Dr-Crow/esphome-ge-laundry-uart/case/rev3c/analytical/README.md

# Parametric Rev3C enclosure review

This is an editable analytical derivative of the [recovered prototype](../prototype/). It keeps a common base, module-specific C3/C6 lids and three light guides. The selected carrier outline and both appliance power inputs are preserved. The four lids support internal/external antenna concepts; exact cable, switch and printed-assembly qualification remains open.

**Use review exports for dimensional review and coupons. They are not approved production files.** Fixed original button reaches fail nominal actuation at an installed stack of 11.0 mm. The common closure permits a wrong lid: a C3 BOOT foot can contact C6 U.FL. Check the module label before assembly; labels do not mechanically prevent this mistake.

The [source-bound report](review/CASE-ANALYSIS.md) records valid solids, installed-stack samples, component envelopes, actual guide routes, plug gauges and antenna provisions. Analytical geometry was generated with build123d 0.10.0 / cadquery-ocp 7.8.1.1.post1. The original analysis used a different toolchain from the recovered historical requirements; the subsequent pinned reproduction is recorded below. These versioned checks are not physical fit, material or RF tests.

The [subsequent pinned reproduction](review/pinned-reproduction/GE-Pinned-CAD-Reproduction-2026-10-05.md) closes that setup/reproduction limitation for the frozen 77f4c88 source. build123d 0.11.1/trimesh 5.1.0 produces 51 independently checked STEP/STL pairs, and the 20 nominal shape comparisons and 12 stack samples agree with the prior engine. The original two top-level requirements do not establish the old transitive dependency closure; all 47 packages used in the new run are recorded. Future parameter/source changes require their own checks. Printed fit and physical qualification remain open.

## Reviewable corrections

- `configure()` sets the declared generic installed stack from 10.35 to 11.65 mm, independent BOOT/RESET heights, gaps and stops, plus optional stack-adjusted USB height. It does not establish a safe switch overtravel limit.
- A separate C3 leaf-root offset of 17.3 mm, instead of 16.6 mm, lowers the nominal fixed-guided strain screen to 0.427–0.495%. This meets the stated example screen, with material/fatigue and tolerance margin still unproved.
- `pipe_with_cap_relief()` removes only local lower crescents near manufacturer maximum capacitor bodies. The chosen 0.15 mm solder-lift allowance and 0.25 mm clearance are design requirements. The nominal LED inlet projection, upper path and roof retention stay unchanged; reduced inlet area needs optical/print testing.

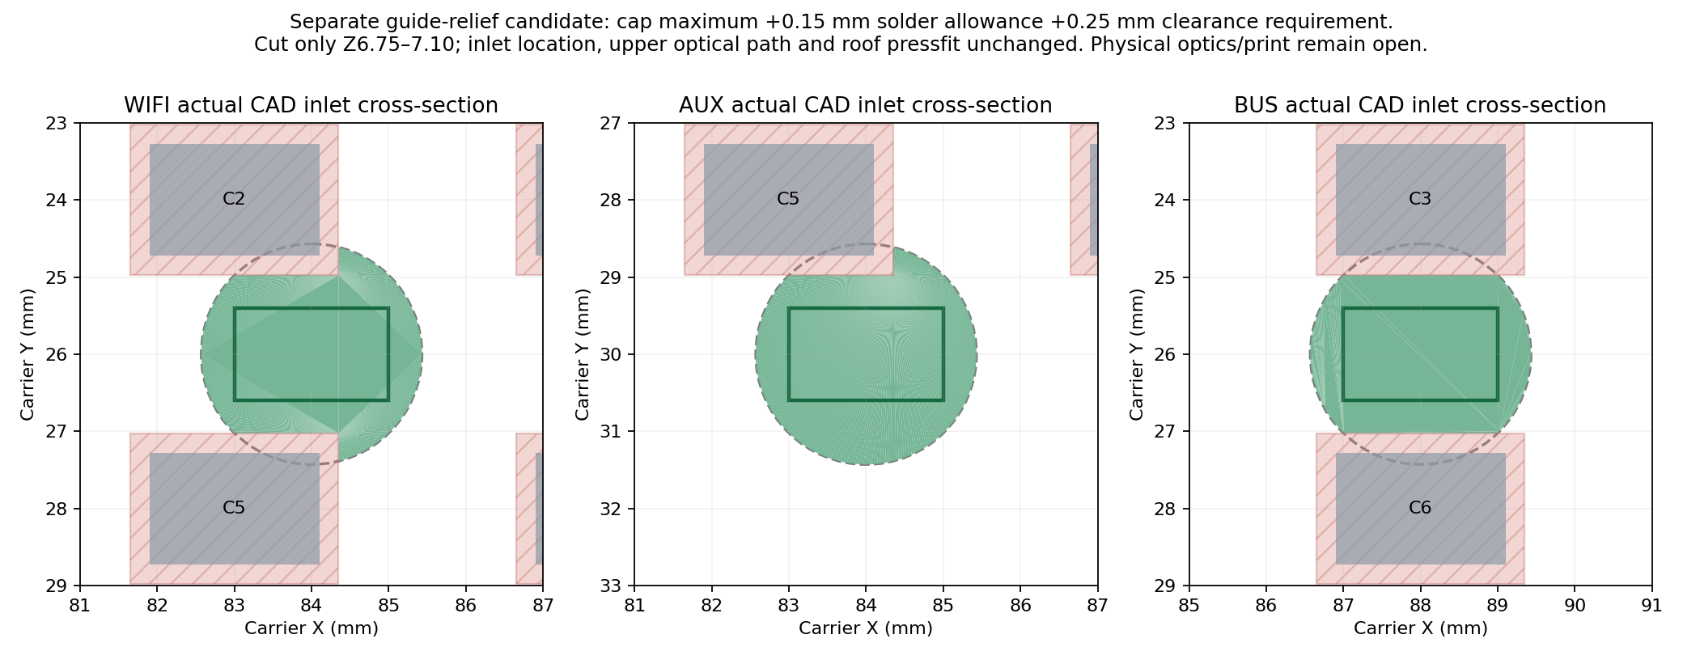
[picture p13: case/rev3c/analytical/review/guide-relief-candidate.png]
Guide relief and preserved LED inlet


## Explicit review export

Use an existing authorized installation of the recorded analysis tools. `export_review.py` requires an explicit module, stack and switch/stop dimensions so a known-bad default is not silently presented as a print-ready assembly. An illustrative C3 command is:

```sh
python export_review.py --module c3 --stack 11.325 \
  --boot-height 1.5 --reset-height 1.5 --boot-stop 0.4 --reset-stop 0.4 \
  --leaf-offset 17.3 --relieved-guides --output exports-review-c3
```

Those are conditional analytical parameters, not measured switch limits or a recommended production calibration. For C6, use its separately verified switch identity and dimensions. The report's 0.53 ±0.10 mm C6 height remains conditional; the nominal 0.36 mm stop is not a manufacturer overtravel allowance. The export includes the explicit parameter/source receipt and five review pieces. Extra coupons or proxy electronics are excluded from that five-piece set.

## Current dimension review

The [October 5 dimensions review](MECHANICAL-DIMENSIONS.md) binds socket maximum dimensions, the full declared 10.35–11.65 mm assumed-stack range, conditional switch identities and the named StarTech USB2CC2M cable. Its 12.2 × 6.5 mm maximum overmold exceeds the old synthetic gauge. The actual fitted header, C6 switch identity and native USB mating coordinates remain unresolved.

The [named cable tool and sensitivity receipts](review/cable-corridor/README.md) require explicit shoulder/axis coordinates and retain the source uncertainty. Named switch-height references are also available without changing the fitted default.

## Open assembly checks

The historical maximum-body and base/lid screens cleared at three sampled stacks within 11.0–11.65 mm. The [subsequent source-bound endpoint check](review/socket-stack-endpoints.json) passes eight C3/C6 × internal/external × lower/upper cases with maximum socket bodies and conditional switch-height extremes. All have zero nominal component/base-lid intersections and 0.25 mm released button gaps. Four lower-end lids also pass STEP single-solid and untouched watertight STL readback. These are explicit review parameters, not factory seating or safe-actuation proof. A 12 ×6 mm synthetic USB plug gauge clears; a 14 ×8 mm gauge fails the rounded aperture. Choose a real plug and verify shank depth, strain relief, insertion and finger/latch access. Antenna maximum slabs and nominal bulkhead hardware clear their stated screens, while cable terminations, bend/slack, panel tolerance and RF remain open.

Before fitting a board, verify the actual male/female header seating and retention, both switch make/overtravel/force specifications, wrong-lid prevention, slicer/coupon clearances, light transmission and actual antenna/plug envelopes. Leave UART VCC disconnected. Disconnect the appliance cable before powered USB. The 40 V switch selection is not a 40 V rating for the complete carrier.
