Dr-Crow/esphome-ge-laundry-uart/pcb/rev3/production/README.md

# Rev3A quote package

This directory is a quote and prototype artifact, not production authorization.
Upload the matching Gerber ZIP, BOM, and CPL as one revisioned set.

- `GERBER-GEA-Adapter-Rev3A.zip`
- `BOM-GEA-Adapter-Rev3A.csv`
- `CPL-GEA-Adapter-Rev3A.csv`

- The Gerber ZIP defines copper, solder mask, silkscreen, board outline, and
  plated/non-plated drills.
- The BOM maps fitted references to exact parts and quantities.
- The CPL supplies fitted-part coordinates, side, and rotation using JLCPCB's
  documented `Designator`, `Mid X`, `Mid Y`, `Rotation`, and `Layer` headers.

A valid turnkey upload must show all 43 BOM groups and all 91 placements selected
for assembly. Stop if the vendor marks any fitted row "do not place" or reports an
unselected part. The pre-J2 2026-09-15 match used stocked Yageo `C106243` and
`C91185` capacitors in place of unavailable `C28233` and `C28323`, while retaining
the available original `C17414` resistors and `C151607` buffers. Five boards quoted
at $141.24 before shipping and tax ($28.25 each). That price covered 42 groups / 90
placements. Based on J2's 2026-09-15 $0.05 catalog price, one $3 Extended-component
fee, and 30 additional SMT joints, the updated package is estimated at $144.54 total
($28.91 each) before shipping and tax. Refresh the upload to replace that arithmetic
estimate with a vendor quote. Review every replacement against
the original electrical ratings, package, pinout, temperature rating, and
manufacturer data; stock and pricing remain quote-time values.

J1 is the appliance-facing, through-hole EVERCOM `5301-8P8C` connector. A turnkey
quote must include it and show the correct orientation and through-hole assembly
method. DNP service/test items are intentionally excluded from BOM and CPL.

J2 is the populated top-side hanxia `HX PZ-2.54-02-03-S-PB3.2` (`C42391552`)
2-by-3 recovery header. The vendor preview must show it installed on the top side at
the lower-left recovery location. J3 remains a schematic-only DNP alternate and is
excluded from BOM and CPL.

J4 is the SHOU HAN `TYPE-C 16PIN 2MD(073)` (`C2765186`) USB-C receptacle. Its
official drawing was checked against the placed KiCad land pattern before the
live Economic Assembly quote. The vendor preview must still confirm its position
and orientation.

The PCB is 88.7 mm by 40.0 mm with four copper layers. The Gerber set must contain
`F.Cu`, `In1.Cu`, `In2.Cu`, and `B.Cu`; both inner layers are solid GND planes.
The plated drill file has a 0.30 mm minimum: twelve 0.30 mm drills connect U2's
thermal-ground pad, while routed vias use 0.40 mm drills. Quote this as standard
FR4 TG135 with the 0.30 mm minimum-hole option and ordinary electrical testing.
Stop if the upload requests a small-hole, high-Tg, filled-via, or four-wire Kelvin
process; those options are not required by this design and indicate a file or quote
configuration mismatch.

Do not order or connect a board to an appliance until the owner reviews the vendor
board, drill, parts, and placement previews. After fabrication, the current-limited
checks in [BRINGUP.md](../BRINGUP.md) must prove USB operation, all eight power-source
states, reverse-current isolation, regulator headroom, rail stability, temperature,
transient behavior, enclosure fit, and installed Wi-Fi performance.
