Dr-Crow/esphome-ge-laundry-uart/docs/revision-comparison/FINISH-PLAN.md

# Finish plan and outstanding work

Latest October 5 pre-order analysis and committed fixes: [all-revision review](preorder-2026-10-05/README.md). Earlier checkpoint/quote/source boundaries below remain explicit.

[Comparison](README.md) · [Current validation](VALIDATION.md) · [Exact checkpoints](HANDOFF.md) · [Quote comparison](PRICING.md)

Updated October 5, 2026 after shared-enclosure source recovery. Selected Rev3C retains the rated electrical design, corrected J1 CPL and stencil cleanup from `b87d3e8`; its fresh exact-part quote is $134.64/5 and $168.92/10. Published integration checkpoint `11826a7` passes hosted native/intended-rule checks for all seven revisions, 28 tests and eight actual firmware builds. Rev3B protection is reviewed at `ce2979b`; Rev3A rated protection and exact connector lands remain independently reviewed. Older revisions retain their separate architectures. The [Rev3C prototype qualification plan](../../pcb/rev3c/PROTOTYPE-QUALIFICATION.md) gives the next bounded sequence; orders, physical testing, PRs and upstream publication remain separate decisions.

## Current Rev3 milestone and remaining work

The [current refinement](preorder-2026-10-05/README.md#current-rev3-refinement-checkpoint) applies STPS140Z D14/D15 to all A/B/C and maximum-body socket/case corrections to C. Exact bf5c231 passes native KiCad 9.0.9, intended rules, 38 tests and eight firmware builds. Current-ST C quotes are $135.81/five and $171.20/ten; older A/B/C quote records below retain their original sources. A refresh is complete at $180.08/five or $230.15/ten, including its WROOM; B remains blocked only by exact-module stock, without a full assembled total. Future engineering is Rev3-only; prior Rev1/Rev2.x history and unresolved findings remain preserved, and upstream Rev2.2 receives no new redesign.

Feasible analytical work now completed includes source/purchasing corrections, current numbered signal nets, named switch-height references, full assumed stack endpoints, maximum socket courtyards, explicit-coordinate USB cable screening and a preserved separate plastic pair-key option. Remaining vendor inputs are actual factory header/module/switch revision, engagement/retention/make/overtravel limits, native USB mating coordinates and the buffer's output-range clarification. Common versus keyed base/lid pairs is a user choice; the latter requires changing both base and lid when switching module family.

OEM source/current/fault and loaded-voltage/thermal/RF/print/optical/assembly qualification remain distinct physical gates. Larger fuses, current-limit changes, fault-aware priority, regulators or added USB hardware are not silently adopted. Both appliance inputs and existing automatic priority stay required. Current supplier pose, solder/paste and process approval remains open.

## Historical checkpoint registry

| Work | Current checkpoint | Closeout evidence | State |
| --- | --- | --- | --- |
| Selected Rev3C final source package | 83-reference source; native/intended-rule/CAM/BOM/CPL checks pass; corrected-stencil exact-part quote refreshed October 5; partial C3/C6 models preserved | Final source/export hashes, intended-netclass and antenna proofs, supplier placement/process review; qualify switch/fuse/TVS/gate/diode/buck/module chain | Digital package and quote available; electrical/physical release blocked |
| Common C3/C6 enclosure | [Editable all-printed source](../../case/rev3c/README.md) recovered; useful XY datums and intact exports, historical electronic proxies and conflicting provisional Z assumptions | Register selected component envelopes; calibrate actual socket/module/button heights, printing, retention, USB/RJ45, antenna/pigtail clearance and fit | Source recovered; current-board geometry, printing and physical qualification outstanding |
| Focused Rev3A protection backport | `615863d`:97 refs, all native findings 0, independently reviewed source/body-CPL/CAM and 14 pixel views; exact complete97-row quote $178.90/5, $227.86/10 | Actual source/load/retry/thermal/USB isolation; J4 solder delivery/inspection/retention, TP12/annulus/stencil/fill process; module/case/RF | Digital backport and quote complete; process/physical release blocked |
| Focused Rev3B protection backport | `ce2979b` has all-zero native counts,85 fitted references; independent review complete | Exact U2 module stock is unavailable in supplier 5/10 quotes; qualify typed J1/U2 body datum, soldered C3 sourcing/install, loaded power/thermal/USB behavior, local copper/ground-fill effects and actual case | Digital backport complete; supplier/physical release gates open |
| Rev1.0 distinct closeout | Current `53a4b3d`, native 0 findings,166 physical tuples unchanged; independent receipt/current CAM complete; two classic profiles built | Preserve original archives and reviewed current exports; resolve original BOM/CPL procurement absence; review original PIN1/external-buck path and actual 38-pin module | Digital closeout complete; procurement/power/module/physical gates open |
| Rev2.0 distinct closeout | Current `5c8afe4`, native 0 findings,186 physical tuples unchanged; independent receipt/current CAM complete | Preserve original archives and source-bound current CAM; qualify supplier rotations; review manual selector, linear regulators/protection, UART perspective and service power | Digital closeout complete; assembly/power/physical gates open |
| Rev2.1 / Rev2.2 distinct closeout | Restored final `3d985593` / `b00c96f`, fresh native/CAM/assembly/paste checks pass; 60 / 59 references | Keep manual selector/legacy architecture; supplier review of Rev2.1's three source-bound pad-center conventions; current-source protection/current/thermal and recovery checks | Digital cleanup available; placement/power/physical gates open |
| Focused candidate packaging | Per-revision hardware, shared/classic firmware, universal CI and canonical docs | Keep each review unit coherent, exact source/export hashes and warning limits included; verify integrated source without conflating historical galleries/quotes | Focused heads preserved; combined source published at `11826a7`; upstream submission remains pending |
| Universal CI and hosted checks | Restored standalone `0d3358a`; new integration has seven sources/eight profiles/380 dependencies and28 regression tests; historical `f85ba98` ancestry remains incomplete | Keep legacy BOM/CPL absence and all 21 physical/source/power gates explicit; run fresh pinned containers and exact hosted jobs after permitted fork publication | Fresh source/test/native/CAM/rules/schema checks complete; published `2d5a42c` hosted native/rules/tests and eight config/compile checks pass; supplier/readiness gates remain explicitly red |

A successful quote, native pass or compilation cannot close the electrical/physical rows. No older revision is an established safe fallback. Any backport changes the source checkpoint and requires regenerated source-bound evidence; do not reuse Rev3C's passes as Rev3A/B proof.

## Remaining dependency boundaries

- Local documentation, proposed PR descriptions, source-bound manifests and durable source/PDF preservation can be completed now. The source-matched drill-marker stencil defect has been corrected and regression-tested; additional physical/process checks remain.
- Shared all-printed editable CAD is recovered from the intact source archive and preserved under `case/rev3c/prototype`. Its original proxies omit the selected protection-part envelopes, and its provisional Z stack differs from the current board preview. Actual module/button/header dimensions, source reconciliation and prints are required for physical qualification. Old C3-only geometry is not a shared default.
- Target appliance model, source voltage/current/transient envelope and a reviewed bench procedure are required for startup/load/retry/thermal/RF/appliance tests. No physical test has occurred.
- Supplier part stock, footprint-zero/pin1 and assembly process remain gates. Rev3A's quote is complete but J4 solder/retention is unapproved; Rev3B's exact module is unavailable. Rev1's recovered prose purchasing table does not provide a qualified current supplier pair; Rev2's 60 archived component codes need explicit value/identity/rotation review before a current supplier package can be declared.
- Normal fork backup publication is complete on `integration/ge-restored-final-2026-10-04`. Hosted native/rules/tests and eight real firmware builds pass at exact `11826a7`; the committed detailed firmware artifact receipt remains explicitly bound to earlier `2d5a42c`. Legacy supplier inventory/manufacturing gaps and all 21 release gates remain red. Local firmware installation remains unavailable. PR creation/upstream submission, merge and orders are separate future actions; no physical qualification is inferred.

## Legacy sourcing decision

Before any Rev2.0/2.1 order, resolve the [confirmed resistor-code conflicts](LEGACY-SOURCING.md): declared 220k/4.7k versus historically coded 200k/47k. The later matching codes are documented as evidence, not selected replacements. Review historical diode pin labels and regulator aliases using physical numbered pins. Rev1's prose purchasing history can aid completion, but its unresolved values, packages, module identities and population choices still prevent a qualified supplier package. No gate or rule is waived.

## Physical qualification checklist

1. Identify the actual appliance model and purchased module/buck revisions. Measure loaded source voltage/current allowance and relevant transient/pulse energy across the intended operating envelope.
2. Check each input separately and both together: reverse polarity, PIN1 presence priority, startup/dropout, switch current limit/retry, brownout and recovery. Verify differential/gate and protection/fuse coordination under reviewed fault conditions.
3. Measure the complete supply path at cold/hot startup, inrush and Wi-Fi peaks: fuse/PMOS/switch/OR/buck/output diode/module rails, load margin and temperatures. Define acceptance limits from the exact parts and actual source.
4. Review supplier rotations, pin 1, diode/zener polarity, exposed-pad/stencil and through-hole/socket process. Resolve Rev3A's clearance/finished-annulus margins and Rev2.1 placement conventions before assembly approval.
5. Verify one-source USB/UART behavior, with UART VCC disconnected. Check Rev3A's distinct USB-isolation paths separately; do not assume them on XIAO carriers. Confirm reset/BOOT/recovery and ROM UART effects on the appliance interface.
6. Match the correct classic/C3/C6 GEA2/GEA3 profile to the actual board. Check actual appliance entities, bus reliability, startup/reconnect and functional behavior; compilation alone is insufficient.
7. Reconcile and print the recovered enclosure using the selected board and actual module dimensions. Test orientation, all 14 socket contacts/retention, stack height, vibration, USB, BOOT/RESET actuator travel, antenna/pigtail clearance, RF and temperature with the actual module; C3/C6 require their own lids.
8. Record measured results, instruments, acceptance criteria, assembly/source revisions and evidence hashes. Only current-source qualified evidence can release the corresponding gate; later ordering requires final stock/placement review and user approval of the complete landed purchase.

The comparison galleries and old charts remain historical. A later PDF should summarize these canonical Markdown files and their current source identities, rather than become a separate status authority.
