Dr-Crow/esphome-ge-laundry-uart/pcb/rev3a/RATED-PROTECTION.md

# Rev3A rated-protection backport

This branch backports the selected Rev3C protection circuit (selected source `fafd3eab5a8a8465697e1557bb075d88f85be9d9`, electrical review `7bb455fbc85c748f3125ed091a54375de69fbbcc`) onto frozen Rev3A clearance source `d1769b25c206fe86f60e37c415d4a60da7bb8334`. Rev3A retains its integrated AP2112K-3.3/ESP32-C3-WROOM-02 architecture and original USB circuitry. Both GE inputs and original automatic PIN1-presence priority remain. This is a prototype protection backport, not a 40 V carrier rating or proof of an OEM failure.

**Digital source status:** genuine KiCad 9.0.9 reports zero ERC errors/warnings and zero DRC errors/warnings/unconnected/parity, including all severities and expanded track checking. Native source, BOM, explicitly reviewed body-datum CPL, copper/drill archive, schematic and board review assets are paired in [the current manifest](validation/rated-protection-manifest.json). Independent review and exact supplier/process acceptance remain separate gates.

## Reviewed protection circuit

- Q3/Q4 retain CJ3407, with source pin 2 at the protected node and drain pin 3 at the fused input. R31/R32 remain 5.1 kΩ, now pulling the gate-bias node to GND; C18/C19 remain 100 pF referenced to the protected source. R33/R34 remain 51 Ω between bias and gate.
- Frozen Rev3A fitted D16/D17 as MBR0540-TP/C78744 Schottky diodes. They now become exact MCC BZT52C12-TP/C668891 zeners, cathode pin 1 at their respective protected source and anode pin 2 at gate-bias. This is the reviewed nominal 12 V source-referenced gate clamp, including the MCC low-current/temperature/dynamic qualification limitations below.
- F1/F2 become exact Littelfuse 1812L075/33DR/C151170. Manufacturer page 6 specifies 1.78 mm pad length ×3.15 mm width and 3.45 mm inner gap; pad centres are±2.615 mm, overall span7.01 mm. The exact wider lands, placement and routing deltas are enumerated in the source-bound proof.
- U9/U10 become exact TPS1H200AQDGNRQ1/C2653785. VS8 is protected input, OUT7 is switched output; DELAY5 is modeled as bidirectional I/O as TI page 3 specifies; U9 IN1 follows its own VS, U10 IN1 retains the original R36/Q5 PIN1-presence priority network. DIAG_EN2/GND6/EP9 are GND; FAULT3 is NC.
- Removed C22/C23 CT capacitors become R39/R40, exact 3.3 kΩ ±1% 0603WAF3301T5E/C22978 CL-to-GND resistors. R41/R42 are exact 100 kΩ ±1% 0805W8F1003T5E/C149504, own-VS-to-DELAY resistors using TI's standalone retry connection. Existing R38 remains the USB 220 kΩ discharge resistor.
- D19 adds SUNMATE SMF16A/C399290 on PIN3_PROTECTED, matching D18's protected-node TVS function/polarity. Both remain upstream of switch current limiting. Supplier package is SOD-123FL; the retained native land is D_SOD-123F. The [actual drawing/land review](validation/sunmate-land-review/SUNMATE-LAND-REVIEW.md) preserves the printed terminal E-min 0.097 mm ambiguity. A centred maximum terminal envelope gives 99.8716% overlap on the rounded pads, with 0.000700974 mm² corner loss; full containment or equal package names is not claimed. Placement, rotation, paste, fabrication and thermal acceptance remain gates.

PIN1-presence priority is retained, including inhibition of PIN3 by a weak or faulting PIN1. No fault-aware fallback, manual input selector, new regulator or USB path is introduced. Existing connector/module/LED/JP1/mount/case interfaces and firmware remain fixed; internal DNP power-test pads may move under the explicitly authorized fit work and must be identified in the current diagrams.

## Manufacturer lands and rule scope

TI Rev E May 2026 DGN0008K-C01 page 28 specifies1.4×0.45 mm lead pads on0.65 mm pitch, giving0.20 mm intrinsic adjacent pad gaps, with 4.4 mm row spacing. Two rules apply0.20 mm only to two pads belonging to the same U9 or the same U10 footprint. Original global, Power 0.25 mm, Switching 0.30 mm, track/via and USB rules remain. No routing or via waiver is implied.

EP copper is 2×3 mm with 1.57×1.89 mm mask-defined opening/paste aperture. The 85% coverage criterion applies to the exposed mating/process area rather than the mask-covered copper extension. The full aperture follows TI's0.125 mm stencil example; optional under-paste vias are omitted. External ground vias must remain outside paste. Vendor lands establish intended package geometry, not universal insulation/environmental or assembly approval. Stencil, solder coverage, contamination, process and actual thermal performance remain gates. Added package STEP envelopes are approximate maximum-size models, not authenticated supplier CAD.

## Current limit, retry and supply margin

Nominal CL is 2000/3300=0.606 A. TI's conditional ±15% combined with ±1% resistor gives about 0.510–0.704 A, requiring VS−OUT≥2.5 V and the stated setting/test conditions. This is a provisional engineering budget, not an OEM allowance or unconditional normal draw ceiling. At 85 °C the resistor's±100 ppm/K reference broadens the partial estimate to about 0.507–0.708 A; source allowance, copper, diode, fuse and module limits remain separate.

Continued limit produces35–45 ms ON/0.8–1.2 s OFF, 40 ms/1 s typical, specified by design with thermal interaction. The old CT ramp is not an equivalent function. Unloaded0.510 A×35 ms≈17.9 mC arithmetic and AP63205's typical 4 ms soft start do not prove loaded startup. Local VS must remain above the maximum 4 V restart threshold. Startup, foldback, delayed EN, RF peaks, both handoffs and all eight GE/USB states require measurement.

The selected-part mixed-condition illustration adds about 86 mV path loss at 364 mA versus the former fuse/FET/switch choice. This reduces headroom when the buck is in dropout; it does not automatically reduce a regulated3.3 V rail by 86 mV. The conditional 5 mA switch-bias reference versus 85 µA adds 4.915 mA upstream of VS; using pre-VS fuse+PMOS0.487 Ω gives 2.394 mV additional loss, not switch-channel resistance or a direct subtraction from OUT CL. These references are not matched guaranteed corners.

Rev3A's AP63205→D11→AP2112K path is evaluated separately in [POWER-QUALIFICATION.md](POWER-QUALIFICATION.md). Nominal 5 V loaded operation remains an intended qualification case; no lower input is excluded to force a pass. The integrated LDO, its thermal behavior and original reset architecture are retained, with the bounded EN capacitor correction below.

## Source-referenced gate and whole-chain bounds

The MCC primary Rev3-4-12012020 sheet gives 11.4–12.7 V at 5 mA/25°C, Zzt25 Ω@5 mA and Zzk150 Ω@1 mA. Its6–10 mV/K coefficient is typical at unspecified IZTC; comparable capacitance/surge guarantees are absent. At illustrative 26 V/12 V/5.1 kΩ, bias is 2.745 mA and dissipation32.9 mW, below 5 mA characterization. The specified 5 mA voltage bound must not be inherited at actual bias. Steady V²/(4R) gives 33.14 mW nominal/33.47 mW at −1%R; this does not bound fast/hot VGS.500 mW at 25 °C derates to 100 mW at 125 °C under stated conditions;250 °C/W is a reference, not a board thermal prediction.

SMF16A's26 V clamp belongs to 7.7 A,10/1000 µs,25 °C. Actual waveform/source impedance/energy/overshoot/repetition remain unknown. TPS1H200A's 40 V addresses the former20 V switch versus that bounded positive-pulse comparison; retained PMOS30 V VDS/±20 V VGS, AP63205≤32 V operating,33 V PPTC differential voltage and capacitors remain independent limits. Charged26 V protected source followed by −13.6 V at the PMOS drain gives 39.6 V differential, beyond the PMOS; reverse-step qualification remains open. Switch CL does not limit upstream TVS current, and 0.20 s PPTC trip at 8 A does not prove sustained-overvoltage TVS survival.

## EN RC and recoverable-warning cleanup

C26 is exact Yageo CC0805KKX7R9BB105/C91185,1 µF ±10%, 50 V X7R 0805, EN→GND with original 10 kΩ R3 unchanged. It implements Espressif's C3 external RC recommendation. Ideal stable, uncharged3.3 V step timing is 2.877 ms to 0.25 VDD/13.863 ms to 0.75 VDD; initial R ±1%/C ±10% variation gives 8.91–11.11 ms time constants. Bias, aging, temperature/loading and residual-charge effects remain unmeasured.

The capacitor stores3.3 µC/5.445 µJ at 3.3 V; steady reset current is 0.330 mA, but instantaneous discharge current goes directly through the switch/programmer and is not limited by R3. An illustrative 100 Ω sink needs about 140 µs to reach low plus≥50 µs low hold, so a50 µs command is not automatically a valid reset. Hold BOOT through delayed EN rise and the 3 ms strap-hold requirement, preferably until the downloader starts. EN can stay charged during a rail dip; this RC is not a brownout supervisor. Actual switch/programmer capability, EN/VDD relationship, manual recovery and native USB behavior remain measurement gates.

Thirty-five historical symbol definitions are recovered exactly into a local library, removing44 library-mismatch warnings without changing pins, names/types, geometry, wires or net groups. Eight original USB metric-anchor grid warnings remain explicit at J4/U7/R26/R27/F3/R28/R29/D10; choosing a tiny0.005 mm global grid merely to erase them is unjustified. Existing25 mil metadata stays. Original hidden VCC/+5 V alias remains visible. The five original footprint mismatches at D2, C5, SW2, TP13 and U2 are cleared by recovering their exact frozen embedded definitions in LegacyBoard and pairing their full footprint IDs in schematic/PCB. Independent recovery proof preserves every pad, graphic, model, placement and attribute. No unrelated stock geometry, severity or exclusion changes are used.

## Retry contact and reference-plane review

R42 retains its exact 100 kΩ part and own-VS supply. Its accepted DELAY contact
uses one 0.7/0.3 mm through-via with 0.20 mm annulus at (58.75,33.2), one front
stub and a 12 mm link on In1. Nominal drill-to-paste gap is 0.175 mm; native gaps
are 0.277683 mm to V_INPUT (Power 0.25) and 0.350000 mm to the gate route
(Default 0.20). The finite D6 segment is 0.411864 mm away. Finished drilling,
mask/placement/stencil alignment, tenting and reflow remain process gates.

This creates a real 9.959915 mm² In1 ground slot. The filled plane remains one
connected component, but its reference geometry changes. No original USBData
or Switching route, or RF rule area, projects across the cut. Eleven original
other power/low-speed items do; their return paths and actual RF/USB/transient/
thermal behavior require qualification. The new via removes 2.017663 mm² from
In2 locally. The identical proposed link on B or In2 has three native errors,
so those exact alternatives were rejected. No source rule or retained signal
route was changed to accept this retry contact. The original continuous-reference
claim must not be inherited from a DRC result.

## Final layout, process and placement review

Ten original component poses change in the authorized local protection region; all fixed connector/module/LED/JP1/mount/case poses and firmware remain. Original USB differential data copper is unchanged; the separately authorized same-part J4 shell-land repair and short CC1 rejoin are enumerated below. The [complete pad/net/copper delta](validation/rated-protection-proof.json) distinguishes unchanged physical copper from UUID restoration. Local intermediate GE receive/FullTx copper rejoins and plane refills are enumerated; direct connector/module net membership alone does not prove every intermediate signal or reference route stayed unchanged.

The original DNP test points retain their standard footprint, net, exclusion and probing function. TP8 stays(49,11); TP9 moves(49,27)→(44.5,30.7), and TP11 moves(55.5,27)→(45.7,33.2). TP9 retains its1mm copper/2mm courtyard/no-paste probe land. No fixture/published-coordinate dependency was found in the repository search; current source-bound diagrams show the changed access positions. Probe/fixture/enclosure accessibility remains a physical gate.

New routed vias retain0.20 mm radial rings with either0.8/0.4 or0.7/0.3 mm diameter/drill. The existing ten clearance-repair via rings remain0.14/0.16 mm under unchanged native rules. U10's existing external ground via was moved0.15 mm to(57.5,28.65), improving nominal hole-to-R40 paste from0.025735 to0.175544 mm; its EP-paste hole gap is0.705001 mm. The fused .7/.3 mm via at(51.5,27) has0.300001 mm foreign copper and0.500001 mm hole-to-paste spacing, but sits under retained Q4 plastic with no guaranteed positive standoff. CAD tenting does not guarantee finish, mask registration, solder intrusion, body seating or coplanarity. R42's0.175 mm hole-to-paste clearance and original TP12's0.2502 mm Power gap are tolerance/process gates, not manufacturing margins proved by DRC.

Every fitted placement anchor is screened for asymmetric copper/Fab bounds. J1, J4 and U2 receive explicit primary body/pin1 review in [typed datum evidence](validation/placement-origin-review.json). J1 nominal body centre is CPL(8.645,−17.000) at unchanged−90°; the retained older approximate J1 envelope is not the exact body datum. U2's full18×20mm module body centre is CPL(84.7,−17),3.1mm from native anchor(81.6,−17), at unchanged−90°. J4's exact SHOU HAN8.94×7.35mm body is centred at native CPL(72,−36.325),0°. The other94 anchors retain centred copper/Fab screening; this does not authenticate every supplier pick/reel origin. CPL geometric-centroid transforms are explicit and must be checked against actual supplier library zero, pin1, orientation and process before assembly acceptance.

The exact SHOU HAN RevA drawing recommends0.80 mm PCB versus the retained1.60 mm board; its top-mount body seats without a demonstrated collision. The authorized same-part repair enlarges only the two forward shell slots0.60×1.20→0.60×1.40 mm and copper1.00×1.60→1.00×1.80 mm at fixed local centres±4.320,+1.075, matching the manufacturer drawing. Rear shell/locator/signal-pad geometry and every pin net remain. Signal lands retain1.30 mm height because the primary1.17 mm callout conflicts adjacent1.15 mm dimensions; stencil acceptance remains open. Shell pads retain all-copper/all-mask with no invented paste. Exact local OnionStraws metadata replaces the misleading HCTL5A description with selected SHOU HAN3A/5V, and rebinds only the unchanged0.18 mm locating-hole rule to the new same-J4 ID. Two internal CC1B bend anchors move0.2412 mm downward across three retained0.2 mm segments to meet unchanged clearance; boundary endpoints, vias and differential USB data copper stay. Forward tab0.8±0.15 mm fits the corrected nominal1.40 mm slot, but~1.00 mm legs end inside the1.6 mm PTH under the seating interpretation. Actual pin-in-paste or other assembler-approved solder delivery, joint inspection, retention/finish/process acceptance remain concrete gates. The retained locally named6-pin STEP is approximate and is not exact16-contact supplier evidence. No exact USB connector assembly qualification is claimed.

U9 VS-to-C20's inherited routed connection after placement was40.87631 mm. A native-proved4.981967mm0.5 mm In2 tie now joins their existing vias directly. Only six previously-added R13 detour pieces are rejoined at unchanged boundary anchors(60.15,7.35)→(63.45,10), using its existing layer-transition vias; no additional vias/part moves or original copper removals are introduced by this correction. C20 GND retains a1.47749 mm front contact to the existing0.8/0.4 mm GND via. The new R13 rejoin is33.575725 mm on B/In2; this preserves In1 from an extra bypass slot. It establishes a local supply contact, not parasitic/thermal/transient qualification.

Full native fill comparison against the frozen clearance base records actual nonlocal propagation: GND copper removed/added is F85.7755/60.3857mm², B44.0690/155.6025mm², In158.1651/15.3470mm², In2346.6127/11.8740mm². F removed-region bounds reachx85.6372mm and In2 added reachx85.4298mm. These include all repair/via/refill changes; the R42 slot's incremental9.959915mm² is a separate contact-stage measurement. No whole-plane/reference-preservation or strictly local physical-change claim follows from native zero-errors. Final RF/USB/return/thermal/crosstalk/transient qualification remains open. Full polygons are in [the fill delta](validation/rated-protection-fill-delta.json).

## Procurement and release state

The protection backport adds three fitted parts net; C26 adds one more, 93→97. Native BOM has 49 exact-value/full-footprint groups and 42 purchasing tuples, paired to exactly 97 top-side CPL references. Five historical per-reference footprint IDs split three exact-value groups without changing quantities or purchasing identities. Existing C91185 is reused rather than adding a unique capacitor selection. The [dated exact-part review](validation/rated-protection-sourcing/review.md) observes all eight reviewed codes stocked on October 4 at 01:43–01:49 UTC. Twelve new/changed placements total $2.1646 per board at displayed JLC 1+ part prices, before the other 85 placements and assembly/process fees. This is an absolute selected-parts subtotal, not an incremental or complete A quote. Dated selected-C public part/assembly prices are comparison inputs: assembly groups, integrated module/LDO, remaining stock, fees, stencil/process, shipping and tax require a source-bound A quote. No supplier substitution, publication, order or physical test is performed here.

Primary sources: [TI Rev E](https://www.ti.com/lit/ds/symlink/tps1h200a-q1.pdf), [Littelfuse 1812L](https://www.littelfuse.com/assetdocs/resettable-ptcs-1812l-datasheet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), [MCC BZT52](https://www.mouser.com/datasheet/2/258/BZT52C2V4_7eBZT52C75_500mW__SOD_123_-2904721.pdf), [AP2112](https://www.diodes.com/datasheet/download/AP2112.pdf), [Espressif C3 design guideline](https://docs.espressif.com/projects/esp-hardware-design-guidelines/en/latest/esp32c3/schematic-checklist.html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), [exact Yageo capacitor](https://yageogroup.com/download/specsheet/CC0805KKX7R9BB105). The native CAD/plots, source-bound delta and actual physical tests address separate gates.
