Dr-Crow/esphome-ge-laundry-uart/pcb/rev3c/POWER-QUALIFICATION.md

# Selected Rev3C power qualification gates

This selected prototype adds the [rated-switch protection delta](RATED-SWITCH-OPTION.md) to frozen gate-corrected source 8f95555. It preserves both original input branches, automatic PIN1-presence priority, common AP63205 buck and C3/C6 interfaces. The40 V switch is a component choice for a bounded protection review; no observed OEM failure,40 V carrier rating, mandatory upgrade or manufacturing approval is established.

PIN1 remains J1.1→F2→Q3→U9→D14→V_INPUT. PIN3 remains J1.3→F1→Q4→U10→D15→V_INPUT. PIN1_PROTECTED still drives Q5 through R35/R37; Q5 pulls PIN3_EN low. With PIN1 absent, R36 pulls U10 IN high from its own protected source. Q5 senses presence rather than useful output, so weak/faulting PIN1 can inhibit healthy PIN3. This preserved behavior is not a new fault-aware fallback.

U9/U10 now use TPS1H200AQDGNRQ1, external3.3 kΩ CL resistors and100 kΩ own-VS DELAY pull-ups. F1/F2 use33 V1812L075/33DR; D20 adds the exact PIN3 SMF16A. Current limit is provisional0.606 A nominal, approximately0.510–0.704 A under the specified accuracy/resistor-tolerance assumptions; temperature drift and TI's VS−OUT≥2.5 V accuracy condition remain material. Continued limiting produces35–45 ms on /0.8–1.2 s off. It can cause repeated startup resets. Neither that setting nor a fuse/diode/buck rating establishes OEM source allowance. Full calculations, package-rule scope, startup/loss effects and whole-chain transient bounds are in the option report.

Close these gates before appliance connection or compatibility/manufacturing claims:

1. Establish the exact appliance model, pin map, nominal and loaded supply tolerance, current/peak allowance, source impedance, and positive/negative waveforms. Nominal5/7.5/9/13.6 V examples are not a universal source specification.
2. Bound all Q3/Q4 drain/source/gate differentials, switch/control pins, PPTC differential voltage, AP63205 input, clamp pulse energy/repetition and sustained-overvoltage behavior. SMF16A's26 V table clamp at7.7 A/10/1000 µs/25°C is not an all-condition guarantee. The retained30 V PMOS can exceed its differential rating during a charged-node reverse step.
3. On an isolated bench with reviewed source limits, measure PIN1-only, PIN3-only and both-input operation, original priority, weak PIN1, removal/recovery, startup/inrush and brownout. Verify both actual C3/C6 modules' VBUS/3V3 and bus logic throughout cold/hot starts and RF demand. Local switch VS must stay above its4 V maximum restart threshold. Do not reduce the intended input specification to force a pass.
4. Reconcile measured draw with OEM allowance, D14/D15 duty/thermal limits and enclosed hot PPTC hold. Measure effective capacitors, converter behavior and temperatures. The new path adds an illustrative86 mV at364 mA versus the former fuse/FET/switch selection, plus conditional milliamps of switch supply current. AP63205 remains a buck and cannot create missing low-input headroom or source power.
5. Approve TI's intrinsic0.20 mm pad-gap engineering rule for the actual environment, manufacturer PPTC lands, stencil, ≥85% final EP solder coverage and thermal process. Global/routing clearances remain unchanged. CAD clearance passes do not establish insulation, environmental or physical qualification.
6. Recheck exact MCC BZT52C12-TP/C668891 and UNI-ROYAL0805W8F1003T5E/C149504 availability and assembly/process fees before an approved order. The complete selected83-part quotes are recorded in [ORDERING.md](ORDERING.md); all references matched at five and ten carriers. The reviewed MCC alternative permits softer impedance and provides only a typical temperature coefficient; actual low-current/hot clamp, fast VGS and thermal behavior must be verified. Frozen80-part8f95555 and83-part46173b6 quote snapshots are unchanged. Verify physical mating height, retention, case/button/USB access and RF using actual modules and enclosure.

Both reviewed modules tie side-header VBUS to USB receptacle VBUS. Physically disconnect the appliance cable before powered USB, and remove USB before appliance use. Do not drive module3V3 or underside/battery pads; no battery load is included. Recovery uses module BOOT/RESET and native USB; J2/D19 remain absent.

Native CAD/source/manufacturing checks pass for review. Electrical, thermal, mechanical, RF, source and assembly qualification remain open. No appliance test or order has been performed.
