Dr-Crow/esphome-ge-laundry-uart/pcb/rev3c/RATED-SWITCH-OPTION.md

# Selected Rev3C rated-input prototype review

The project selected this TPS1H200A/33 V fuse design on October 3, 2026 after complete exact-part quote comparison. The electrical source reviewed and quoted is `7bb455fbc85c748f3125ed091a54375de69fbbcc`; its unchanged hardware remains a prototype with open source, startup, thermal, assembly and physical gates. It is not a 40 V appliance-port rating or an observed GE field-failure correction.

The design starts from frozen gate-corrected source `8f95555022eec353f8c9e3b9c54b612ee2541eaa`, preserving both original inputs, automatic PIN1 priority, buck, module interfaces and firmware. The source-corrected 80-part historical comparison is `ca1fdb1261af8b32a1bf353d37f40439ead5c3b0`. Current guide and complete prices: [ORDERING.md](ORDERING.md).

## Reviewable electrical change

- U9/U10 become exact **TI TPS1H200AQDGNRQ1 / C2653785**, rated 4–40 V at VS under the stated conditions. VS8 and OUT7 preserve the original protected input and switched output. U9 IN1 follows its own VS; U10 IN1 retains R36/Q5 automatic PIN1-presence priority. DIAG_EN2, GND6 and exposed pad9 connect to GND; FAULT3 is unconnected.
- C22/C23 timing capacitors are removed. R38/R39 are exact **UNI-ROYAL 0603WAF3301T5E / C22978**, 3.3 kΩ ±1% CL-to-GND resistors. R40/R41 are exact **0805W8F1003T5E / C149504**, 100 kΩ ±1% own-VS-to-DELAY resistors, following TI's standalone auto-retry connection. C149504 corrects the catalog identity previously recorded as C17407; manufacturer, MPN, value, rating, footprint and circuit are unchanged. The old CT ramp is not represented as an equivalent function.
- F1/F2 become exact **Littelfuse 1812L075/33DR / C151170**, on its manufacturer's suggested 1.78 × 3.15 mm pads with 3.45 mm inner gap. Both move 1.5 mm right to clear the wider pads. Local neighboring traces are rerouted without changing their pin nets.
- D20 adds exact **SUNMATE SMF16A / C399290** at PIN3_PROTECTED, matching D18. It remains upstream of the switch current limiter.
- D16/D17 use reviewed **MCC BZT52C12-TP / C668891**, a nominal 12 V SOD-123 gate zener. The former exact Nexperia C550251 selection remains in frozen8f95555; the current80-ref historical cost comparison ca1fdb1 also uses MCC. This sourcing correction changes four component metadata records only; all pin nets, copper, footprints, placements, rules and firmware are unchanged from optional candidate `46173b61546d1e51993c1376399b2614f3577df3`.

Both original PIN1 and PIN3 paths, their diode OR, the AP63205 buck, original Q5 priority network and corrected PMOS/source-referenced gate clamps remain. Q5 senses PIN1 presence, not useful output power. A weak or faulting PIN1 still can inhibit PIN3; no new automatic normal fallback is introduced. All 14 socket functions, 99 × 40 mm outline, mounting datums, module/USB/case interfaces and firmware sources remain.

## Reviewed gate-clamp sourcing correction

The [MCC-authored BZT52 sheet, Rev.3-4-12012020](https://www.mouser.com/datasheet/2/258/BZT52C2V4_7eBZT52C75_500mW__SOD_123_-2904721.pdf), pp1–3, supports the nominal voltage and package/polarity choice. Pin1 remains cathode at the respective protected PMOS source; pin2 remains anode at its gate-bias node. MCC's suggested pads are 0.91 ×1.22 mm with 2.36 mm inner gap and 4.18 mm overall span. Existing pads are 0.90 ×1.20 mm at ±1.65 mm, giving 2.40 mm gap and 4.20 mm overall span. Its 3.55–3.85 mm total length, 2.55–2.85 mm body length, 1.40–1.70 mm width and ≤1.35 mm height fit the existing SOD-123 envelope. No footprint edit is made; assembler polarity, placement tolerances and solder acceptance still require review. MCC marking is **WH**, with the cathode band facing pad1.

Both MCC and the [former Nexperia sheet](https://assets.nexperia.com/documents/data-sheet/BZT52_SER.pdf) specify 11.4–12.7 V at 5 mA/25°C and ≤0.1 µA leakage at 8 V. MCC permits **25 Ω at 5 mA /150 Ω at 1 mA**, versus Nexperia's 10 Ω /90 Ω. That permits a softer clamp. MCC's +6…+10 mV/K is explicitly **typical**, at an unspecified IZTC, and its sheet gives no comparable capacitance or surge rating. Nexperia's ≤85 pF and bounded temperature-coefficient wording cannot be inherited. This is a reviewed sourcing alternative, not a claim of identical dynamic behavior at every corner.

At an illustrative 26 V source and 12 V clamp, the retained 5.1 kΩ bias carries about2.745 mA and the zener dissipates about32.9 mW. That current is below the 5 mA voltage characterization: **11.4–12.7 V is not a guaranteed clamp range at actual bias**. Neglecting gate DC current, steady dissipation at 26 V is bounded by V²/(4R), about33.14 mW nominal or33.47 mW at −1% resistor tolerance; this does not bound VGS or transient energy. MCC's 500 mW at25°C derates linearly to zero at150°C, giving100 mW at125°C under the sheet's conditions. Its250°C/W implies an indicative8.3°C rise at33 mW, with mounting conditions unspecified. No board thermal upgrade is established. Low-current/hot clamp, actual gate-source fast peaks, Miller coupling, reverse steps and both branches' thermal behavior remain qualification gates. Neither the 26 V illustration nor a nominal12 V label expands the allowed source envelope.

The [corrected C149504 supplier identity](https://jlcpcb.com/partdetail/C149504) retains 100 kΩ ±1%,125 mW,150 V,±100 ppm/K and −55…155°C in0805. The supplier's October3,2026 live sourcing check reported Basic/Economic+Standard,4,204,330 direct stock and USD0.0059 at1. Its [C668891 check](https://jlcpcb.com/partdetail/C668891) reported MCC BZT52C12-TP, Extended/MSL1/Economic+Standard,48,100 stock/47,040 available and USD0.0277 at1. These are snapshots, not reservations or complete assembly costs; no automatic alternate is accepted.

## Current, startup and loss costs

The resistor sets nominal ICL = 2000/3300 = **0.606 A**. Combining TI's conditional ±15% with resistor ±1% gives approximately **0.510–0.704 A**. Accuracy requires VS−OUT ≥2.5 V and the stated setting range. Including ±100 ppm/K resistor drift from 25°C widens that estimate to about 0.507–0.708 A at 85°C or 0.504–0.713 A at 150°C. This is a provisional engineering current budget, not an OEM current allowance or unconditional draw ceiling. CL dissipation at its nominal 0.8 V is about 0.194 mW; the resistor is 100 mW through 70°C, derating to zero at 155°C.

TPS1H200 replaces the old CT-controlled startup with its internal slew and current limiting. Continued current limit yields **35–45 ms on / 0.8–1.2 s off** (40 ms/1 s typical). Those timing values are specified by design, not production tested; thermal interruption can affect the observed attempt. A load that cannot finish startup in an attempt can repeatedly reset. The unloaded illustrative minimum charge budget, 0.510 A ×35 ms≈17.9 mC, does not include buck or module demand. The retained switch-output plus buck-input nominal capacitance is about10.2 µF, but converter startup, its44 µF output, carrier rail/module capacitors, DC bias, RF load and source impedance must be included in the measured startup. AP63205's nominal4 ms soft start does not by itself close this gate. Local VS must remain above the switch's maximum4 V restart threshold during cold start.

At364 mA, a deliberately mixed-condition comparison using PPTC room-temperature R1max, CJ3407's25°C0.087 Ω and switch hot limits changes fuse+FET+switch drop from about237 mV to323 mV: **about86 mV additional path loss**. It is not a guaranteed hot budget. TPS1H200's400 mΩ maximum is stated at150°C; its5 mA active-supply maximum uses VS13.5 V, IN5 V and0.5 A load. Original TPS22810's cited85 µA belongs to its specified low-voltage conditions. Added consumption and D14/D15, buck/dropout/inductor, D11 and the actual C3/C6 module path must be measured. Both modules' loaded nominal5 V cold start/RF/brownout behavior remains open. No reduced input specification is used to force a pass.

## Whole-chain protection bounds

The nominal5/7.5/9/13.6 V examples are retained as intended cases; OEM tolerances, currents and transients are unknown. SMF16A's26 V maximum clamp is specified at7.7 A,10/1000 µs and25°C. Actual temperature, pulse shape, wiring overshoot, energy and repetition remain unqualified. TPS1H200's40 V rating addresses the former switch-rating mismatch in that bounded positive-pulse comparison; it does not confer40 V on the carrier.

Retained CJ3407 requires |VDS|<30 V and |VGS|<20 V with margin; AP63205 must stay within its32 V operating maximum, not target its35 V absolute rating. Both33 V PPTCs need their own differential-voltage bound; the downstream clamp does not bound raw connector voltage or voltage across a tripped fuse. High-node50 V capacitors do not resolve those weaker parts. A charged26 V protected node followed by−13.6 V at the PMOS drain creates39.6 V differential, beyond the retained PMOS. Reverse-step behavior therefore remains a qualification gate, not a claimed OEM event.

Switch CL does not limit upstream TVS current. PPTC maximum0.20 s trip at8 A does not establish that a200 W10/1000 µs SMF survives sustained overvoltage until trip. Bound source impedance/current, fault duration/energy and recovery. Littelfuse0.75 A hold/1.5 A trip are at20°C; reference hold values0.47 A at70°C and0.36 A at85°C are not an enclosed-board source allowance. D14/D15's current/thermal limits remain independent;0.606 A CL is not a new continuous diode/system rating.

## TI package rule and assembly gates

The custom U9/U10 footprint follows current **TI Rev E May2026, DGN0008K-C01 pp28–29**: lead pads1.4 ×0.45 mm, row spacing4.4 mm and pitch0.65 mm. Thus adjacent copper-pad gap is0.20 mm. Two explicit rules apply that minimum only to pairs of pads within the same named U9 or U10 footprint. Global0.20 mm and Power0.25 mm clearance, routes, vias and other footprints retain their original rules. Short0.20 mm track necks escape the fine-pitch pads under those unchanged routing rules.

This is the manufacturer's intended intrinsic package geometry and an engineering exception to the Power pad rule. JLC publishes a0.15 mm minimum different-net SMD pad gap at1 oz, so the0.20 mm geometry is fabricable. **No universal insulation/IPC/environmental compliance is claimed.** Contamination, coating, operating environment and assembler acceptance remain open.

EP copper is2 ×3 mm, mask-defined exposed area1.57 ×1.89 mm, and one matching full paste aperture follows TI's0.125 mm stencil example. Optional under-paste vias are omitted; external0.8/0.4 mm GND vias outside the exposed/paste pad connect to the ground plane. TI p28 explicitly makes vias optional. Final ≥85% solder coverage, stencil/process approval and actual thermal performance still require qualification. The JEDEC47.4°C/W is not a prediction for this layout. New STEP files are explicitly approximate maximum package envelopes derived from TI/Littelfuse drawings, not authenticated vendor CAD.

## Verification, cost and release state

Native KiCad9.0.9 all-severity ERC and all-track/parity DRC report0 violations,0 unconnected items and0 parity differences. The current [source proof](validation/rated-switch-proof.json) verifies100 schematic/PCB items,233 pin nets,205 unchanged nonreplacement pin nets,83 matching fitted BOM/CPL references, original core functions/geometry/firmware and0.0 mm² filled antenna overlap on all four layers. The sourcing correction refreshes the native BOM, netlist and schematic PDF. New native CPL conversion is byte-identical to the retained CPL; every Gerber/drill/job export changes only generation dates/checksums, so the existing factory ZIP is retained byte-for-byte. Unchanged copper/render/drill-map images preserve their reviewed geometry; actual updated schematic pixels are inspected.

Public selected-part estimates for two switches, two fuses and two TVSs are approximately **+$0.91 per board at the compared small tiers /+$0.69 at the compared100-piece tiers** versus the former exact selection. That estimate excludes added CL/retry passives, gate-zener sourcing changes, removed capacitor credits, assembly/Extended fees, shipping/tax and procurement charges. It is not a finished assembled-board quote. This design adds 3 fitted parts net (80→83); switches, fuses and MCC gate zeners are Extended catalog parts, while C22978 and corrected C149504 are Basic. Complete exact-part quotes are $134.64 for five carriers and $168.91 for ten, versus $130.39/$160.37 for the stock-corrected 80-ref baseline, before shipping, tax and XIAO modules. That is about $0.85 per carrier including assembly. Recheck stock and all process fees before any approved order. Frozen8f95555 and46173b6 quote inputs remain unchanged. No order, publication or physical test is performed in this candidate.

Primary references: [TI TPS1H200 Rev E](https://www.ti.com/lit/ds/symlink/tps1h200a-q1.pdf), [Littelfuse1812L](https://www.littelfuse.com/assetdocs/resettable-ptcs-1812l-datasheet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), [exact SUNMATE sheet](https://jlcpcb.com/api/file/downloadByFileSystemAccessId/8757789523080564736), [Royal Ohm resistor sheet](https://www.royalohm.com/assets/pdf/products/smd/1.pdf), [JLC C22978](https://jlcpcb.com/partdetail/23705-0603WAF3301T5E/C22978), [JLC fabrication limits](https://jlcpcb.com/capabilities/pcb-capabilities), [AP63205](https://www.diodes.com/datasheet/download/AP63200-AP63201-AP63203-AP63205.pdf), [KiCad9 custom rules](https://docs.kicad.org/9.0/en/pcbnew/pcbnew.html#custom_design_rules).
