Dr-Crow/esphome-ge-laundry-uart/case/rev3c/review/recovered-enclosure-review.md

# Recovered GE enclosure review and bounded prototype plan

Reviewed 5 October 2026 against public Rev3C baseline commit `11826a7f6ba1ed19131ddba46e4d62b06196a8c6`. This is a source/export review; enclosure generation, slicing and physical tests were not performed. Recovered sources and exports remain unchanged.

**Recommendation:** use `GE-printed-case/enclosure.py` as the editable starting point for the existing tapered, common-base prototype, with a C3-specific lid first and retained C6-specific alternatives. Keep the older cassette package as historical styling/mechanism reference. Neither package is a qualified enclosure for the selected dual-input Rev3C carrier. Both are **build123d Python**, rather than CadQuery. The shared board datum aligns; the installed-height/contact calibration is the principal mechanical blocker.

## Source identity and usability

Paths below identify the named recovered archives and files within them. Complete per-file hashes, export measurements and manifest-input findings are in `inspection-receipt.json`.

| Actual file | SHA-256 | Status |
|---|---|---|
| `GE-printed-case/enclosure.py` | `a016dbfcab8d10214f3d6880a9fdc76e442041a8baee49cf65e8edc957415607` | Later editable all-printed prototype: common base, four module/antenna lid variants, three lightpipes, cropped button/snap coupons. Selected starting point. |
| `GE-tapered-enclosure-review/enclosure.py` | `89452f9390ed309497f51db7d4091a4d4d46f0cc1bc54093d59232a8ac869aa2` | Earlier editable screw/spring/cassette prototype. Superseded by the printed package's README; 23 enclosure/mechanism pieces before optional RF/magnets/electronics. |
| Both `interface_baseline.py` copies | `c5ca15aec72c429d78d5d4894f15078fb322e3282d7e5468ff64fbd1ca431ceb` | Identical attributed C3-specific interface reference. Active constants/helpers are reused by new enclosure sources; baseline standalone case functions are historical. |
| Both `component_envelopes.py` copies | `146a54c71920b71695831971c02fd93bb14e48ca4e6f9e1468e78b22f915c7ab` | Identical simplified electronics proxies. Not printable parts or full selected-carrier/component geometry. |
| `GE-printed-case/README.md` | `e45284c23263ba64723b776846c9e1d3f213160b9183f2d8f5f6fee15ceaaae7` | Defines five printed pieces in a chosen assembly and explicitly keeps fit/force/optical/RF gates open. |
| `GE-printed-case/PRINT-TEST-GUIDE.md` | `aa4446060f60f9b8ad4076ae255919c6d167e8e031e17cf55080a362e5982053` | Useful coupon/strain/tolerance planning. Numerical examples are screening calculations, not material/process/life approval. |
| `GE-printed-case/VALIDATION.md` | `622359b8c7c28bcd20ba6bda8da64d3cadfad02f2a0f9ede4b1c13fcb13a4c8c` | Historical nominal counts for its frozen source; independent full collision/elasticity proof scripts are absent from this package. |
| `GE-printed-case/SOURCING.md` | `638eac5ba92dd7763c3bae3d22009300b07fa595fe711daa49c67fac0237568e` | Documented module translations, conditional switch data and bulkhead dimensions. Actual module revision/part identities remain gates. |
| Both `requirements.txt` copies | `0cc484bca9656a92d55d8bad637a832364d58419b67be3250143e70952102075` | Pins build123d 0.11.1/trimesh 5.1.0. Fresh export checks used build123d 0.10.0; trimesh was unavailable. Pinned source regeneration remains a reproducibility gate. |

All recovered Python files passed syntax parsing. Generation was not executed. The delivered STEP files are editable exchange solids; STL files are print meshes. Neither retains the Python parameter/history structure. Independently imported **15 printed-package and 18 older-package STEP/STL pairs** all have valid STEP geometry, positive mesh volumes and exactly two incident triangles per mesh edge. Maximum STEP/STL volume difference is **0.094%**. The two optional printed inlays are multiple glyph solids by design. These checks establish export integrity, without verifying moving mechanisms or physical fit.

Fresh check method: STEP import/validity/solid count/volume/bounds used installed **build123d 0.10.0 with cadquery-ocp 7.8.1.1.post1**. A separate standard-library binary STL parser checked exact `84 + 50 × facet_count` file size, calculated signed volume from triangle tetrahedra and counted undirected edges using exact float vertex tuples. Closed-edge incidence is not a general self-intersection/normal-consistency proof. `provenance-counts.json` contains the compact method/version/count receipt; `inspection-receipt.json` retains each export's results and all file hashes.

The printed archive has no `exports/summary.json`, although `validate_exports.py` requires it, and contains no render PNGs. Its five manifests reference 10–28 absent inputs each, including electronics/cutaway meshes and external supplier references; regeneration/preparation is needed before those render recipes are usable. The older archive includes ten actual renders and 18 delivered export pairs, while its historical validation record describes 51 generated pairs. The old exterior/C6 mechanism/indicator-guide PNGs were inspected as pixels: they show the earlier fixed exterior button locations, transfer paddles, return springs and lower lightpipe cradles, which do not represent the later integral-button lid. Do not use those images to approve the current printed mechanisms. Supplier assets should retain their recorded licensing/redistribution constraints.

## Finding matrix

| Feature | Source/current comparison | Prototype gate |
|---|---|---|
| Shared carrier and both inputs | Current PCB independently confirms 99 × 40 mm outline, H1 `(4.5,33)`, H2 `(94,35)`, J5 `(95.51,5.2975)` and J6 `(80.27,20.5375)` with opposite row orientation. These match the case baseline. PIN1/VDC and PIN3/ALT_PWR arrive through the **same J1 8P8C**, with automatic priority inside the unchanged carrier. | Preserve both branches and priority; no second power opening or circuit change is needed. Treat 8P8C as appliance bus, not Ethernet. |
| Selected rated-switch components | Current U9/U10 are at `(65,8)`/`(65,22.5)` with 1.1 mm maximum package-envelope height; F1/F2 at `(45.5,21.5)`/`(45.5,7)` use 1.55 mm maximum envelopes; D20 is `(47,15)`. The old case proxies omit these and most carrier components. | Update/check full current component envelopes before any whole-case collision pass. Historical proxy counts cannot qualify current 40 V-switch geometry or thermal behavior. No obvious outer-outline change is required. |
| Module/socket Z | Case carrier top is Z5.25. It derives module bottom maximum Z16.90 from **8.65 socket + 3.0 spacer**, while current visual model uses **8.5 + 2.5 = 11.0 above carrier top**, i.e. Z16.25 in the case datum. Both are assumptions. Male pins/spacers/mating depth are not measured. | Measure actual seated carrier/socket/module assembly; account for carrier support, seating depth, spacer, PCB/solder/warp, switch height, lid closure, print shrink and reach/stop errors. |
| C3/C6 BOOT and RESET | Printed source uses C3 `(79,8.4725)`/`(79,17.3625)` and C6 `(97.3483,19.4927)`/`(97.3483,6.3355)`, consistent with current module-datum review. Lids are module-specific. A C3 contact is ~0.19 mm from C6 U.FL; the C3 RESET contact falls within C6 ceramic body projection. | Verify installed revision, actuator target and independent reach/stop for all four buttons. Never fit/press a C3 lid on C6. Externally marked variants do not provide a modeled mechanical interlock. |
| Button travel and force | Fixed switch tops Z20.00 C3/Z19.03 C6; released gap 0.25; stop motion 0.40/0.36. Under current 11.0 mm visual stack, either nominal released gap becomes **0.90 mm**, leaving 0.50/0.54 gap at stop. Conversely C6 conditional height tolerance alone gives 0.01–0.21 mm depression around 0.11 nominal travel. | Neither assumption proves actuation or safe overtravel. Verify fitted switch identity, electrical make, allowed force/overtravel and no released preload. Current case reaches require calibration before contact with modules. Stops cannot use nominal travel as an overtravel allowance. |
| LED labels and paths | WIFI: D4 green `(84,26)` to roof `(70,32)`; AUX: D5 red `(84,30)` to `(80.25,32)`; BUS: D6 yellow `(88,26)` to `(90.5,32)`. Matches current firmware: Wi-Fi connected; manually controlled red/off at boot; bus-connected, rather than per-packet blink. Guides begin Z6.75 and end Z30.48. Latest source uses short roof collars and a 0.12 mm diametral press-fit band. | Measure actual LED body/solder height and optical gap. Test lightpipe insertion/retention, brightness and crosstalk; old angled-cradle images are stale. AUX must not imply fault/power status. |
| USB and J1 openings | Latest USB cut is 14.8 × 9 rounded aperture at Y12.9175/Z20.7; it spans nominal Y5.5175–20.3175/Z16.2–25.2 before corner rounding. C3/C6 USB XY is similar, but module seating Z and plug bodies differ. J1 cut Y7.74–25.925/Z4.75–18.2 accommodates the documented updated body nominally. | Check both real USB shells and selected plugs/strain relief, full insertion, finger access and J1 latch/service access. Source uses old J1 envelope; current drawing model has dimensioned body but illustrative inner mating detail and unresolved post pitch. Appliance cable disconnected for powered USB recovery. |
| Antennas and remote bulkhead | C3 internal: nominal 40 × 20 FPC at X22–62/Y4–24 with conservative termination slab Z26.4–28.2, rails/catch/keepers. C6 internal omits FPC; its corrected U.FL/ceramic coordinates agree with current review, but source ceramic proxy is nominal rather than maximum. External lid has D-flat Ø6.5/6.0 datum, 1.5 mm land, nut recess and sleeve keeper at X56/Z15.5. | Actual FPC 40.3 × 20.2 tolerance, solder/feed point, route length, bends, keeper retention and lid-opening slack need checks. Entire 102±3 mm RG178 route is unqualified; use documented ≥1.83 collision diameter and ≥11 mm centerline bend screen. Test anti-rotation/panel crushing/whip leverage and independent cable restraint. Remote stand is a sourced RF option with schematic route, not a modeled qualified support. C6 GPIO3/GPIO14 selection must match fitted antenna. |
| Printed return leaves and snaps | Two 0.8 × 1.2 leaf primitives per button; effective span ~13.22–14.30, not full primitive length. Shaft/bore has 0.17 mm radial clearance. Both leaves originate on the same side. Two horizontal latch leaves have ramp, shoulder, seam-level release and inward stop; modeled deflection is a rigid diagnostic envelope, not elastic simulation. | Slice and print supplied coupons before electronics. Check bridges, guide alignment/debris, off-centre load, return, root cracking, permanent set, repeated release and retention. Guide's illustrative 0.30–0.40 per-side moving allowance exceeds actual nominal shaft clearance. `FLEX_L`/`STROKE` constants are unused; geometry and `TRAVEL` govern. |
| Supports, closure and magnets | Base supplies original mount posts, socket/J1 solder-tail relief and external closure datum lands. Latest snaps replace older screws/nuts. Magnet variant adds underside pockets at `(33,34)`/`(60,34)` with no capture/retention qualification. Baseline still describes J2 and fully assembled preheadered module delivery. | Check tail lengths/floor skins, H1/H2 seating and lid restraint, repeatable closed height, module/header retention under tug/vibration. Current J2/D19 are absent; module is supplied separately with 14 fitted pins required. Start without optional magnets, then test capture/painted-steel slip separately if needed. |

Current PCB SHA-256: `4fba3feea4161f7e6bdfbd7f20ac677a485948fac540d7bda1c246a451c4bab9`. Exact current document/source hashes and independent datum values are in `current-datum-comparison.json`. The frozen rated-switch proof's pre-model PCB hash differs from this current PCB; its electrical claims are not an enclosure fit proof.

## Bounded prototype sequence

1. **Freeze this candidate and measurement record.** Preserve the selected dual-input/automatic-priority carrier and four firmware profiles. Record actual C3 and C6 revision/SKU, header pins/spacer/mating depth, carrier top, both actuator tops, USB shell/plug and RF connector/cable envelopes. Retain separate C6 geometry even while C3 is first.
2. **Coupon gate without electronics.** Use delivered C3/C6 button coupons and snap pair in one defined unfilled PETG profile, plus a separate lightpipe/press-fit test. Inspect actual slice/orientation/bridges and measure clearance, return, permanent set, release and closure-height repeatability. The crop limits are not a full paired-button or full-case trial. Record the process and measured tolerances before changing only contact-reach/stop/fit parameters in a working copy.
3. **Calibrated C3 assembly gate.** With measured switch/stack bounds, establish released gap >0, worst-case electrical make before stop and stop within verified permitted travel/force. Fit actual fully seated assembly unpowered. Test each button and BOOT-held/RESET-pressed recovery, USB/J1 full access, optics, module restraint and lid-removal cable slack. No switch serves as a module retainer.
4. **Preserved C6 gate.** Repeat the same measurements/calibration on its own lid and actual conditional switch identity. Check U.FL/ceramic maximum envelope and final RF selection. C3 success is not evidence of C6 actuation or antenna clearance.
5. **Whole-case installation gate.** Independently check current component maximum envelopes, solder tails, cable/strain relief, repeated closure/actuation and loaded thermal behavior. Test optical/RF performance, vibration/tug and intended appliance-adjacent steel/orientation. Pick a service-cycle target before fatigue testing. Optional external bulkhead, remote lead and magnets each need their applicable retention/RF checks.

This closes source recovery and identifies a prototype path. It does not close printer fit, switch safety, lifetime, RF, thermal, ingress/flame or appliance qualification. No redesign, safety-circuit edit or manufacturing commitment is required to begin the measurement/coupon stage.
