Dr-Crow/esphome-ge-laundry-uart/docs/revision-comparison/preorder-2026-10-05/rev3-power-refinement/PMOS-Transient-Example-Correction.md

# PMOS transient example correction

The retained CJ3407 has a −30 V drain–source rating. In the exact selected Rev3A/B/C source, D18 cathode1 is at PIN1_PROTECTED/Q3.source2 and its anode2 is GND; the second SMF16A is A D19 or B/C D20, cathode1 at PIN3_PROTECTED/Q4.source2 and anode2 at GND. D13 is absent. Neither fused drain3 node has a directly connected TVS. An intact unidirectional TVS forward-conducts if its protected source node goes negative, but that connection does not impose a documented negative voltage bound on the fused drain. The exact SUNMATE C399290 sheet publishes no maximum forward voltage/current condition, so a numerical negative clamp cannot be borrowed from another maker. If a protected source were momentarily at +26 V while its fused drain actually reached −13.6 V, VDS would be −39.6 V; this is an unbounded-node, unmeasured transient counterexample, not a demonstrated normal-source condition or a proven failure. Even the +26 V reference belongs to the specified7.7 A,10/1000 µs,25°C positive-pulse test. Actual drain/source/gate waveforms, source impedance and clamp/current survival must establish the differential before selecting a higher-voltage PMOS.

Source: exact77f4c8893db6c018640e25c55a3af624a3eb06b3 numbered netlists, recorded in pmos-tvs-placement-correction.json; SUNMATE C399290 primary-authored PDF https://jlcpcb.com/api/file/downloadByFileSystemAccessId/8757789523080564736, SHA2567b825d053f2797dcfd6efd8a268f79365b147bc57f7dc42c6da31fedab743e2b, pp1–3; JSCJ CJ3407 Rev2.3 https://www.jscj-elec.com/pdf/f3fb09e55afae446e8a8f8a35ab44e62.pdf, pp1–2.
