Dr-Crow/esphome-ge-laundry-uart/docs/revision-comparison/preorder-2026-10-05/power/GE-All-Revision-Power-Margin-Review.md

# GE all-revision analytical power and USB review

5 October 2026 UTC. Read-only review of the integrating source captured at `ba4dc5a5779bb48e63756db0a8a1791df6bd427c`, with electrical baseline `11826a7f6ba1ed19131ddba46e4d62b06196a8c6`. The integrating checkout advanced from requested `bf581ac` during the review; the captured schematic, PCB and netlist hashes identify the actual inputs. No schematic, board, BOM, firmware, purchasing, publication or physical test was changed by this analysis.

**Result:** useful analytical bounds are now available for all seven revisions. They do not close an appliance-specific source or physical qualification. Rev3C's preserved C3/C6 choices each have a different low-input and thermal budget. Rev2.0/2.1/2.2 have a genuine **200 mA 3V3 regulator capability mismatch** against the WROOM module's ≥500 mA supply requirement; their old protection and thermal constraints also prevent calling them qualified fallback boards. No justified single component substitution closes every gate.

## Per-revision decision matrix

Published RF rows below are 3.3 V / 25 °C operating-point peak figures, **not guaranteed assembled-board maxima**. A 500 mA chip-load stress case is separately identified and is not claimed to be normal appliance demand. Current refers to the indicated rail; converter input and output currents must not be equated at different voltages.

| Revision | Actual main path / output supply | RF + carrier proxy | Analytical issue that can be acted on now | What remains unknown |
|---|---|---|---|---|
| **Rev3C, C3** | Both GE inputs → rated switch/OR → AP63205 → D11 → J6.7 VBUS → module fuse/MSK4005 → TLV75733; J6.5 returns 3V3 | Chip 335 mA + 20.626 mA on 3V3; about 356.66 mA carrier buck output including 5 V loads, before module auxiliary draw | Preserve both inputs/priority/buck/C3-C6; annotate exact module series limits and current-primary diode thermal ceiling. Nominal 5 V headroom is conditional; no guaranteed low-input pass or failure is established | Source tolerance/current/impedance, cold drops, C3 fuse identity/resistance/hold curve, RF/startup maximum, actual module temperature |
| **Rev3C, C6** | Same carrier → J6.7 VBUS → LMBR4010BST5G → SGM6029C buck/0.47 µH → J6.5 3V3 | Chip 354 mA + 20.626 mA on 3V3; VBUS current is lower when buck regulates | Use SGM6029C 1 A variant and diode limits; a buck model, not an RT9080 LDO model. Series diode thermal budget is material | Exact lot, module inductor DCR, diode hot/cold drop, efficiency/dynamics, RF-switch/charger overhead, actual thermal rise |
| **Rev3B** | Same two GE branches and AP63205/D11 → soldered XIAO C3 v1.3 | Same C3 proxy as above | Same C3 headroom/thermal limits; module USB is directly tied to carrier +5V; recovery J2/D19 adds another allowed source only when isolated | Same electrical gaps, plus exact assembled module and its internal fuse |
| **Rev3A** | Same two GE branches/AP63205/D11 → AP2112K-3.3 → WROOM-02-N4; independent USB/F3/D10 OR | WROOM 345 mA + 20.626 mA on 3V3; about 366.66 mA buck output | AP2112's 600 mA capability meets the bare current-capacity screen; its LDO thermal budget remains material. Keep EN RC/recovery and all original source functions | AP2112 dropout at actual load, enclosed effective thermal resistance, source/USB handoffs and EN timing |
| **Rev2.2** | Manual JP2 selects J1.1/F2 or J1.3/F1 → Q1/Q2 → L7805 → TECH PUBLIC TPAP2205-33Y → WROOM | WROOM 345 mA plus revision-specific carrier loads | 200 mA rated 3V3 capability cannot meet ≥500 mA module supply provision. Original ±20 V gates/25 V cap do not coordinate with 32.4 V TVS reference | Correct new regulator selection, rail and reset behavior, heat, input envelope; source shunt data conflicts remain |
| **Rev2.1** | Same selected linear architecture; actual C5205181 is Diodes AP2205-33Y-13 | Same WROOM row; not a 200 mA-certified load | Same current-capacity, gate/cap/thermal issues. Preserve fitted supervisor and genuine history; do not copy Rev2.2 omissions | Same, plus installed resistor values/history and load qualification after purchasing correction |
| **Rev2.0** | Same selected linear architecture and Diodes AP2205-33Y-13 | Same WROOM row | Same rated 200 mA mismatch; fitted supervisor and D8 identity ambiguity are independent gates | Same, plus exact D8 behavior/protection identity |
| **Rev1.0** | J2.1/F1 → Q1/Q2 → J1.3 → external buck → J1.1 +5V → unidentified classic ESP32 devboard U3.19; U3.1 exports 3V3 | Whole-module draw unbounded; no exact devboard/regulator identity established | Resolve 0.2/0.3 A fuse and 1210/1812 footprint conflict, external buck specification and actual 38-pin module. Preserve population alternatives | Exact physical module, external buck current/voltage/dropout/thermal limits, fuse temperature curve, USB isolation and appliance envelope |

Detailed module primary evidence is in [GE-XIAO-Module-Power-Evidence.md](module-power/GE-XIAO-Module-Power-Evidence.md). Detailed legacy evidence is in [GE-Legacy-Power-Limits-Review.md](legacy-power/GE-Legacy-Power-Limits-Review.md). The existing [module sourcing review](../module-sourcing/GE-Exact-Module-Sourcing-Review.md) and [legacy intent review](../legacy-intent/GE-Legacy-Resistor-Intent-Review.md) retain procurement and genuine-history context; their conclusions are not silently superseded.

## Numbered power and USB paths

The read-only [numbered-net audit](numbered-power-net-audit.json) independently compares native netlist pin groups to actual PCB pad groups in all seven revisions: **zero physical net-membership differences**. Four Rev3B NC names encode a slash differently (`/` versus `{slash}`); their single-pin membership is identical. This checks connectivity, not physical conductance, source capability or an energized board.

For current Rev3A/B/C:

- **PIN1:** J1.1 → F2.1/2 → Q3 drain3/source 2 → U9 VS8/OUT7 → D14 anode2/cathode1 → V_INPUT → U8 VIN3/EN2. **PIN3:** J1.3 → F1.1/2 → Q4 drain3/source 2 → U10 VS8/OUT7 → D15 anode2/cathode1 → same V_INPUT.
- U8 SW5 → L1.1/2 → BUCK_5V; U8 FB1 senses that output; BST6/C15 and GND4 retain their original functions. D11 anode2 at BUCK_5V and cathode1 at +5V isolates the buck output.
- Q3/Q4 gate1 follows its gate-bias node through 51 Ω. Zener D16/D17 cathode1 is at PMOS source 2; anode2 is at the 5.1 kΩ-to-GND bias node. U9 IN1 follows its own protected source. U10 IN1 is PIN3_EN, R36 pulls it from PIN3_PROTECTED and Q5 collector3 sinks it. Q5 base1 receives PIN1_PROTECTED through R35 with R37 to GND; emitter2 is GND.
- Rev3C J6.7=+5V/VBUS, J6.6=GND and J6.5=module 3V3 **output**. Rev3B U2.14=VBUS and U2.12=3V3. Do not externally drive the 3V3 output or battery pads.
- Rev3A USB J4 VBUS → F3 → D10 anode2/cathode1 → +5V → U6 VIN1/EN3 → U6 VOUT5 → WROOM U2.1. Its USB data/ESD paths do not imply power-source qualification. F3 is exact Littelfuse 1206L050YR: 6 V maximum differential, 0.5 A hold at 20 °C, R1max 0.7 Ω; reference hold is 0.31 A at 70 °C / 0.25 A at 85 °C. At the 366.66 mA proxy its room-R1max drop is 257 mV and dissipation94 mW, before D10. Hot USB continuous-current margin is open.

The preserved Q5 selector senses **PIN1 presence**, not useful power. If PIN1 is weak, faulting or starting in repeated switch retry, it can still inhibit healthy PIN3. That is retained behavior, not new automatic fault fallback.

| PIN1 / PIN3 / powered USB | Rev3C/Rev3B consequence |
|---|---|
| 0 / 0 / 0 | Unpowered except possible external bus/backfeed; that state needs qualification |
| 0 / 0 / 1 | Module USB powers VBUS/+5V and module 3V3; carrier D11 is reverse-biased toward buck |
| 0 / 1 / 0 | PIN3 branch enabled through R36 |
| 1 / 0 / 0 | PIN1 branch supplies common buck |
| 1 / 1 / 0 | PIN1 presence inhibits PIN3; weak PIN1 inhibition remains |
| 0 / 1 / 1; 1 / 0 / 1; 1 / 1 / 1 | Raw module USB VBUS is tied to carrier +5V, so simultaneous sources are outside the documented operating contract |

For Rev3C physically remove the appliance cable before powered USB and remove USB before appliance use. Rev3B also requires J2 recovery power to be the only connected supply. D11 and internal module diodes do not isolate a USB host from raw carrier VBUS. Rev3A has its original two-diode OR, so all eight source combinations remain test cases; a diode limits normal direction but leakage, powered-off data pins and abnormal faults still require measurement. Rev2 service J3.2 is directly 3V3; external injection can reverse-bias its LDO. Rev1 USB behavior depends on the unidentified devboard.

## Currents and nominal / cold / hot assumptions

For Rev3A/B/C a transparent **all-three-LEDs-on example** assumes LED forward drops1.8/2.0/2.0 V, nominal 3.3 V/5 V, six3V3 10 kΩ pull-ups fully sunk, both5V 10 kΩ pull-ups fully sunk and220 kΩ biased. It gives20.626 mA on 3V3 plus 1.033 mA on 5 V. This is a useful carrier addition, not measured average traffic. GPIO voltage drop, LED variation, module auxiliary draw, buffer dynamic/midrail current, bus-clamp current and startup remain extra terms. Valid-logic buffer ICC maximum is10 µA through 85 °C /40 µA through 125 °C; midrail inputs can add500 µA /5 mA per specified condition. Do not apply the valid-logic figure through a brownout.

At3.6 V/5.5 V and−1% resistors, setting LED VF=0 gives resistor-only ceilings51.81 mA on 3V3 and1.176 mA on 5 V. These deliberately loose ceilings bound those passive paths only; they do not certify LED/GPIO/fault operation. A 220 Ω resistor's maximum3.6 V dissipation is59.5 mW, below the part's103 mW reference derated power at 85 °C. Actual resistor temperatures and signal fault voltages remain separate.

| Current quantity | Nominal25 °C evidence | Cold / hot bound |
|---|---|---|
| C3 chip RF row / WROOM module RF row / C6 chip RF row | 335 /345 /354 mA operating-point peaks | No guaranteed all-process/temperature/startup maximum published in these rows |
| Rev3C-C3 / Rev3B carrier buck output proxy | 356.66 mA before module auxiliary current | Same fixed-load sensitivity only; not a cold/hot current bound |
| Rev3A carrier buck output proxy | 366.66 mA | Same qualification limit |
| 500 mA chip + carrier stress | 521.66 mA in a linear chain; C6 differs by conversion | Stress scenario only; exceeds C3 nominal 500 mA series-module rating before unknown auxiliaries |
| TPS CL with 3.3 kΩ | 606 mA nominal; conditional510–704 mA with±15% andR±1% | WithR±100 ppm/K:507–708 mA at 85 °C. Accuracy requires VS−OUT≥2.5 V; not an unconditional draw ceiling |
| 1812L075/33 reference hold | 0.75 A at 20 °C | 1.10 A at−40 °C;0.47 A at 70 °C;0.36 A at 85 °C, stated reference mounting/still-air behavior |

Both-input source bias is additional and not converter load: at 13.6 V, R35 draws about 1.29 mA at a0.7 V base; inhibited R36 draws about 1.35 mA at 0.1 V collector; switch supply can be5 mA under TI's13.5 V/0.5 A test; DELAY100 kΩ currents and gate bias also draw upstream. The input fuse/PMOS carries upstream bias; switch CL applies to OUT channel. Those test conditions are not guaranteed complete hot/cold board budgets.

## Low-input voltage and regulator heat

[conditional-input-sweep.csv](conditional-input-sweep.csv) is elementary arithmetic with **mixed datasheet conditions**: PPTC20 °C R1max0.4 Ω + CJ3407 25 °C RDSmax0.087 Ω + TPS hot RDSmax0.4 Ω, input diode0.55 V, output diode0.34 V, buck high-side0.125 Ω **typical** plus inductor20 °C DCRmax0.05016 Ω. The AP63205 has no published maximum low-dropout resistance covering this chain; diode maximum rows are25 °C, and the PPTC resistance is not a hot bound. Therefore the resulting rail is neither a guaranteed minimum nor a measured voltage.

| Illustrative raw 5 V case | Buck VIN / carrier+5V | Module/regulator interpretation |
|---|---|---|
| C3 chip+carrier356.66 mA | 4.134 /3.731 V, before upstream bias/copper | C3 moderate module sensitivity VF0.35 V/Rfuse0.20 Ω/Rdrop0.30 Ω gives about 3.203 V rail at 355.626 mA; above3.0 V minimum but below3.3 V target |
| WROOM+carrier366.66 mA | 4.125 /3.721 V | AP2112 has200 mV max at 300 mA and400 mV at 600 mA; no separately guaranteed366 mA interpolation. Its actual loaded rail must be established |
| 500 mA chip+carrier521.66 mA stress | 3.987 /3.556 V | C3 same sensitivity model gives about 2.946 V, identifying a stress-demand risk, not normal-load failure |

For C6, [conditional-c6-input-sweep.csv](conditional-c6-input-sweep.csv) uses the correct near100%-duty input≈output-current proxy, **not a regulated3.3 V power formula in dropout**. With374.626 mA total3V3, the same carrier path gives3.711 V VBUS at raw 5 V; module diode0.30/0.50 V and SGM0.31 Ω screen give about 3.295/3.095 V before module inductor/copper loss. Exact TDK TFM160808ALC-R47MTAA's20 °C DCR maximum62 mΩ adds23.2 mV, giving3.272/3.072 V before PCB/dynamics in this mixed-condition model. The3.3 V target and3.0 V minimum remain separate, and actual cold/hot dropout/RF dynamics are unqualified. Higher inputs use a separately labeled assumed80/90% module efficiency, not a guaranteed efficiency floor.

An **actual3.21 V before an LDO** cannot prove failure merely by being below3.3 V. It does show the regulator cannot maintain a regulated3.3 V target. Whether the downstream rail remains above3.0 V depends on the actual loaded dropout, other loss, ripple and transient response. Scaling TI's1 A maximum dropout to lower current is a sensitivity model, never an independent guaranteed corner.

At raw 7.5/9/13.6 V, assuming85% AP63205 efficiency and a regulated5 V output, C3 branch current is roughly314/255/163 mA and WROOM branch324/262/167 mA before bias. The extra switch resistance changes input loss/current, not automatically the regulated3V3 by the same voltage. At C3 proxy the buck power-loss sensitivity over 80–95% efficiency is0.446–0.094 W; multiplying by the89 °C/W reference gives40–8 °C rise if all loss were IC heat. That is not an actual board thermal bound. Inductor typical3.4 A temperature-rise /6.7 A saturation ratings are not board current allowances; DC copper loss at 356.66 mA and50.16 mΩ is6.38 mW.

For Rev3A, a4.7 V AP2112 input with 365.626 mA 3V3 load gives0.512 W including80 µA ground-current illustration, and94.3 °C rise using184 °C/W reference. At85 °C ambient that reference crosses150 °C; duty, copper and real thermal resistance determine the real outcome. For C3, the companion report shows TLV's231.1 °C/W JEDEC versus100.8 °C/W EVM references. Maximum diode/fuse drop reduces LDO heating while worsening voltage headroom; it cannot be used as the sole thermal worst case. C6 series-diode250 mW/minimum-pad limit and2.5 mW/°C derating matter independently of the buck's1 A rating.

U4 runs from carrier+5V. Its guaranteed threshold rows cover3.0–3.6 V and4.5–5.5 V, leaving no table row for the3.7 V rail in the example. Do not keep using nominal 5 V VIH=3.5 V/VIL=1.5 V through that sag, or interpolate undocumented thresholds. U5 uses module3V3; its2.0/0.8 V thresholds require that rail in3.0–3.6 V. Actual GE drivers/bias, edge rate and loaded high/low/noise margin are qualification inputs.

## Protection, derating and fault energy

40 V TPS switches do **not** rate the carrier40 V. The weakest condition can be PMOS differential, PPTC differential, buck operating voltage, diode heat, capacitor or resistor temperature, rather than a switch's own VS rating.

- **Gate network:** at 26 V source/nominal 12 V zener/−1%5.1 kΩ, resistor power38.82 mW, zener≈33.27 mW. The exactMCC voltage11.4–12.7 V is specified at 5 mA/25 °C; actual≈2.8 mA is below that test. Its typical temperature coefficient and impedance do not produce a guaranteed fast/hot VGS bound. Zener steady power is ≤Vsource²/(4Rmin)=33.47 mW for any split at 26 V, but this says nothing about transients. At40 V a nominal 12 V split gives155.3 mW in125 mW R31/R32: another reason40 V cannot be claimed. R35/R36 at 26 V dissipate64.7/67.8 mW with the stated base/collector assumptions; a125°C0805 derated reference is44.1 mW, while85 °C is102.9 mW. See [conditional-derating.csv](conditional-derating.csv);125 °C is a local-component fault/hot screen, not a supported whole-board ambient.
- **PMOS:** CJ3407 is−30 V VDS/±20 V VGS. Charged protected source 26 V followed by drain−13.6 V demands39.6 V differential, beyond rating. The current manufacturer's96.2 °C/W/1.3 W reference requires 1×1 inch FR4, high-coverage2 oz double-sided copper andt≤10 s. It cannot replace the actual board's steady thermal evidence. Neither a reverse-step occurrence nor surviving waveform has been observed here.
- **Diodes:** current manufacturer-authoredMCC MBR0540 sheet Rev3-4-12012020 specifies operatingTJ≤125 °C,0.5 A atTA50 °C and244 °C/W on its specified FR4 lands. At356.66 mA×0.55 V=196 mW, that reference rise47.9 °C reaches133 °C at 85 °C ambient. This is a mixed-condition upper-drop screen, not an observed fault or an all-temperature VF guarantee. At13.6 V the converted current proxy162.56 mA gives89.4 mW/21.8 °C rise. Current-primary rating and exact lot evidence must govern; older150 °C sheets cannot silently supersede it. PMEG2010ER's20 V reverse and0.34 V@1 A/25 °C limits remain independent; reverse leakage/thermal runaway need checking.
- **TVS and fuse:** SUNMATE SMF16A has16 V stand-off,17.8–19.7 V breakdown at 1 mA,26 V clamp at 7.7 A/10/1000 µs/25 °C,200 W for that pulse and385 mW DC under its stated mounting. Its printedDC derating4 mW/°C and325 °C/W reference must not be treated as a universal sustained shunt rating. The switch current limiter is **downstream** of the TVS. An illustrative8 A×26 V×0.20 s=41.6 J fault demand is not a permissibleTVS energy. The PPTC0.20 s trip reference at 8 A is not a survival coordination proof. Repetition, source impedance, current, overshoot and fault duration remain unknown.
- **Retry/hard short:** max partialCL704 mA×26 V×45 ms gives0.824 J electrical demand in one switch attempt, or0.431 J at 13.6 V. Thermal interruption can change it. The5.3% maximum partial retry duty is not a junction-temperature guarantee, and the40 mJ inductive turn-off energy rating is a different test. Unloaded510 mA×35 ms=17.85 mC charge budget excludes converter, RF and all startup loads.
- **Capacitors:** C9/C10 are50 V at V_INPUT, C20/C21 are50 V at protected nodes; at 26 V their nominal voltage utilization is52%. C18/C19 see gate-source differential, not raw source-to-GND voltage. C16/C17 and the low rails are25 V; they do not improve the upstream PMOS/buck limits. Nominal stored energy: C9 10 µF at 26 V=3.38 mJ; each1 µF protected-node cap=0.338 mJ;44 µF buck output at 5 V=0.550 mJ. These nominal energies exclude effective capacitance/DC bias, modules, cable inductance and source replenishment. Exact node/part register: [capacitor-node-register.csv](capacitor-node-register.csv).

## Bounded next actions

1. **Now, without changing hardware:** preserve architecture and history; update/retain exact current-primary ratings, the actual module conversion paths, declared rail domains and the200 mA legacy capability blocker. Correct a stale regulator alias only as a separately verified numbered-pin metadata correction. Keep current and voltage scenarios visibly conditional.
2. **Legacy rated-capability repair needs a decision:** a new Rev2 candidate requires a verified continuous3V3 supply that supports Espressif's≥500 mA module provision with a separately allocated carrier-current allowance, plus appropriate dropout, thermals, reverse bias and numerical-pin compatibility. A typical500 mA short-circuit limit is insufficient. No exact drop-in substitute is established by this review. Merely changing the BOM to a larger number, enlarging the fuse or suppressing brownout does not close the issue.
3. **Rev3 local component options remain conditional:** if the agreed OEM/temperature/load envelope requires more D14/D15 current or less drop than the exact part supplies, review a higher-thermal/lower-drop diode with the same two original OR functions and verified footprint/polarity. If sustained high-source or local temperature requires moreR31/R32/R35/R36 dissipation, review higher-power exact resistors with retained values/functions. These are bounded candidates for review; no costed exact substitute or mandatory repair follows from an unknown envelope.
4. **No source narrowing to force a pass:** retain intended nominal 5/7.5/9/13.6 V cases. Obtain OEM supply tolerance, allowance, impedance and measured positive/negative waveforms, then decide acceptance criteria and any necessary repair. Require controlled startup/RF/brownout/handoff/USB/backfeed/thermal and source-energy evidence on actual hardware before compatibility or manufacturing claims.

## Reproducibility and primary sources

`analyze_power.py` (original analytical helper; recorded data/formulas below) emits the source-hash manifest, all-seven numbered-net/PCB-pad audit, capacitor register, conditional input/C6/derating sweeps and [calculations.json](calculations.json). It uses algebra only. No unverifiable generic simulator, inferred OEM voltage/current envelope or physical measurement is represented as evidence.

Primary sources used for the common Rev3 chain: [TI TPS1H200A RevE/May2026](https://www.ti.com/lit/ds/symlink/tps1h200a-q1.pdf), [Diodes AP63205 DS41326 Rev3-2/November2024](https://www.diodes.com/assets/Datasheets/AP63200-AP63201-AP63203-AP63205.pdf), [Littelfuse1812L/June2024](https://www.littelfuse.com/assetdocs/resettable-ptcs-1812l-datasheet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), [Littelfuse1206L manufacturer sheet](https://www.mouser.com/datasheet/2/240/Littelfuse_PTC_1206L_Datasheet_pdf-2956361.pdf), [JSCJ CJ3407 Rev2.3](https://www.jscj-elec.com/pdf/f3fb09e55afae446e8a8f8a35ab44e62.pdf), [MCC MBR0540 primary-authored Rev3-4-12012020 mirror](https://www.megastar.com/content/pdfs/MBR0520-MBR0580%28SOD123%29.pdf), [MCC BZT52 primary-authored sheet](https://www.mouser.com/datasheet/2/258/BZT52C2V4_7eBZT52C75_500mW__SOD_123_-2904721.pdf), [exact SUNMATE SMF sheet](https://jlcpcb.com/api/file/downloadByFileSystemAccessId/8757789523080564736), [Nexperia PMEG2010ER/July2023](https://assets.nexperia.com/documents/data-sheet/PMEG2010ER.pdf), [Panasonic ETQP3M4R7KVP](https://industrial.panasonic.com/ww/products/pt/automotive-inductors/models/ETQP3M4R7KVP), [Diodes AP2112](https://www.diodes.com/datasheet/download/AP2112.pdf), [Diodes74LVC2G07](https://www.diodes.com/datasheet/download/74LVC2G07.pdf), and [UNI-ROYAL resistor family](https://www.royalohm.com/assets/pdf/products/smd/1.pdf).

Exact successfully downloadedPDF byte hashes/URLs/times and failed retrievals are recorded in [primary download manifest](primary-sources/download-manifest.json). Where direct bytes were blocked, verified web-primary content was used and no inventedPDF hash is assigned. The companion module/legacy manifests record their exact primary bytes, native vendor-source hashes and retrieval limits. Main schematic/PCB/netlist inputs are bound by [source-hashes.json](source-hashes.json). This review closes the feasible analytical evidence step, with the stated missing-envelope, missing-guaranteed-maximum and empirical gates explicitly open.
