Dr-Crow/esphome-ge-laundry-uart/pcb/rev2.0/native-review/current-cam/README.txt

CURRENT REV2.0 CAM REVIEW - NOT A MANUFACTURING RELEASE

Generated from the separately cleaned historical Rev2 native source with genuine
KiCad 9.0.9. The original PCBA-OnionStraws-rev2.0.zip remains unchanged and separate.
See ../REVIEW.md and ../reports/source-hashes.json for exact source pairing,
bounded thermal/silkscreen changes, all-severity native results, intentional ERC
alias warnings, native9 cached-fill regeneration differences and limitations.

No voltage/current or appliance qualification is established. Historical U1 boot
loop reports remain. UART RX/TX text uses appliance/attached-programmer direction;
verify the exact endpoint map in ../REVIEW.md before wiring. Supplier CPL rotation adjustments are
unproven. Native placement exports are separate and not supplier approved. Do not
combine current CAM and the original supplier CPL without an assembly review.
