Dr-Crow/esphome-ge-laundry-uart/pcb/rev2.0/native-review/drill-report.txt

Drill report for OnionStraws.kicad_pcb
Created on 2026-10-03T19:22:29-0400

Copper Layer Stackup:
    =============================================================
    L1 :  F.Cu                      front
    L2 :  B.Cu                      back

Drill file 'OnionStraws-PTH.drl' contains
    plated through holes:
    =============================================================
    T1  0.300mm  0.0118"  (12 holes)
    T2  0.400mm  0.0157"  (76 holes)
    T3  0.760mm  0.0299"  (8 holes)
    T4  1.000mm  0.0394"  (6 holes)

    Total plated holes count 102

Drill file 'OnionStraws-NPTH.drl' contains
    unplated through holes:
    =============================================================
    T1  0.991mm  0.0390"  (3 holes)
    T2  3.200mm  0.1260"  (4 holes)

    Total unplated holes count 7
