Dr-Crow/esphome-ge-laundry-uart/pcb/rev2.0/native-review/proof/README-NORMALIZATION.md

# Historical comparator boundary

The original verify_cleanup.py and input fingerprints remain frozen to the native
cleanup before schematic alias normalization. They reject later annotation
changes and are not presented as a pass on current source. Current presentation
changes are narrowly enumerated and independently verified in
../../validation/erc-normalization/DELTA-AND-INTEGRATION.md with native graph,
board metadata, detached-source controls and preservation receipts.
No historical baseline, original library definition or source blob is rewritten.
