Dr-Crow/esphome-ge-laundry-uart/case/rev3a/images/case-options.png

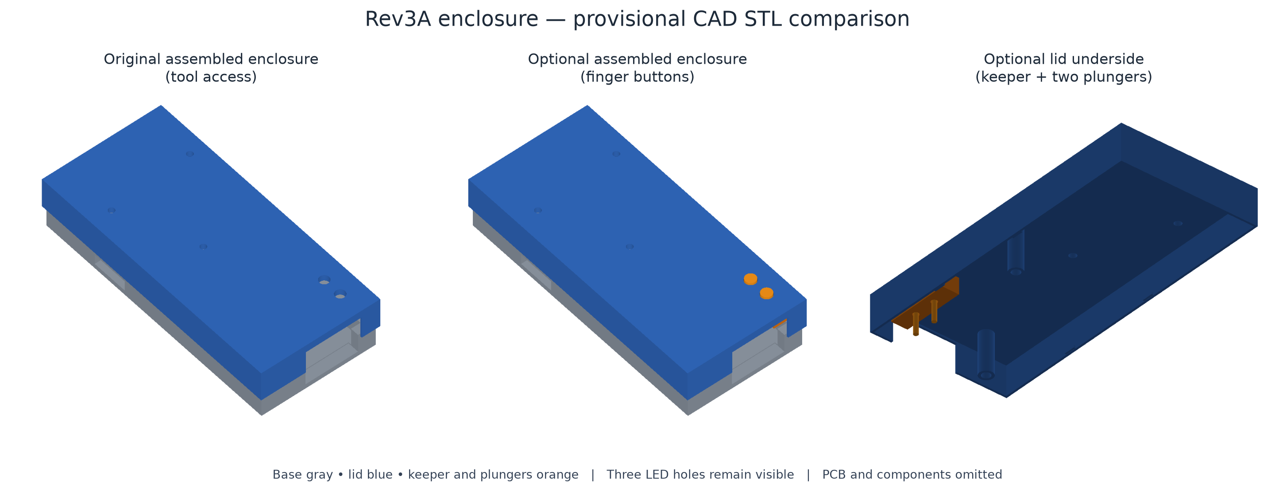
case/rev3a/images/case-options.png
