Dr-Crow/esphome-ge-laundry-uart/case/rev3b/images/rev3b-cad-preview.png

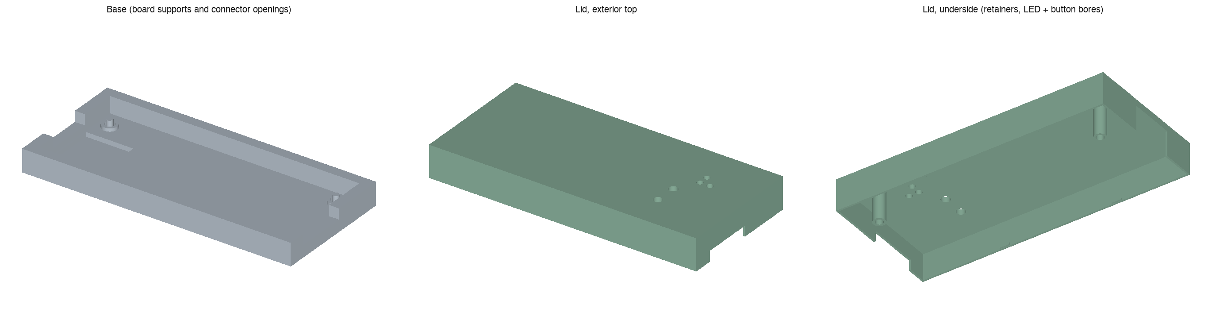
case/rev3b/images/rev3b-cad-preview.png
