Dr-Crow/esphome-ge-laundry-uart/case/rev3c/analytical/review/module-and-wrong-lid-datums.png

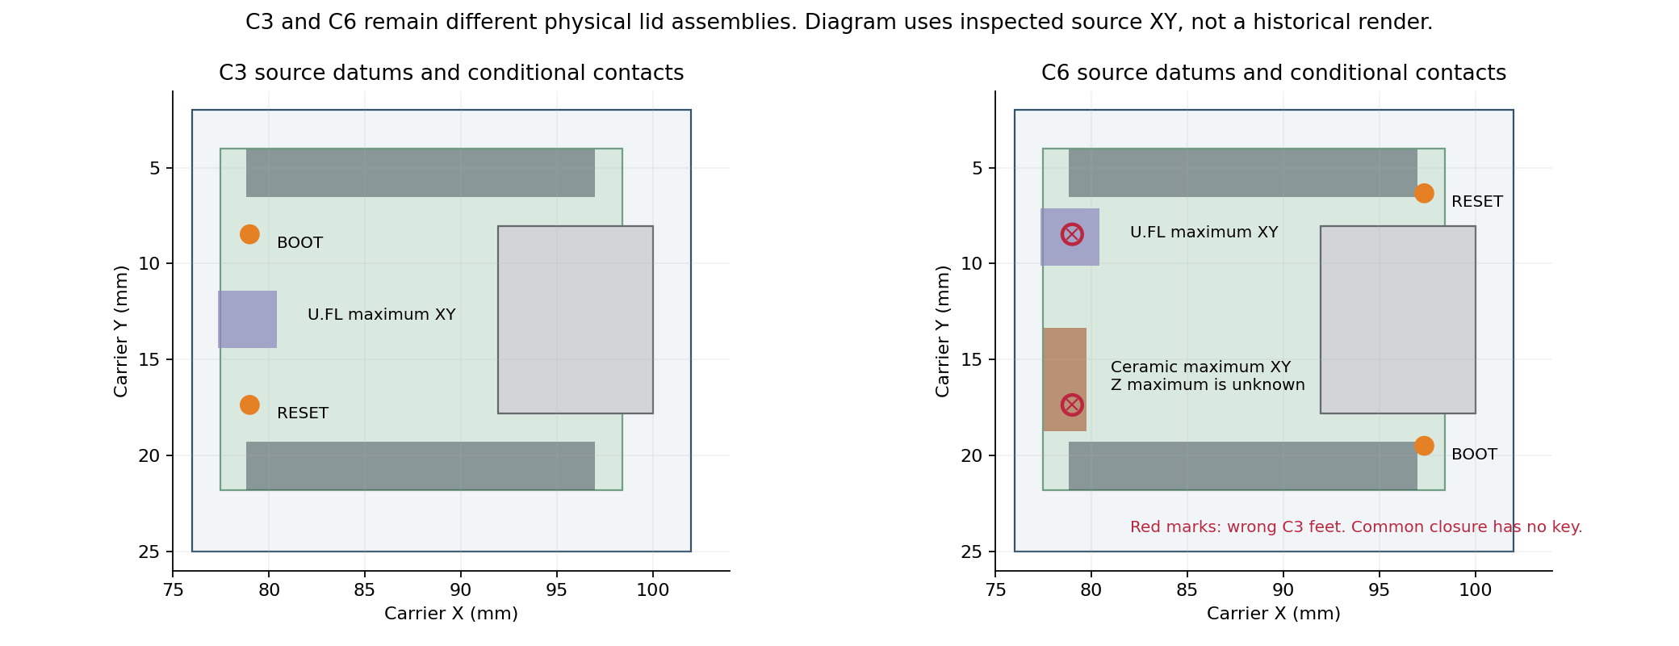
case/rev3c/analytical/review/module-and-wrong-lid-datums.png
