Dr-Crow/esphome-ge-laundry-uart/case/rev3c/analytical/review/presentation_roof_c3.png

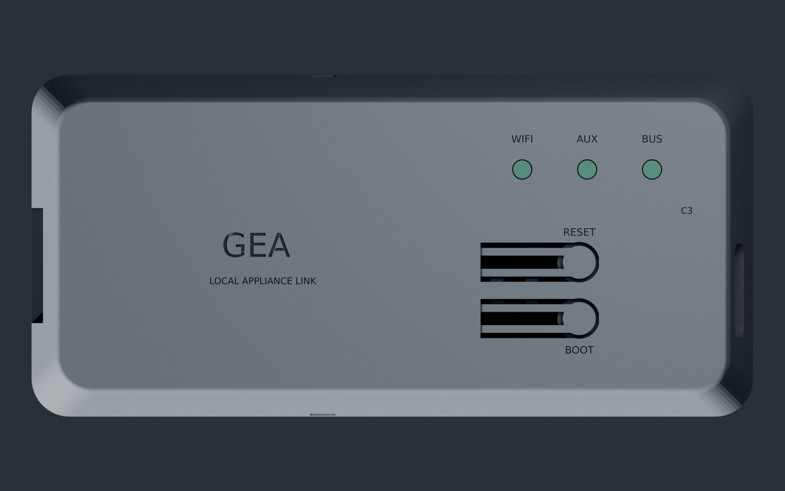
case/rev3c/analytical/review/presentation_roof_c3.png
