Dr-Crow/esphome-ge-laundry-uart/case/rev3c/analytical/review/stack-reach-sweep.png

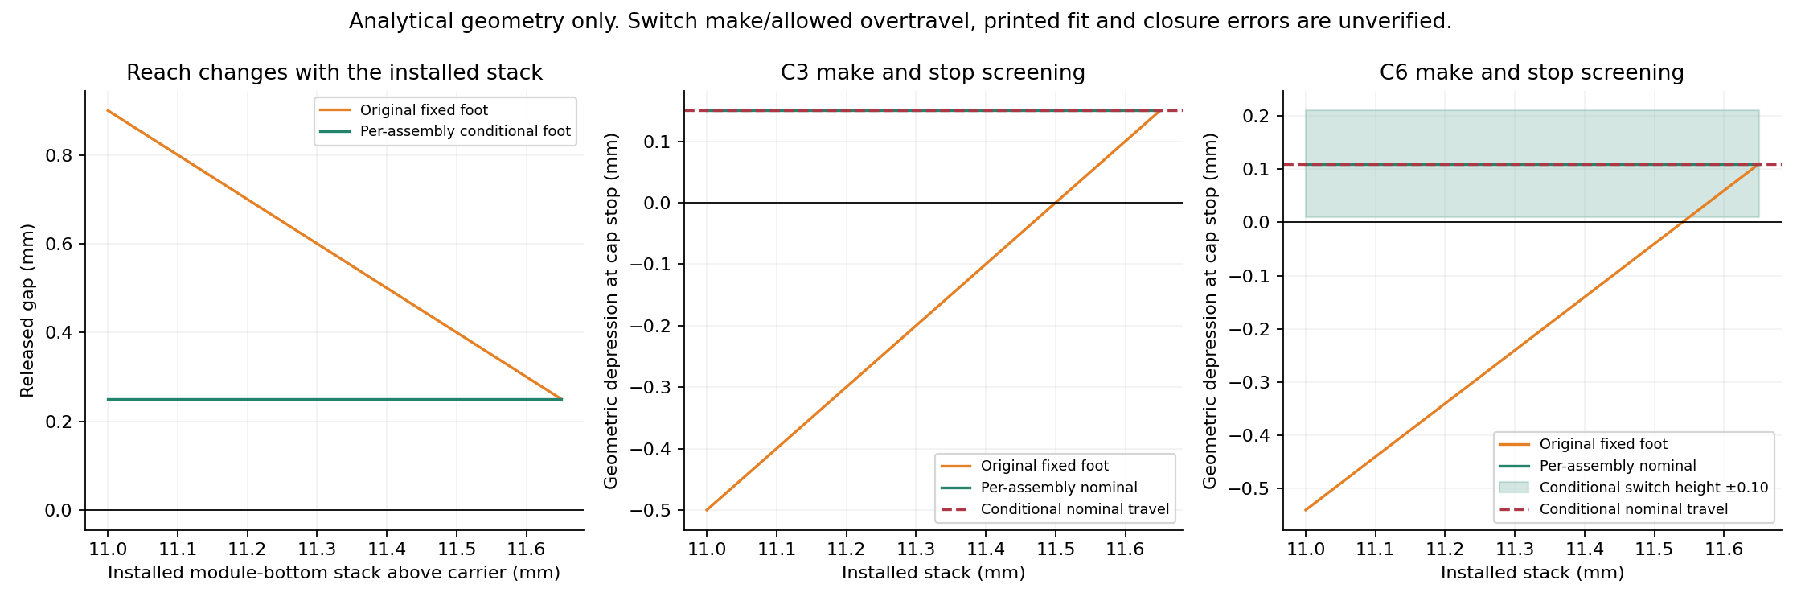
case/rev3c/analytical/review/stack-reach-sweep.png
