Dr-Crow/esphome-ge-laundry-uart/docs/revision-comparison/images/rev2.2/board-oblique.png

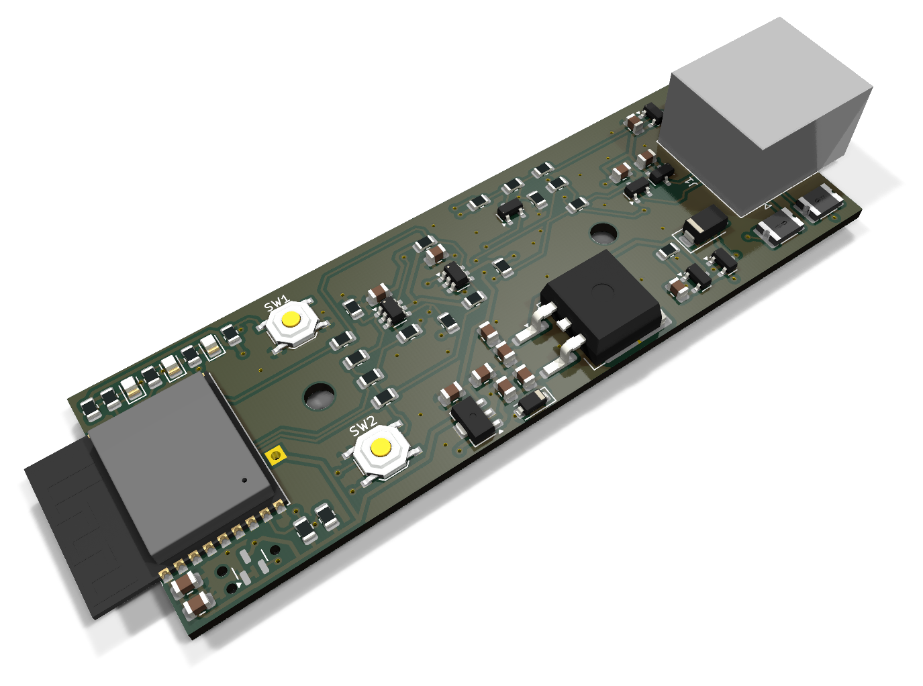
docs/revision-comparison/images/rev2.2/board-oblique.png
