Dr-Crow/esphome-ge-laundry-uart/docs/revision-comparison/images/rev2.2/board-side.png

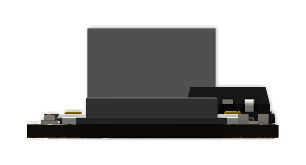
docs/revision-comparison/images/rev2.2/board-side.png
