Dr-Crow/esphome-ge-laundry-uart/docs/revision-comparison/images/rev2.2/case-base-side.png

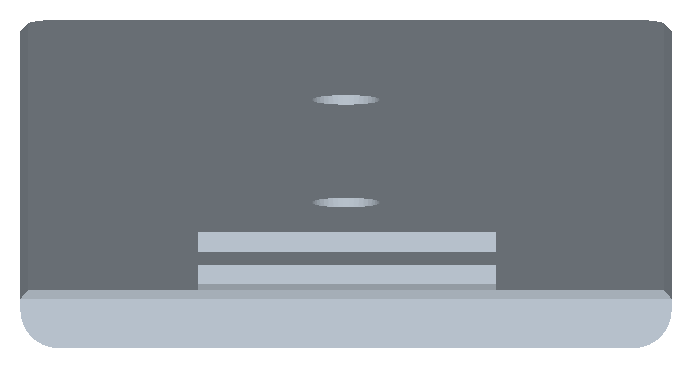
docs/revision-comparison/images/rev2.2/case-base-side.png
