Dr-Crow/esphome-ge-laundry-uart/docs/revision-comparison/images/rev2.2/case-lid-inside.png

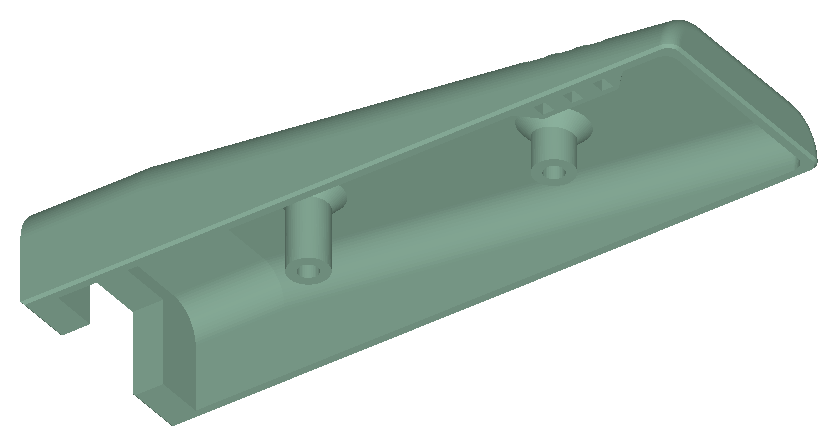
docs/revision-comparison/images/rev2.2/case-lid-inside.png
