Dr-Crow/esphome-ge-laundry-uart/docs/revision-comparison/images/rev3a/board-bottom.png

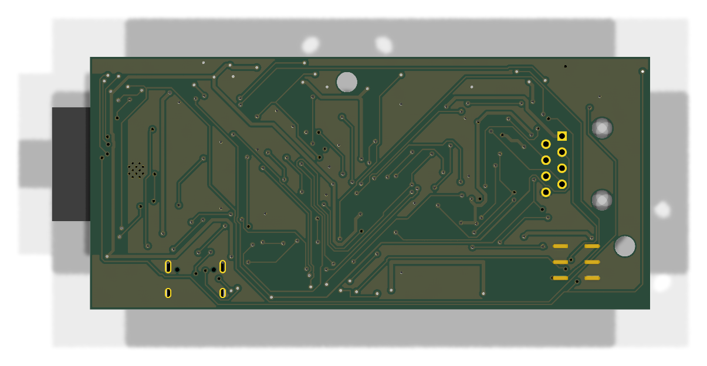
docs/revision-comparison/images/rev3a/board-bottom.png
