Dr-Crow/esphome-ge-laundry-uart/docs/revision-comparison/images/rev3a/board-side.png

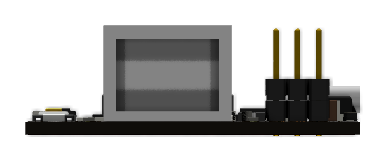
docs/revision-comparison/images/rev3a/board-side.png
