Dr-Crow/esphome-ge-laundry-uart/docs/revision-comparison/images/rev3a/board-top.png

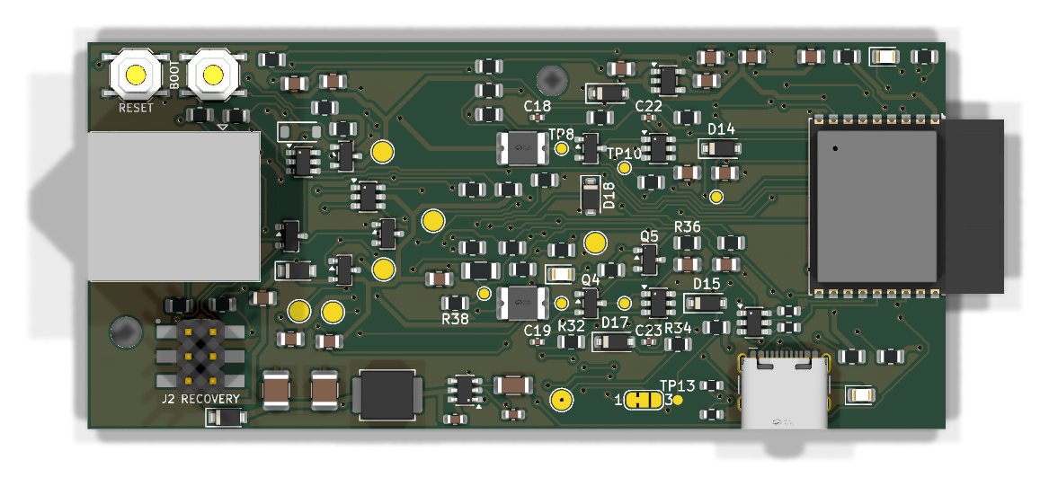
docs/revision-comparison/images/rev3a/board-top.png
