Dr-Crow/esphome-ge-laundry-uart/docs/revision-comparison/images/rev3a/case-base-inside.png

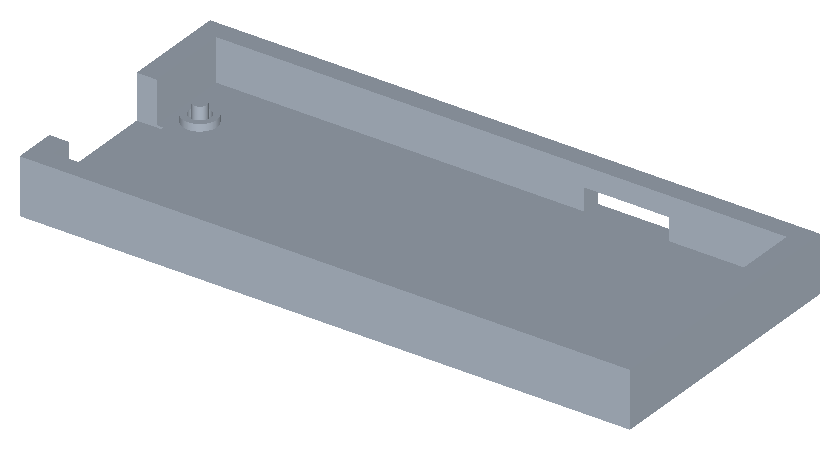
docs/revision-comparison/images/rev3a/case-base-inside.png
