Dr-Crow/esphome-ge-laundry-uart/docs/revision-comparison/images/rev3a/case-base-side.png

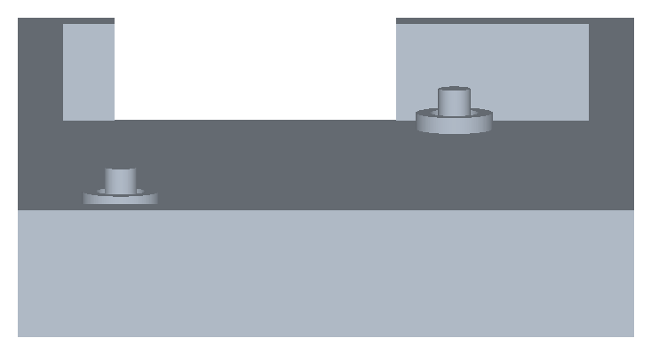
docs/revision-comparison/images/rev3a/case-base-side.png
