Dr-Crow/esphome-ge-laundry-uart/docs/revision-comparison/images/rev3a/case-lid-outside.png

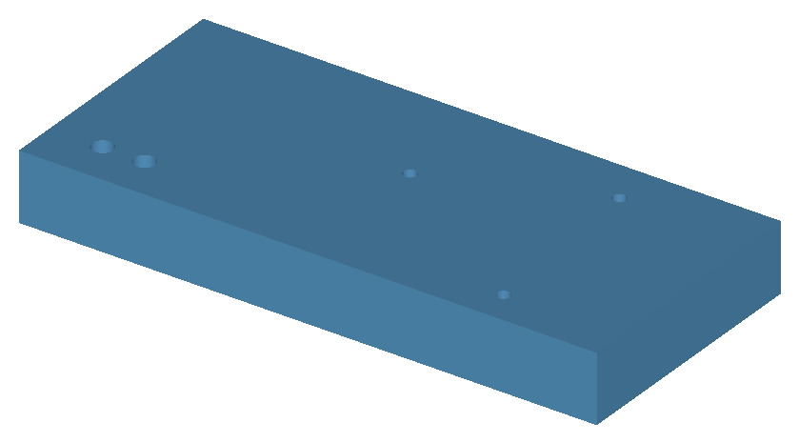
docs/revision-comparison/images/rev3a/case-lid-outside.png
