Dr-Crow/esphome-ge-laundry-uart/docs/revision-comparison/images/rev3b/board-oblique.png

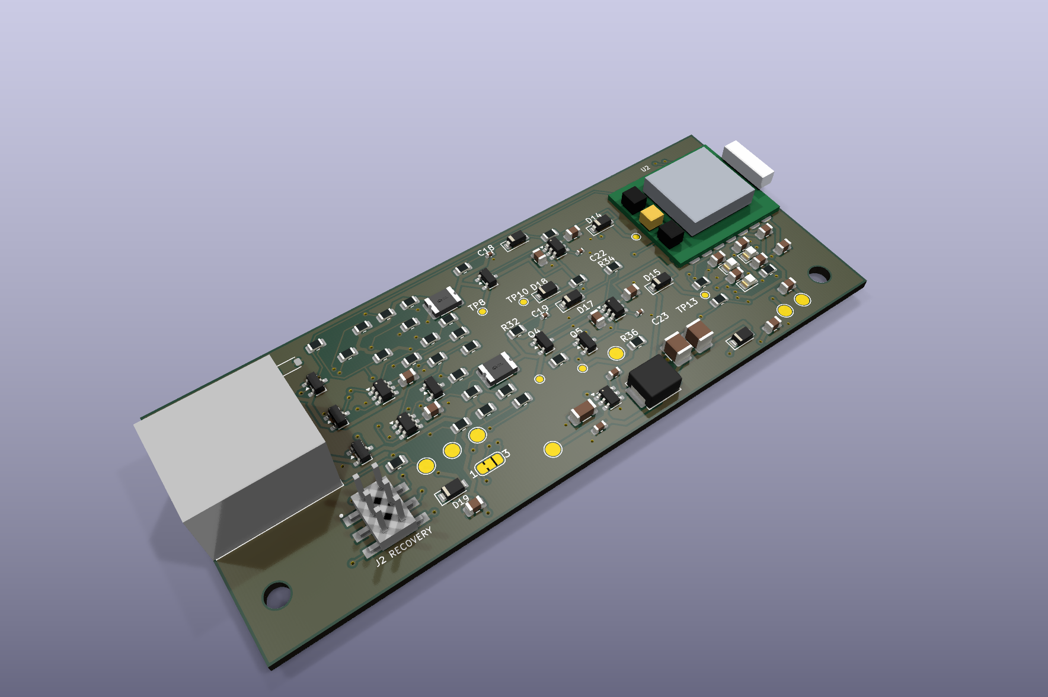
docs/revision-comparison/images/rev3b/board-oblique.png
