Dr-Crow/esphome-ge-laundry-uart/docs/revision-comparison/images/rev3b/board-top.png

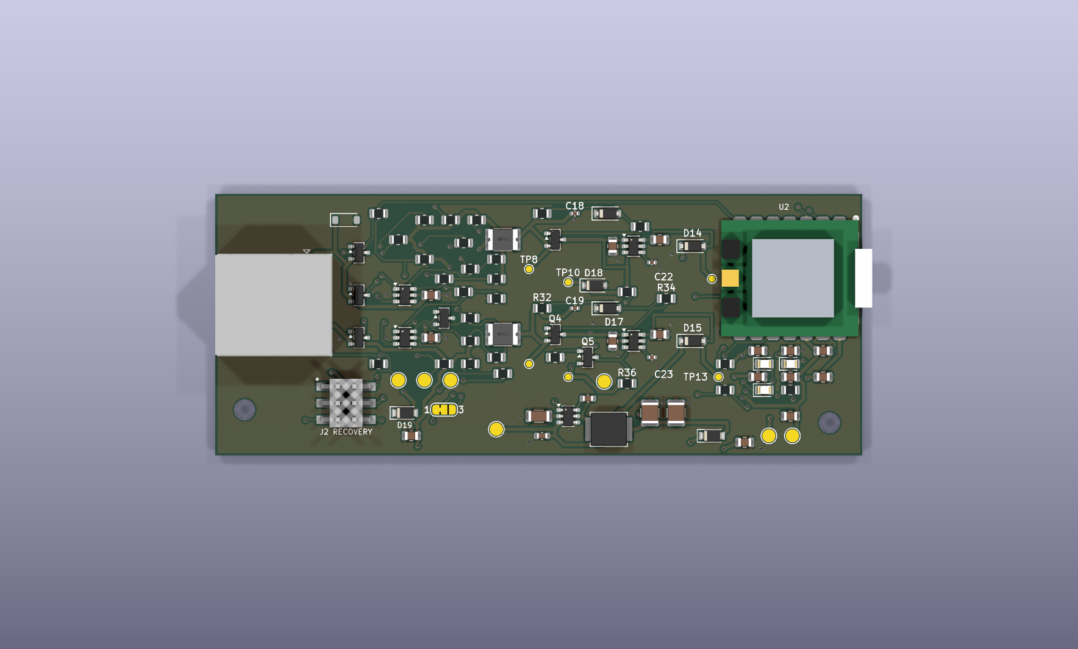
docs/revision-comparison/images/rev3b/board-top.png
