Dr-Crow/esphome-ge-laundry-uart/docs/revision-comparison/images/rev3b/case-closed.png

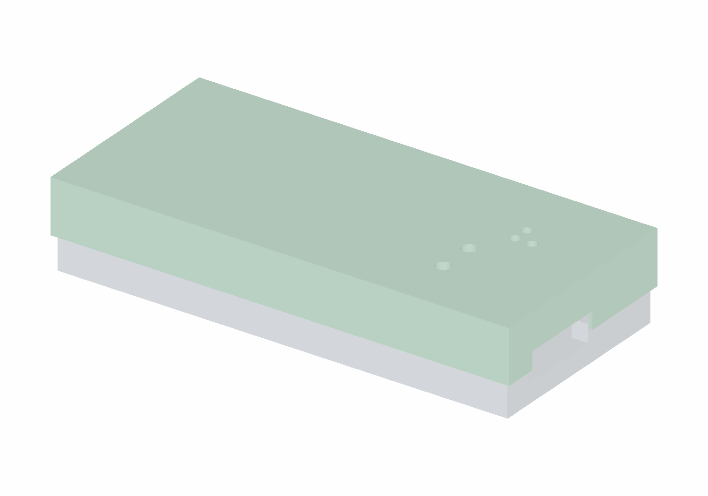
docs/revision-comparison/images/rev3b/case-closed.png
