Dr-Crow/esphome-ge-laundry-uart/docs/revision-comparison/images/rev3b/case-exploded.png

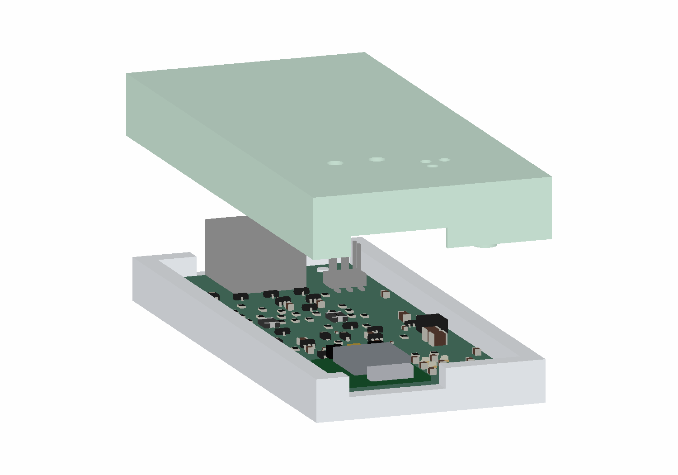
docs/revision-comparison/images/rev3b/case-exploded.png
