Dr-Crow/esphome-ge-laundry-uart/docs/revision-comparison/images/rev3b/case-open.png

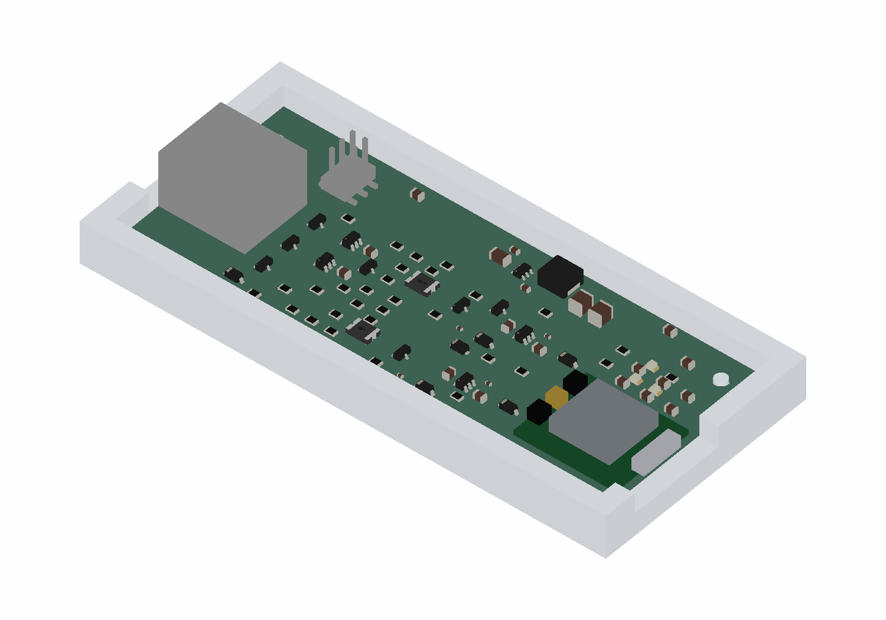
docs/revision-comparison/images/rev3b/case-open.png
