Dr-Crow/esphome-ge-laundry-uart/docs/revision-comparison/images/rev3b/case-side.png

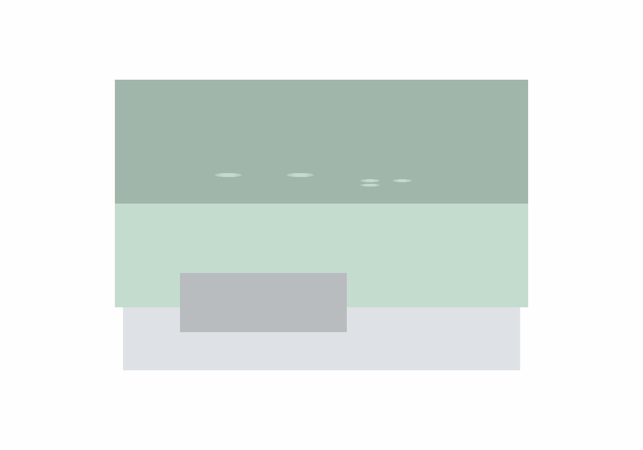
docs/revision-comparison/images/rev3b/case-side.png
