Dr-Crow/esphome-ge-laundry-uart/docs/revision-comparison/images/rev3c/board-bottom.png

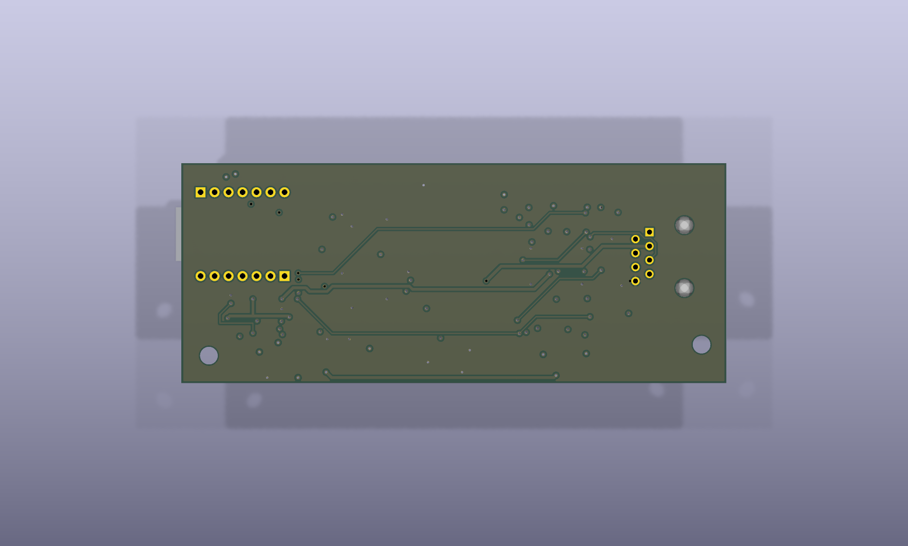
docs/revision-comparison/images/rev3c/board-bottom.png
