Dr-Crow/esphome-ge-laundry-uart/docs/revision-comparison/images/rev3c/case-side.png

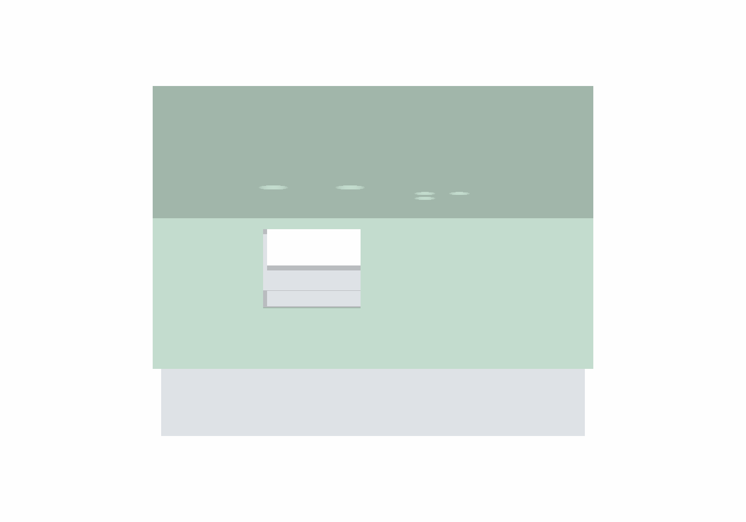
docs/revision-comparison/images/rev3c/case-side.png
