Dr-Crow/esphome-ge-laundry-uart/pcb/rev3/review/3d-isometric.png

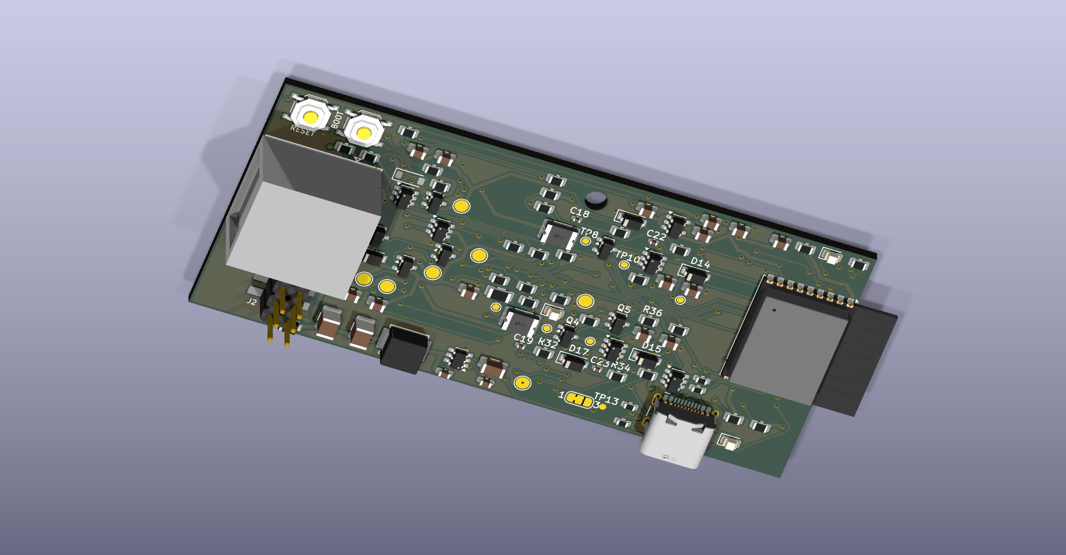
pcb/rev3/review/3d-isometric.png
