Dr-Crow/esphome-ge-laundry-uart/pcb/rev3/review/3d-side.png

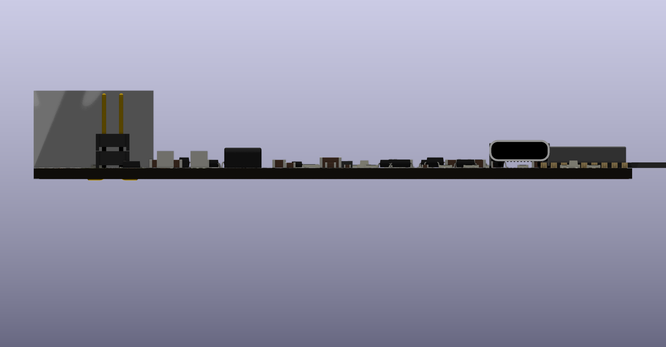
pcb/rev3/review/3d-side.png
