Dr-Crow/esphome-ge-laundry-uart/pcb/rev3/review/bottom.png

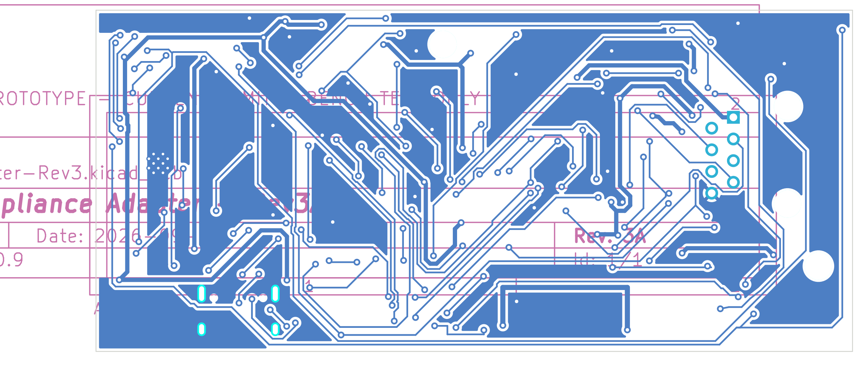
pcb/rev3/review/bottom.png
