Dr-Crow/esphome-ge-laundry-uart/pcb/rev3/review/dimensions.png

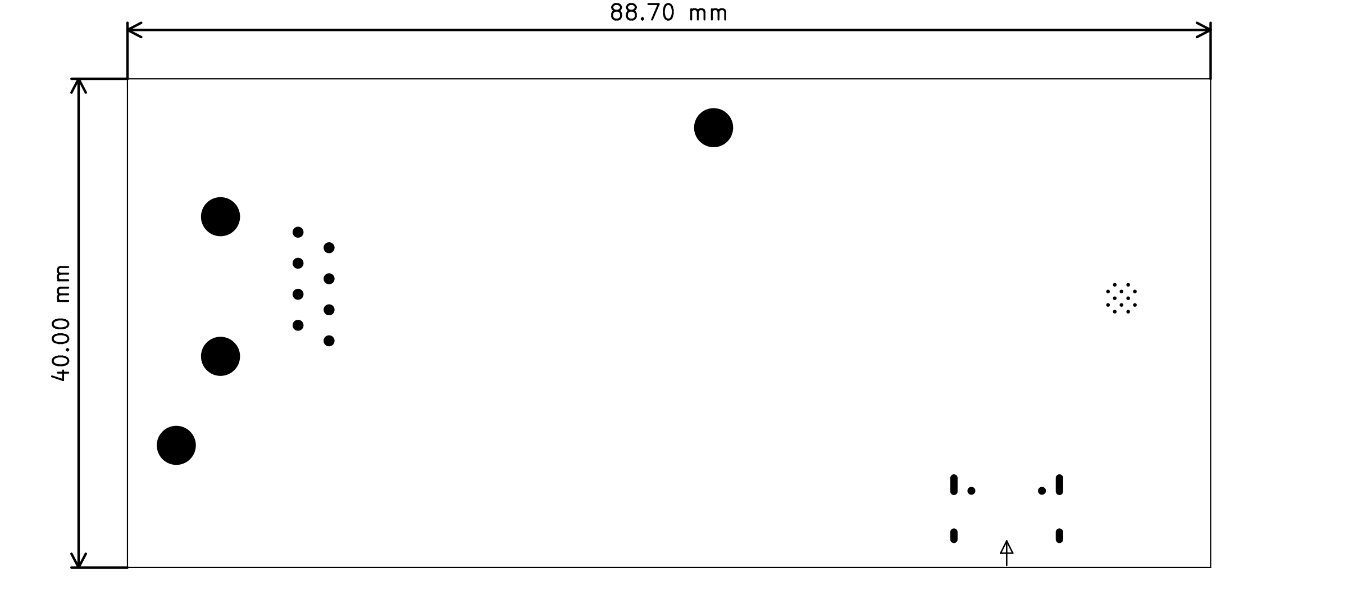
pcb/rev3/review/dimensions.png
