Dr-Crow/esphome-ge-laundry-uart/pcb/rev3/review/inner1.png

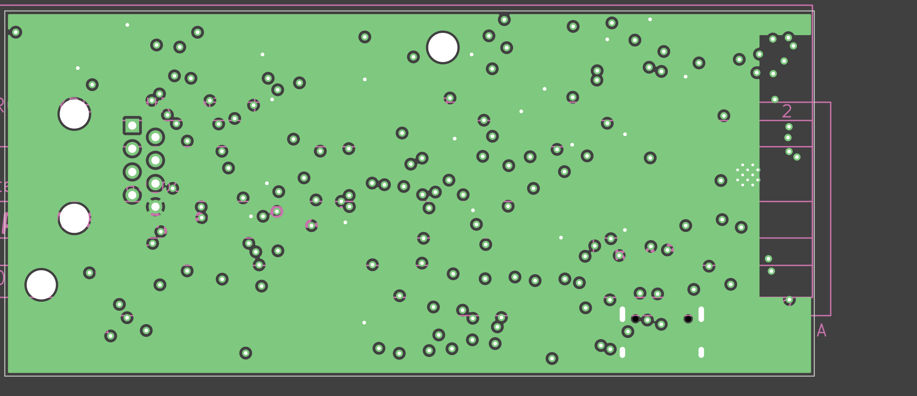
pcb/rev3/review/inner1.png
