Dr-Crow/esphome-ge-laundry-uart/pcb/rev3/review/inner2.png

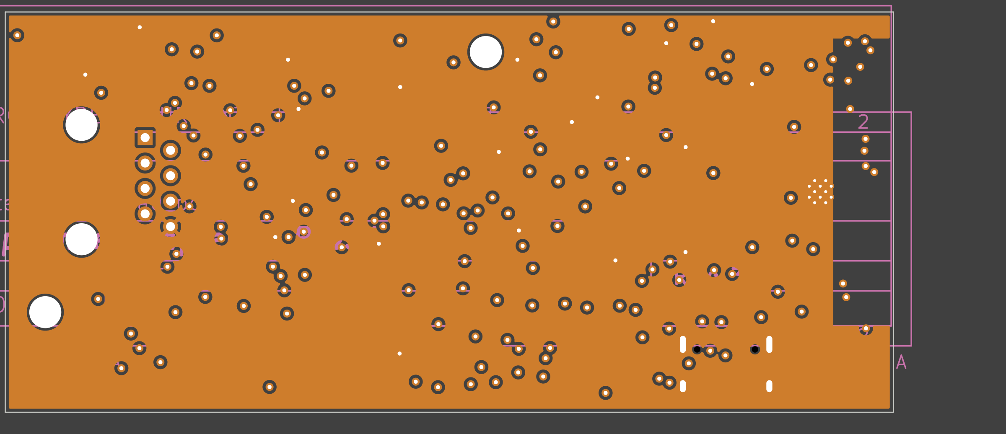
pcb/rev3/review/inner2.png
