Dr-Crow/esphome-ge-laundry-uart/pcb/rev3/review/schematic.png

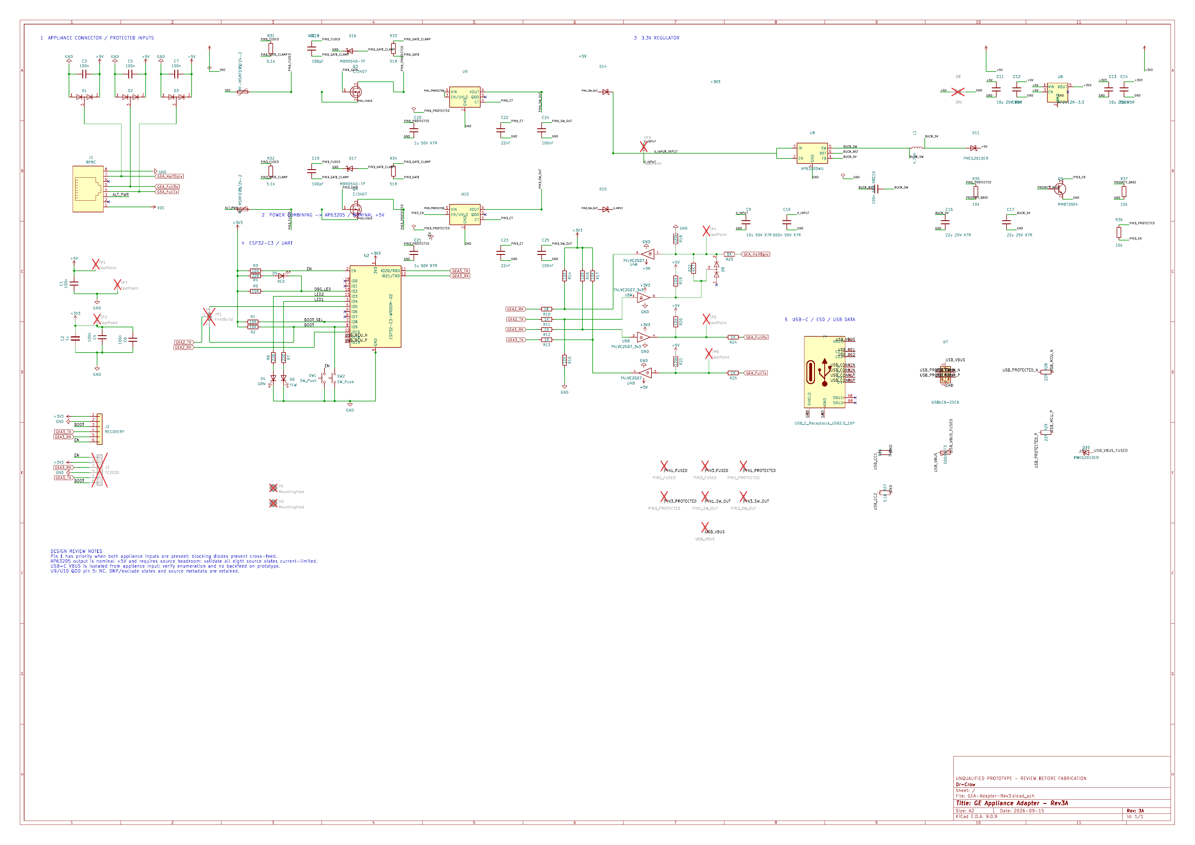
pcb/rev3/review/schematic.png
