Dr-Crow/esphome-ge-laundry-uart/pcb/rev3/review/top.png

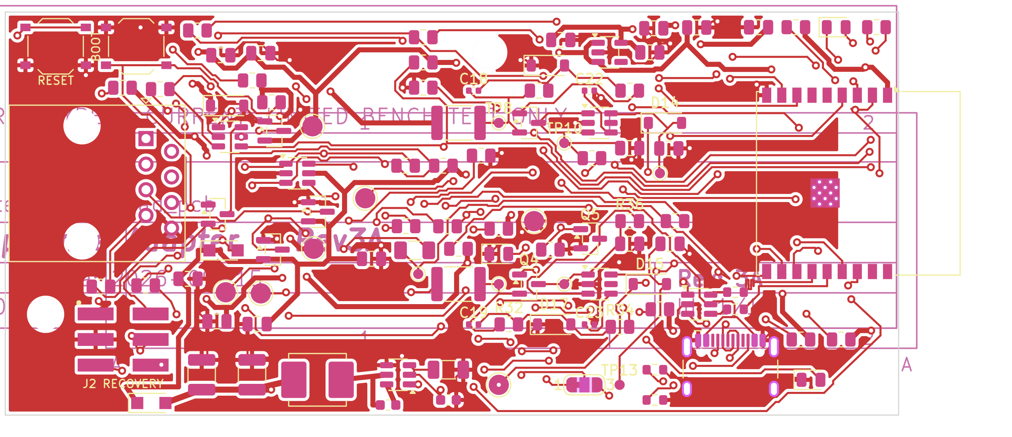
pcb/rev3/review/top.png
