Dr-Crow/esphome-ge-laundry-uart/pcb/rev3a/images/3d-bottom.png

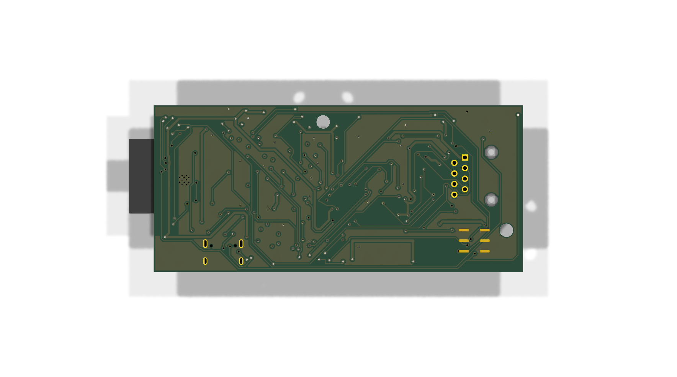
pcb/rev3a/images/3d-bottom.png
