Dr-Crow/esphome-ge-laundry-uart/pcb/rev3a/images/3d-side.png

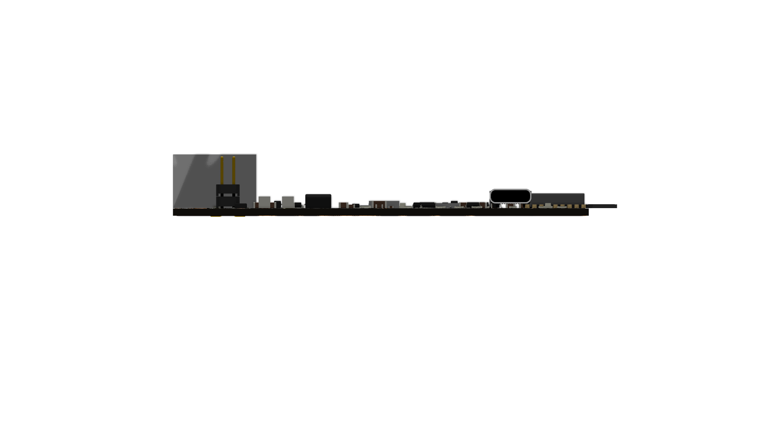
pcb/rev3a/images/3d-side.png
