Dr-Crow/esphome-ge-laundry-uart/pcb/rev3b/images/rev3b-render-bottom.png

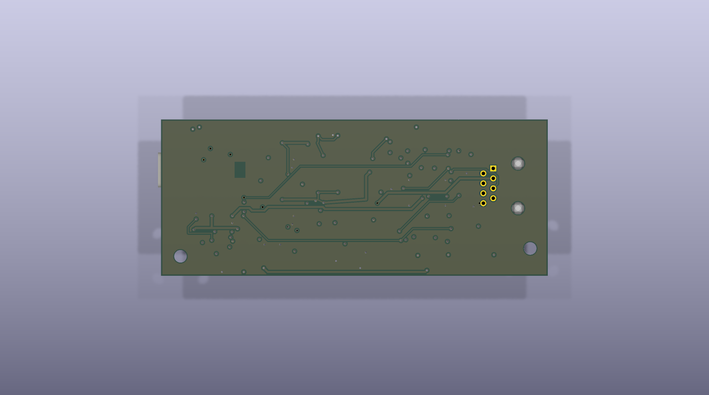
pcb/rev3b/images/rev3b-render-bottom.png
