Dr-Crow/esphome-ge-laundry-uart/pcb/rev3c/images/model-comparison/before-bottom.png

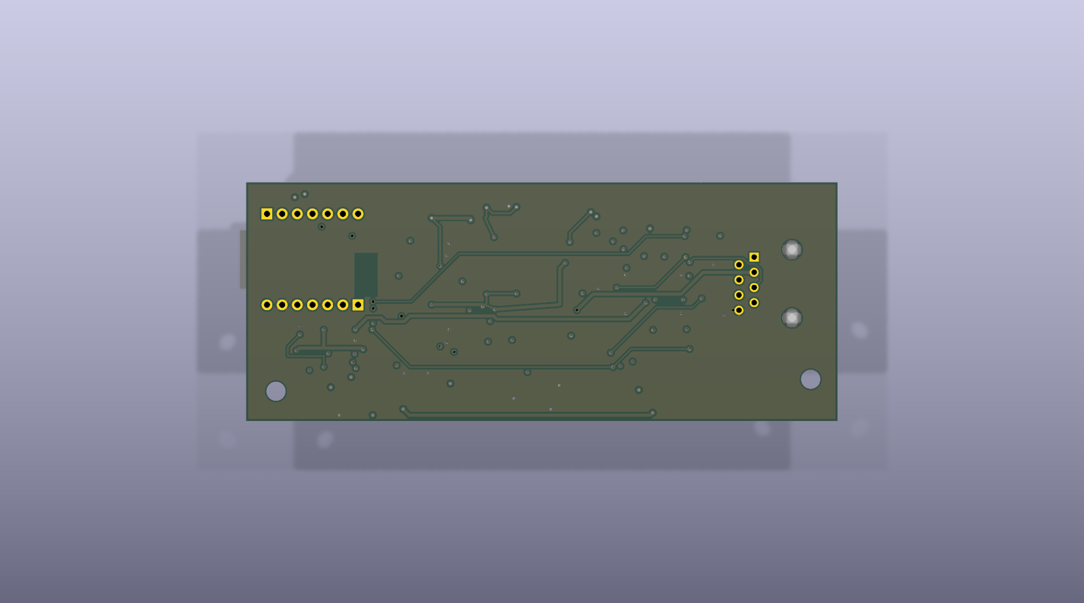
pcb/rev3c/images/model-comparison/before-bottom.png
