Dr-Crow/esphome-ge-laundry-uart/pcb/rev3c/images/rev3c-render-c6-top.png

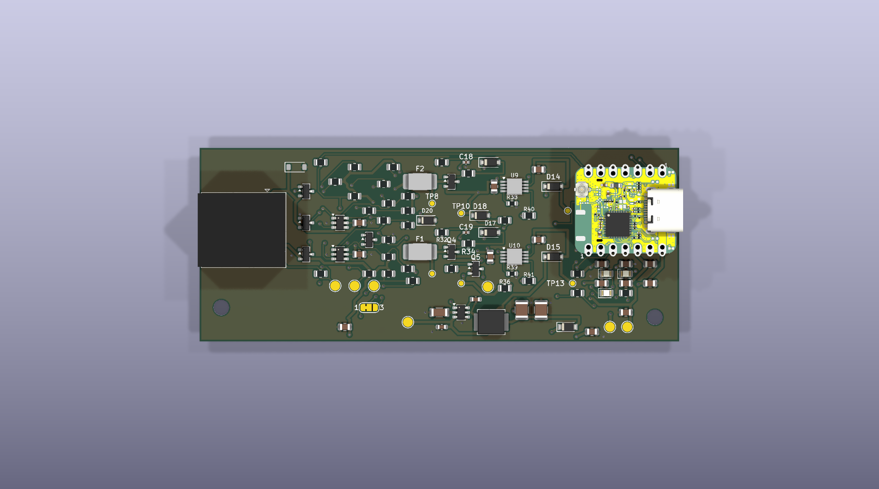
pcb/rev3c/images/rev3c-render-c6-top.png
