Dr-Crow/esphome-ge-laundry-uart/case/rev3a/rev3a_button_plunger.step

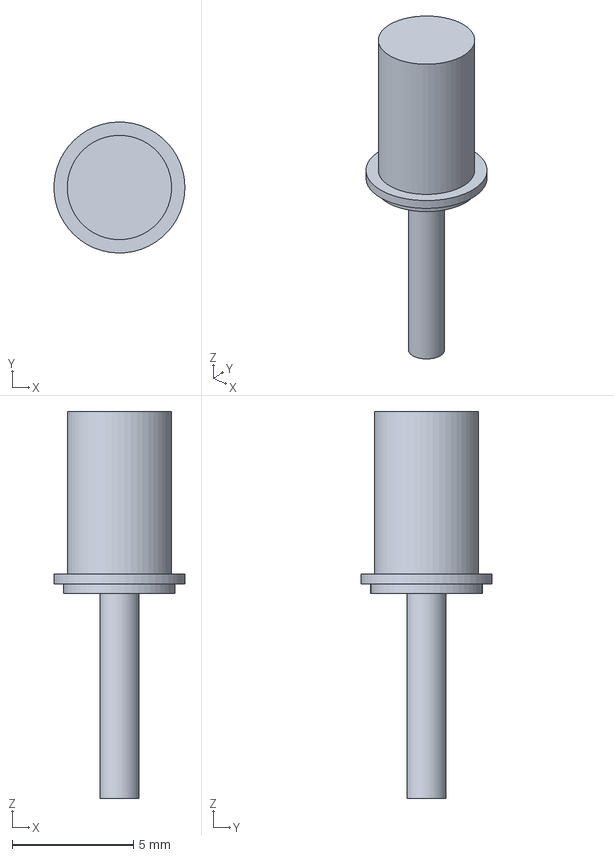
[picture p85: CAD file, 2026-09-28]
case/rev3a/rev3a_button_plunger.step
5.39 x 5.40 x 15.9 mm
