Dr-Crow/esphome-ge-laundry-uart/case/rev3b/exports/rev3b_lid_ant-internal.step

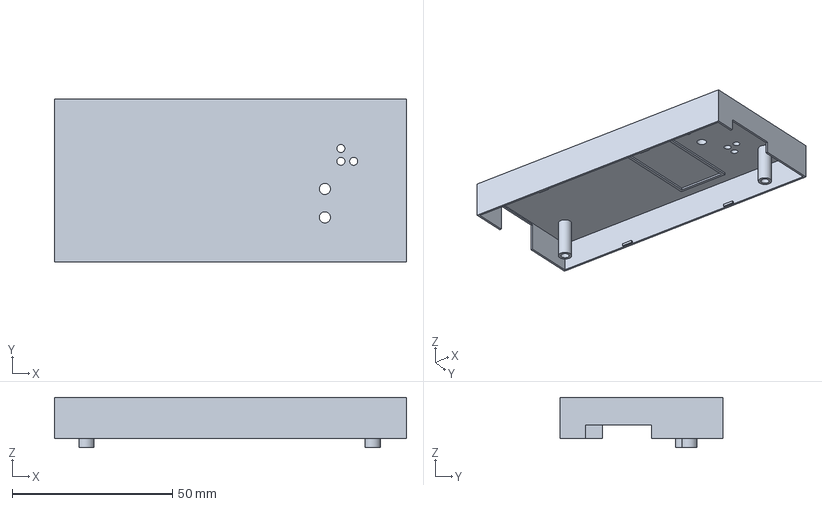
[picture p86: CAD file, 2026-10-02]
case/rev3b/exports/rev3b_lid_ant-internal.step
110.0 x 51.0 x 15.7 mm
