Dr-Crow/esphome-ge-laundry-uart/case/rev3c/exports/rev3c_lid_magnets.step

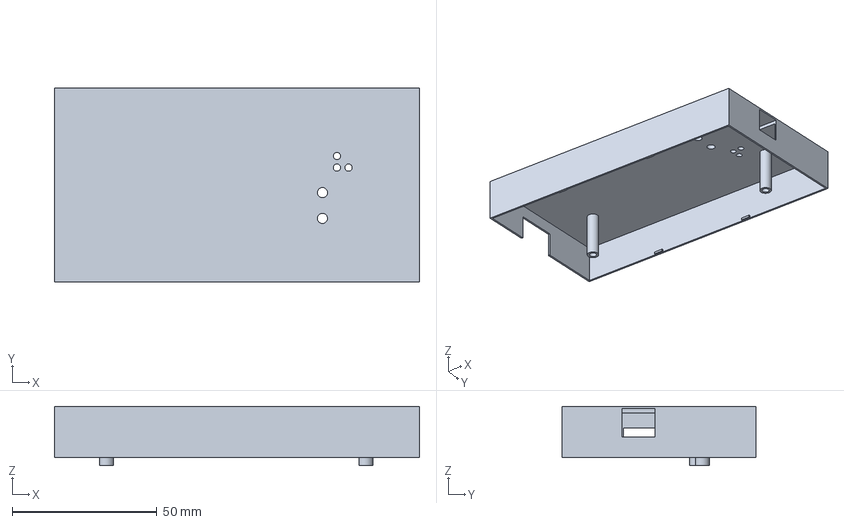
[picture p87: CAD file, 2026-10-01]
case/rev3c/exports/rev3c_lid_magnets.step
126.0 x 67.0 x 20.4 mm
