Dr-Crow/esphome-ge-laundry-uart/pcb/rev3a/design/models/J2-hanxia-HX-PZ-2.54-02-03-S.step

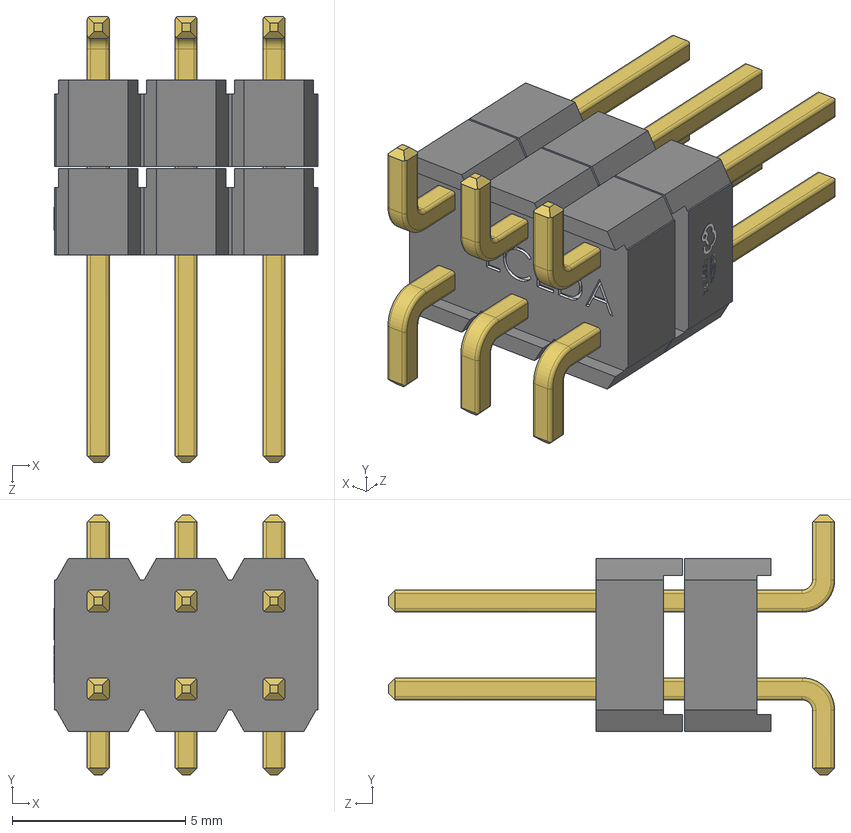
[picture p88: CAD file, 2026-09-15]
pcb/rev3a/design/models/J2-hanxia-HX-PZ-2.54-02-03-S.step
7.63 x 7.50 x 12.9 mm
