Dr-Crow/esphome-ge-laundry-uart/pcb/rev3c/design/models/Socket_HCTL_PM254-1-07-Z-8.5-drawing-detail.step

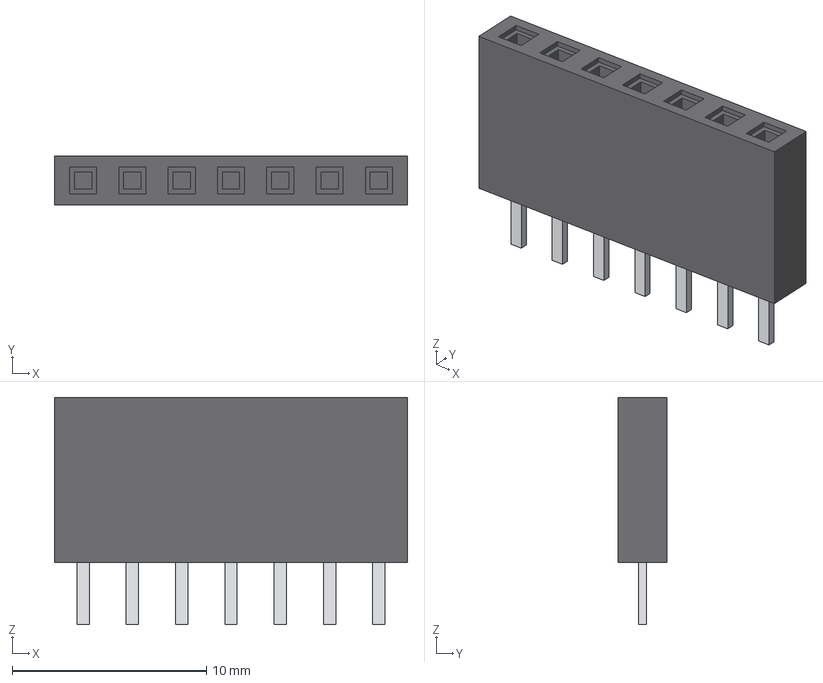
[picture p89: CAD file, 2026-10-04]
pcb/rev3c/design/models/Socket_HCTL_PM254-1-07-Z-8.5-drawing-detail.step
18.2 x 2.50 x 11.7 mm
HCTL PM254 drawing body; illustrative receiving recesses
PM254 nominal tail 1
PM254 nominal tail 2
PM254 nominal tail 3
PM254 nominal tail 4
PM254 nominal tail 5
PM254 nominal tail 6
PM254 nominal tail 7
