Dr-Crow/esphome-ge-laundry-uart/case/rev3a/rev3a_base.step

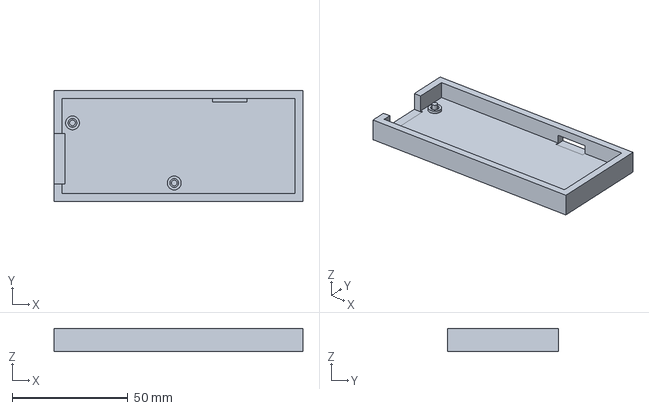
[picture p90: CAD file, 2026-09-15]
case/rev3a/rev3a_base.step
107.7 x 48.0 x 10.0 mm
