Dr-Crow/esphome-ge-laundry-uart/case/rev3c/exports/rev3c_base_ant-external.step

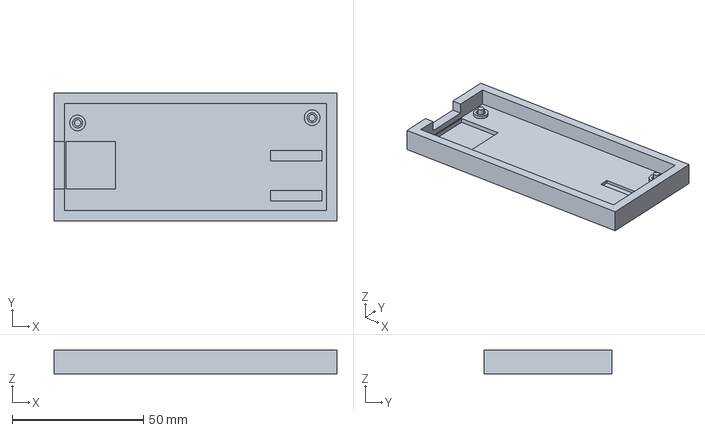
[picture p91: CAD file, 2026-10-01]
case/rev3c/exports/rev3c_base_ant-external.step
108.0 x 49.0 x 9.00 mm
