Dr-Crow/esphome-ge-laundry-uart/pcb/rev3a/design/models/J1-EVERCOM-5301-8P8C-envelope.step

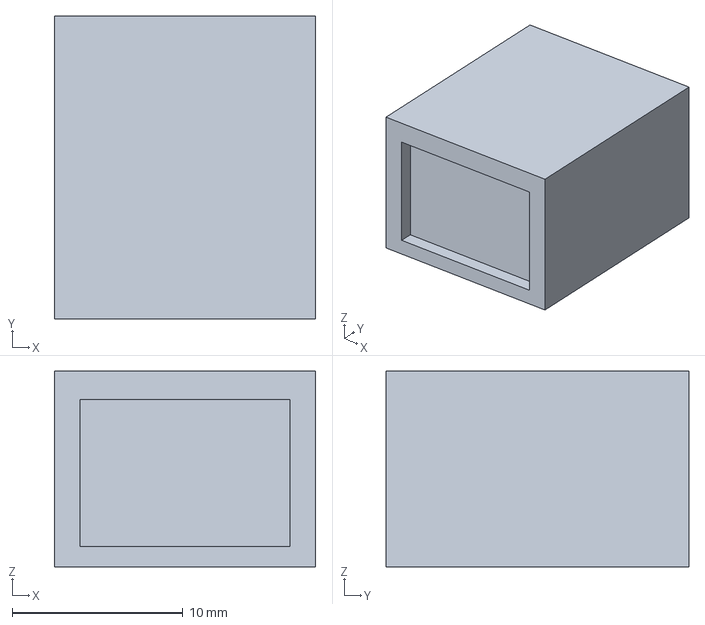
[picture p92: CAD file, 2026-09-15]
pcb/rev3a/design/models/J1-EVERCOM-5301-8P8C-envelope.step
15.3 x 17.7 x 11.4 mm
