Dr-Crow/esphome-ge-laundry-uart/pcb/rev3b/design/models/J2-hanxia-HX-PZ-2.54-02-03-S-drawing.step

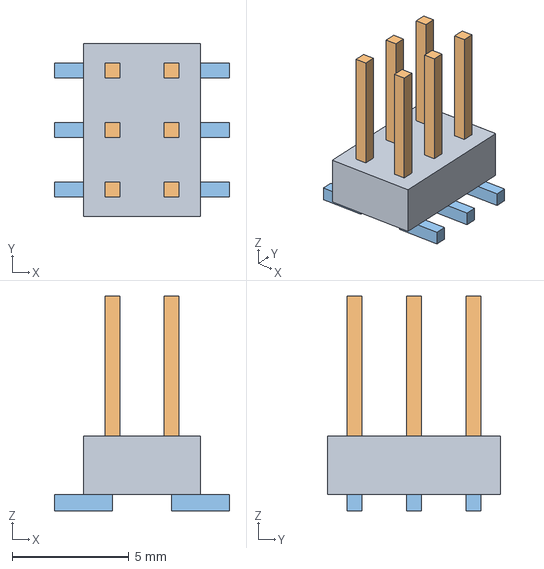
[picture p93: CAD file, 2026-09-30]
pcb/rev3b/design/models/J2-hanxia-HX-PZ-2.54-02-03-S-drawing.step
7.50 x 7.42 x 9.20 mm
