Dr-Crow/esphome-ge-laundry-uart/pcb/rev3c/design/models/U.FL_Hirose_U.FL-R-SMT-1_Vertical-kicad-9.0.9.step

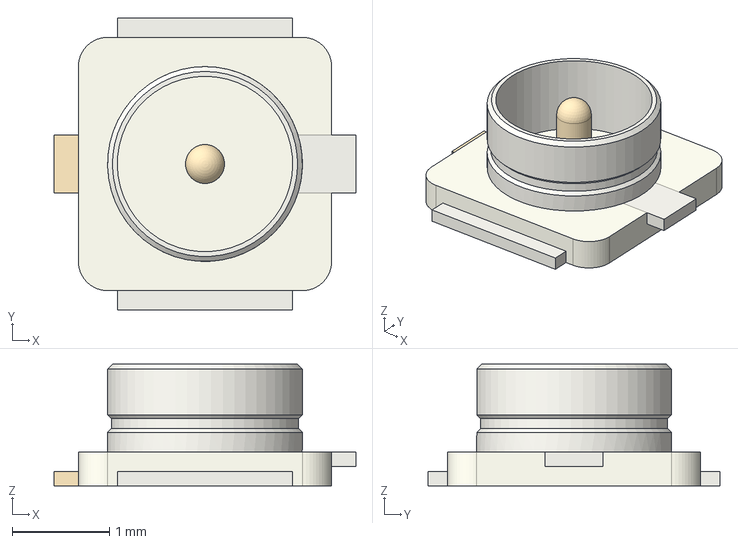
[picture p94: CAD file, 2026-10-04]
pcb/rev3c/design/models/U.FL_Hirose_U.FL-R-SMT-1_Vertical-kicad-9.0.9.step
3.10 x 3.00 x 1.25 mm
