Dr-Crow/esphome-ge-laundry-uart/pcb/rev3a/design/models/J4-SHOU-HAN-TYPE-C-16PIN-2MD-073.step

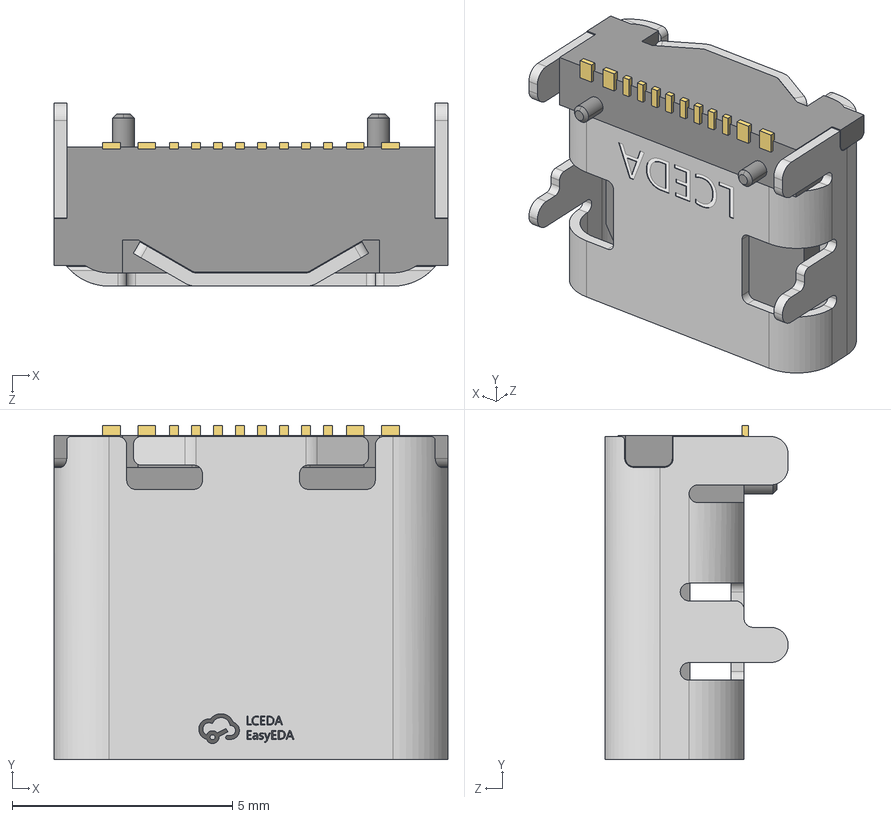
[picture p95: CAD file, 2026-09-15]
pcb/rev3a/design/models/J4-SHOU-HAN-TYPE-C-16PIN-2MD-073.step
8.94 x 7.58 x 4.16 mm
