Dr-Crow/esphome-ge-laundry-uart/pcb/rev3b/design/models/XIAO-ESP32-C3-v1.3-envelope.step

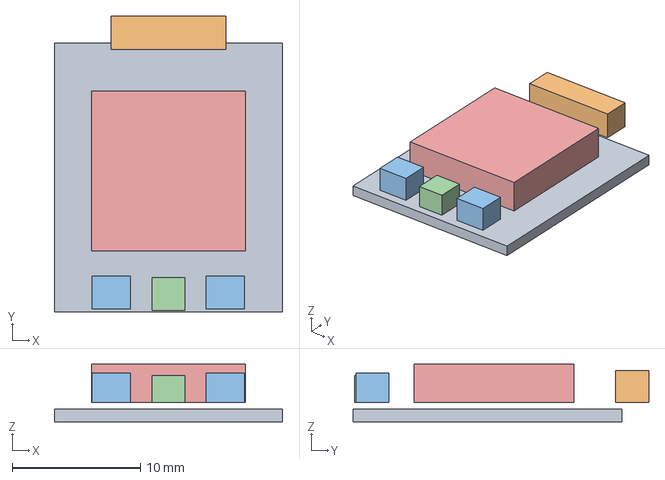
[picture p96: CAD file, 2026-09-28]
pcb/rev3b/design/models/XIAO-ESP32-C3-v1.3-envelope.step
17.8 x 23.1 x 4.50 mm
