Dr-Crow/esphome-ge-laundry-uart/pcb/rev3c/design/models/RJ45_EVERCOM_5301-8P8C-RevA-drawing-detail.step

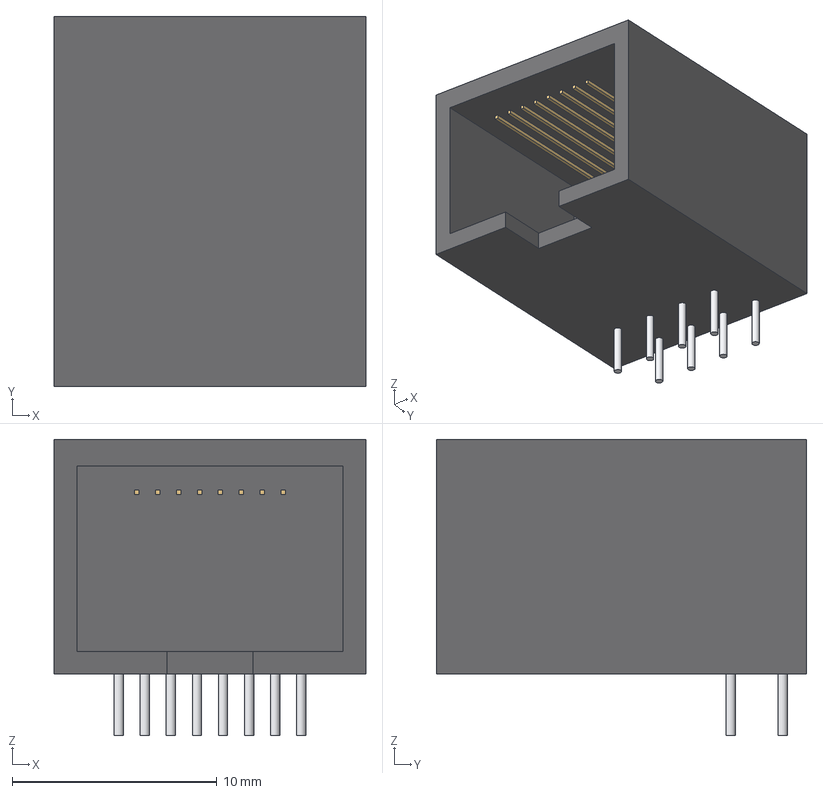
[picture p97: CAD file, 2026-10-04]
pcb/rev3c/design/models/RJ45_EVERCOM_5301-8P8C-RevA-drawing-detail.step
15.2 x 18.1 x 14.4 mm
EVERCOM Rev A drawing body; illustrative internal opening
5301 nominal contact tail 1
5301 illustrative front contact 1
5301 nominal contact tail 2
5301 illustrative front contact 2
5301 nominal contact tail 3
5301 illustrative front contact 3
5301 nominal contact tail 4
5301 illustrative front contact 4
5301 nominal contact tail 5
5301 illustrative front contact 5
5301 nominal contact tail 6
5301 illustrative front contact 6
5301 nominal contact tail 7
5301 illustrative front contact 7
5301 nominal contact tail 8
5301 illustrative front contact 8
