Dr-Crow/esphome-ge-laundry-uart/case/rev3c/exports/rev3c_base_magnets.step

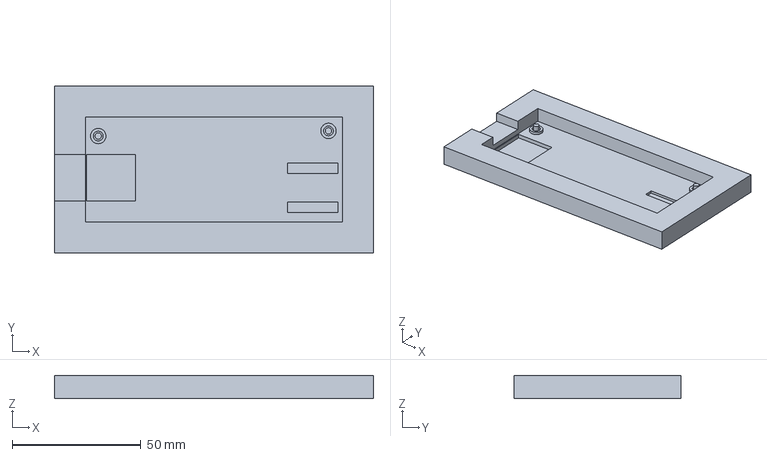
[picture p98: CAD file, 2026-10-01]
case/rev3c/exports/rev3c_base_magnets.step
124.0 x 65.0 x 9.00 mm
