Dr-Crow/esphome-ge-laundry-uart/pcb/rev3c/design/models/Socket_1x07_P2.54mm_HCTL_PM254.step

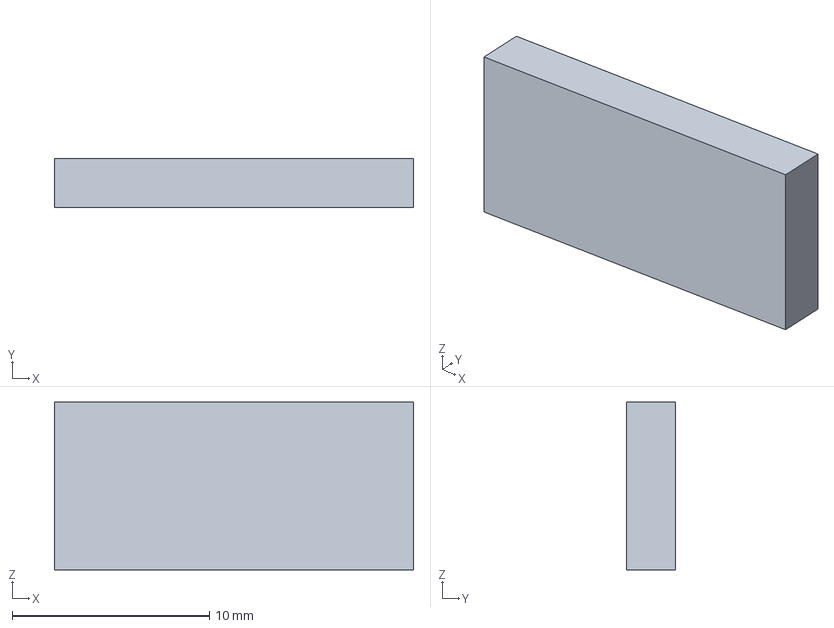
[picture p99: CAD file, 2026-10-01]
pcb/rev3c/design/models/Socket_1x07_P2.54mm_HCTL_PM254.step
18.2 x 2.50 x 8.50 mm
