Dr-Crow/esphome-ge-laundry-uart/pcb/rev3c/design/models/XIAO-ESP32-C3-Rev3C-installed-envelope.step

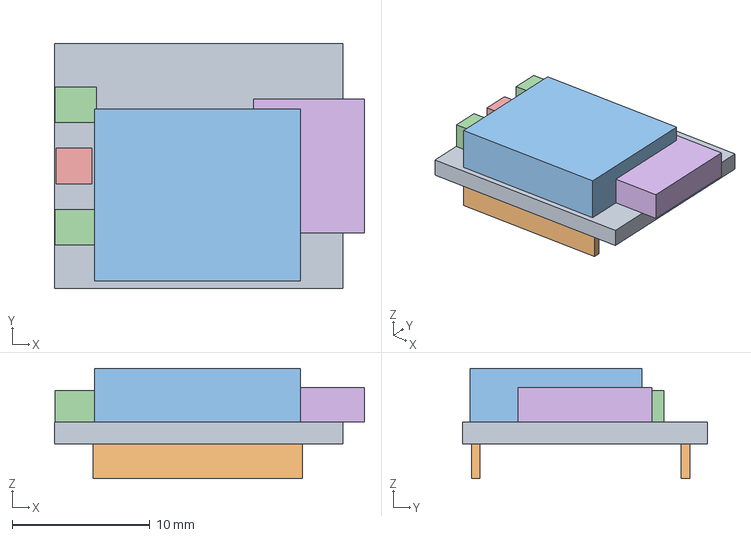
[picture p100: CAD file, 2026-10-01]
pcb/rev3c/design/models/XIAO-ESP32-C3-Rev3C-installed-envelope.step
22.5 x 17.8 x 8.00 mm
