Dr-Crow/esphome-ge-laundry-uart/pcb/rev1.0/review-manufacturing/README.md

# Rev1 current review CAM

Fresh genuine KiCad 9.0.9 exports from the current paired native source, distinct from the untouched historical manufacturing archive. Review CAM contains nine Gerber layers (including explicit empty B.Paste), two Excellon drill files and native job metadata. PTH/NPTH drill-map PDFs are retained separately.

The original package had no BOM/CPL. This directory adds neither supplier selections nor assembly rotation assumptions. It is not a manufacturing-approved package.

See [native review](../validation/NATIVE-REVIEW.md) and the [source/artifact manifest](../validation/native-kicad-9.0.9/manifest.json) for exact source binding, unchanged copper/drill control comparison, bounded front-silk edit and open electrical/physical gates.
