Dr-Crow/esphome-ge-laundry-uart/pcb/rev2.2/manufacturing/original/README.md

# Original public manufacturing files

These are byte-for-byte files from public source `bc0d52495bd97ed1504bd0ca0775e47feb01a648`, retained for history. They predate the source cleanup and corrected silkscreen / U4 zone contact. They are not approved manufacturing inputs and must not be mixed with the regenerated review package in the parent directory.
