Dr-Crow/esphome-ge-laundry-uart/case/rev3c/analytical/review/actual-light-guide-paths.png

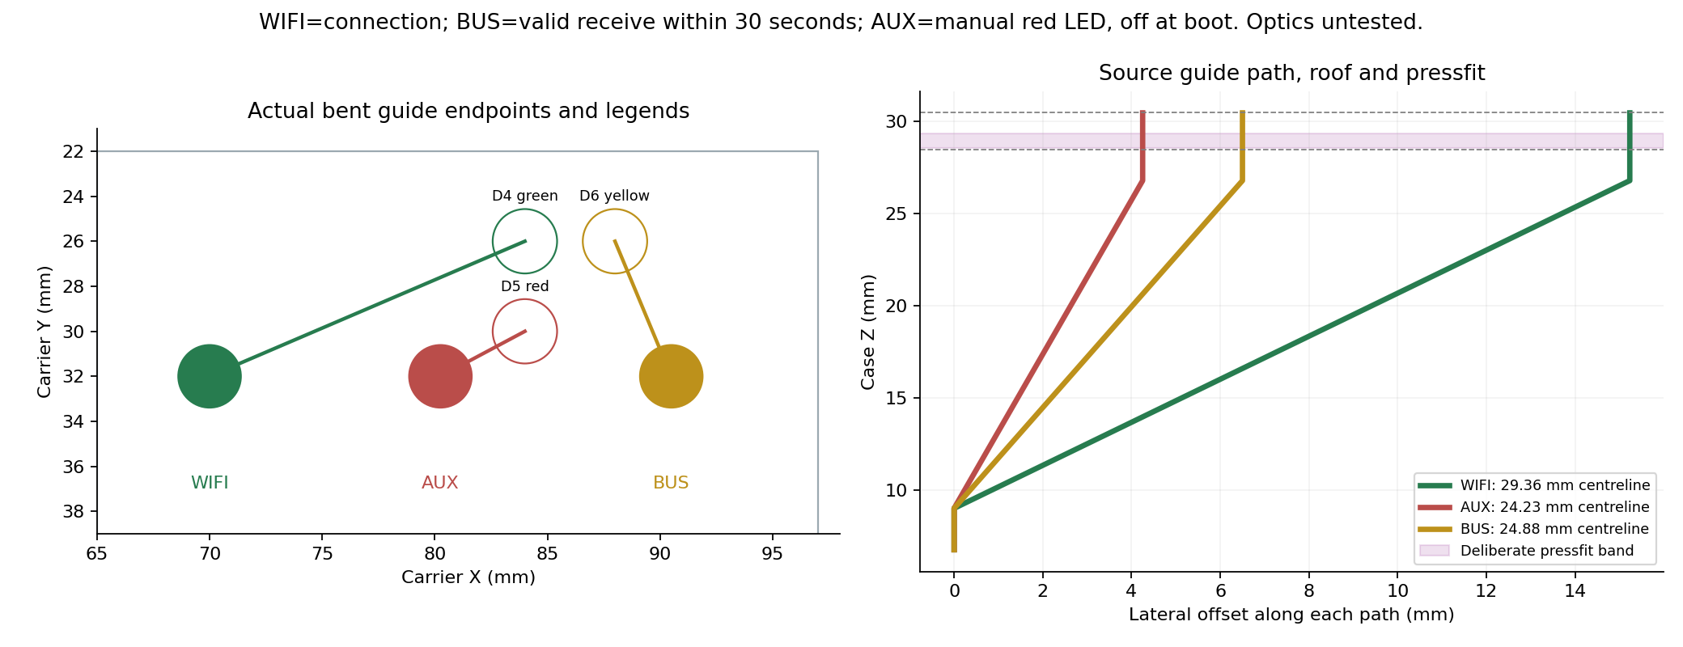
case/rev3c/analytical/review/actual-light-guide-paths.png
