Dr-Crow/esphome-ge-laundry-uart/case/rev3c/analytical/review/source_bound_c3_proxy_assembly.png

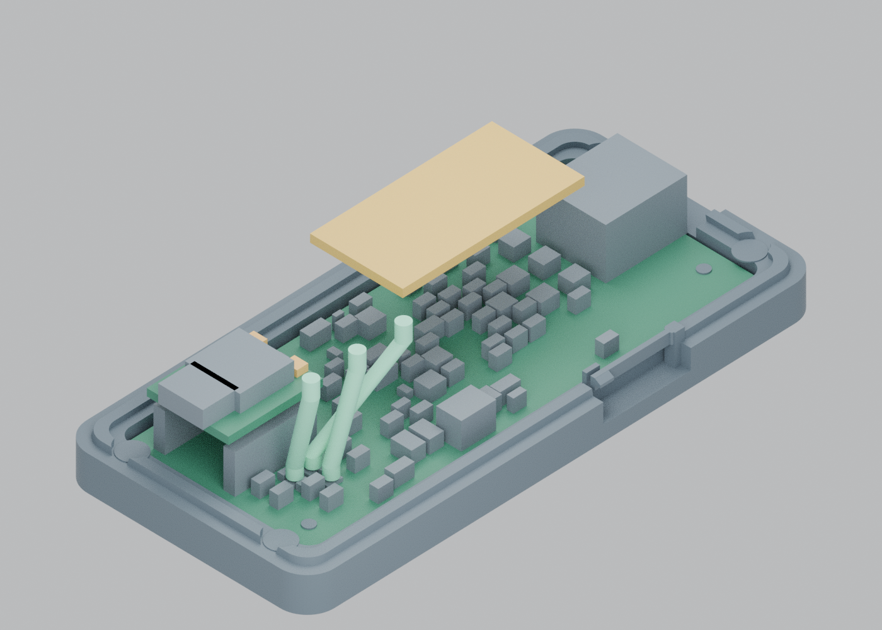
case/rev3c/analytical/review/source_bound_c3_proxy_assembly.png
