Dr-Crow/esphome-ge-laundry-uart/pcb/rev3/review/assembly-top.png

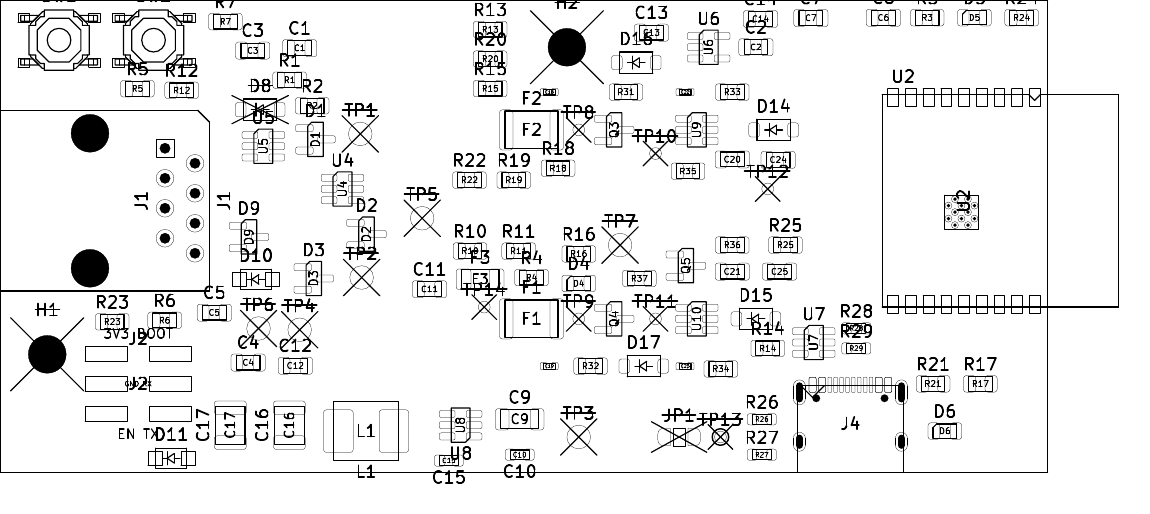
pcb/rev3/review/assembly-top.png
