Dr-Crow/esphome-ge-laundry-uart/pcb/rev3a/validation/README.md

# Revision 3A current validation package

The authoritative editable source is [design](../design/). The selected protection backport is documented in [RATED-PROTECTION.md](../RATED-PROTECTION.md) with [integrated power/reset qualifications](../POWER-QUALIFICATION.md). The current [manifest](rated-protection-manifest.json) binds source, local libraries/models, native reports, BOM/CPL, copper/drill archive and actual review assets. Earlier NATIVE-REVIEW/CLEARANCE-REPAIR/native-kicad9 manifests describe frozen d1769b25 and remain historical evidence.

Genuine KiCad9.0.9, all severities including exclusions:ERC0 errors/0 warnings; standard and expanded all-track DRC0 errors/0 warnings/0 unconnected/0 parity. No new exclusions or relaxed routing thresholds are used. Original global/Power0.25/Switching0.30/project severities/grid stay; the explicit0.20 mm exception covers only intrinsic same-U9 or same-U10 pad pairs.

- The earlier freeze recovered44 library mismatches and retained9 source-grid/name warnings. [Schematic normalization](erc-normalization/README.md) now resolves those9 through the unchanged25mil grid and explicit VCC connections. All301 physical tuples/72 nets are unchanged, with native negative controls; no severity, exclusion or routing rule is relaxed.
-Five original DRC library mismatches at D2/C5/SW2/TP13/U2 are corrected with exact embedded footprint recovery and paired metadata. Pads, graphics, models, placement and attributes remain independently equal.
-[Source/pad/net/copper proof](rated-protection-proof.json) enumerates the authorized circuit/placement deltas and distinguishes restored UUIDs from changed physical shapes.
-[Placement anchor screen](placement-anchor-screen.json) covers all97 fitted refs. [Typed body datum proof](placement-origin-review.json) explicitly covers J1/J4/U2; supplier zero/orientation/process remains an open gate.
-[Manufacturing comparison](rated-protection-manufacturing-comparison.json) records every distributed CAM member and unchanged-payload preservation. Native BOM/CPL reference sets are exactly97,49 grouped rows/42 purchasing tuples.

Current source-generated review assets are schematic.pdf, assembly-top.pdf, assembly-bottom.pdf, board-outline.pdf, pth-drill-map.pdf, npth-drill-map.pdf; images/top.svg, bottom.svg, inner1.svg, inner2.svg and3d-top/bottom/isometric/side.png. Schematic red X on DNP/excluded items is native placement marking. Bottom copper SVG is the native layer view; assembly-bottom PDF is explicitly mirrored. Approximate STEP envelopes are not authenticated supplier CAD.

Digital passes do not qualify finished process/annuli/paste/underbody via, TP12's0.2502 mm tolerance, J4's exact1.6 mm-board solder/retention compatibility, actual supplier placement preview, pulse/reverse/sustained-overvoltage coordination, loaded nominal5V startup, both GE/USB handoffs, current/inrush/retry, EN/reset programming, integrated LDO temperature, RF/USB/return paths or case fit. Preserve both input specifications and original priority while those tests are performed on real prototypes.

The exact shell-land correction is [j4-manufacturer-land-correction.json](j4-manufacturer-land-correction.json), with the unchanged USB mouth, source identity and0.18mm rule-selector rebind. The three retained CC1 segment changes are [j4-cc1-clearance-correction.json](j4-cc1-clearance-correction.json). [Current process measurements](rated-protection-process-margins.json) use the final PCB hash; [full native fill polygons](rated-protection-fill-delta.json) quantify nonlocal propagation. [Native placement](native-placement.csv) preserves the original export anchors separately from the explicit supplier body-centroid CPL.
