Dr-Crow/esphome-ge-laundry-uart/pcb/rev3c/validation/PLACEMENT-DATUM-REVIEW.md

# Reviewed nominal body-datum export

J1’s CPL X/Y change from the native pin-1 anchor (13.970,−12.550) to the reviewed EVERCOM nominal body centre (8.645,−16.995) mm. Rotation remains the native−90°. All other83-reference CPL rows, CAD, copper, BOM and Gerber/drill bytes remain unchanged.

The source-bound proof and separately hashed authored manufacturer capture identify the exact local/export transform. The nominal family body differs from both inherited Fab and pad-bounds centres. Actual supplier-library zero/pin1/orientation, full material/plating suffix and THT process still require review; this is not assembly approval. Frozen earlier quote/CPL snapshots remain historical.
