Dr-Crow/esphome-ge-laundry-uart/pcb/rev3a/validation/independent-final-review/REVIEW.md

# Independent final Rev3A review

The separate read-only reviewer reproduced the frozen source and exact distributed export hashes. Genuine KiCad9.0.9 all-severity ERC has0 errors/9 exact classified warnings, and expanded all-track DRC has0 errors/0 warnings/0 unconnected/0 parity. All301 ref/pin memberships, selected control/part assertions, exact historical symbol/instance recovery, original project/layers/setup, body/pin datums and the authorized J4 shell/CC1 deltas pass. Case26 and firmware3 files are byte-exact to the frozen base.

Fresh native BOM is byte-identical:97 fitted refs,49 rows,42 purchasing tuples. Explicit J1/U2 body-coordinate transforms reproduce CPL; J4 remains centred. Every one of the14 distributed CAM members matches a fresh native export after only creation-time normalization. Current native source dependencies, part/interface/copper/zone deltas and model resolution are checked in the accompanying JSON reports.

The reviewer inspected actual pixels for all four copper SVG views, four source-bound3D views, the schematic, top/bottom assembly, outline and PTH/NPTH drill-map PDFs. No visible source/export geometry defect was found. Direct native Gerber Viewer ZIP inspection remains limited: its file dialog opened, but both read-only path input attempts returned OSerror11(resource unavailable). The retry was bounded and the stalled dialog cancelled. No recovered native ZIP screenshot or completed direct-ZIP visual pass is claimed. Exact CAM reproduction and source-bound plot inspection are distinct evidence.

The digital review does not establish supplier zero/orientation/pick/reel or assembly qualification, J4 recessed-leg solder delivery/retention, finished-hole/mask/stencil/underbody-via/TP12 tolerances, whole-source/transient/reverse/sustained-overvoltage coordination, loaded5V startup, CL/retry/EN/reset behavior, integrated LDO temperature, RF/USB/ground returns or case fit. The nine original warning dispositions remain explicit. No physical test, order, publication or part substitution occurred.
