Dr-Crow/esphome-ge-laundry-uart/pcb/rev3a/validation/placement-body-review/U2-REVIEW.md

# U2 exact body datum and pin-1 screen

Exact fitted part is Espressif ESP32-C3-WROOM-02-N4/C2934560, the antenna-equipped WROOM-02 rather than WROOM-02U. Primary v1.7 drawing Fig10-1 page35 gives18±.15 ×20±.15 mm PCB/body dimensions and3.2±.15 mm height; Fig11-1 page38 gives the recommended signal lands1.5×.9 mm,1.5 mm pitch,17.5 mm row-center span and pad1 center7.1 mm below the antenna end.

The unchanged embedded Fab is local x[-9,9],y[-13.1,6.9], so full-body center(0,-3.1). The native footprint origin at(81.6,17),rotation−90° is the midpoint between the pad rows at their fifth-pad height. Its intended full-module center is PCB(84.7,17),CPL(84.7,-17); native CPL remains(81.6,-17),3.1 mm left of that body center. Native actual full-body bounds are x74.7..94.7,y8..26. The6 mm antenna spans x88.7..94.7 beyond the board's88.7 mm edge; existing RF exclusion extends x88.7..99.7,y3..31.

Pad1 local(-8.75,-6) is.25 mm inset from nominal body side and7.1 mm below nominal antenna end. Native rotation maps it toPCB(87.6,8.25),net+3V3, and CPL(87.6,-8.25). Relative to the intended geometric body center, the CPL pin1 vector is(+2.9,+8.75). This is an exact drawing/Fab/pad transform agreement; the printed pin1 and18 numbering on the top-view recommended land pattern fixes handedness.

The native footprint/CPL origin cannot automatically be called a geometric component center. A supplier's placement-library origin, packagezero rotation, pin1, pick datum and reel orientation must be matched to these typed facts before assembly placement approval. No source/CPL correction was made or inferred solely from body bounds. The source preserves the original intended body/terminal datum, rather than establishing JLC's library transform.

Primary URL https://documentation.espressif.com/esp32-c3-wroom-02_datasheet_en.pdf . PDF/pixel hashes, all coordinate conventions and native exact pads are recorded in typed-facts.json and native-geometry.json. The current requested source hash is recorded; geometry was read from unchanged frozen original to avoid a live-source race and will be checked again at final freeze.

JLC's primary [Pick & Place contract](https://jlcpcb.com/help/article/pick-place-file-for-pcb-assembly), updatedSeptember9,2026 and inspectedOctober4, defines MidX/MidY as the component centroid in millimetres, with counterclockwise positive rotation. Its generic KiCad export guide recommends renaming the native headers; that does not independently resolve this noncentral footprint origin. Direct native .pos/CSV coordinate equality must therefore not be labelled supplier-centroid or physical-placement verification. The body/pin1 facts support an explicit documented transform, while actual supplier library/pick/reel equivalence remains to be checked.
