Dr-Crow/esphome-ge-laundry-uart/pcb/rev3a/validation/sunmate-land-review/SUNMATE-LAND-REVIEW.md

# Exact SUNMATE SMF16A contact drawing review

Reviewed actual manufacturer-authored drawing pixels, page1 of `sunmate-smf16a.pdf`, for retained D18 and added D19, exact SUNMATE SMF16A/C399290. Primary supplier-file provenance is `https://jlcpcb.com/api/file/downloadByFileSystemAccessId/8757789523080564736`. PDF SHA-256 is `7b825d053f2797dcfd6efd8a268f79365b147bc57f7dc42c6da31fedab743e2b`. The complete page and the package-detail crop were rendered afresh and inspected. Pixel hashes are in `sunmate-land-review.json`.

The manufacturer calls this package **SOD-123FL**; the PCB uses **Diode_SMD:D_SOD-123F**. These distinct names have been preserved. They are not used to infer package equality, a supplier-recommended land pattern or assembly approval.

The actual drawing gives overall lead span A3.58-3.72mm; body length B2.72-2.78mm; body width C1.77-1.83mm; body height D1.02-1.08mm; bottom terminal length L0.53-0.57mm; terminal thickness H0.13-0.17mm. The terminal-width E row visibly prints **minimum0.097mm**, typical1.00mm and maximum1.03mm. This apparent discrepancy is retained exactly. It is not silently corrected to0.97mm or used as an authenticated alternate terminal size. Clarification belongs to the supplier/assembler qualification.

Both actual initial native footprints have 1.1x1.1mm copper/mask/paste rounded pads, centres +/-1.4mm along their local length axis and 0.25mm copper corner radius. Pad1 is cathode/source PROTECTED, pad2 anode/GND. Both D18 and D19 are rotated -90 degrees in the initial PCB, with their pad-relative geometry identical. Their centred local terminal/land relationship can therefore be reviewed before the final footprint positions freeze.

For the positive terminal, the pad bounding rectangle is x0.85..1.95mm /y+/-0.55mm. The manufacturer's independent-dimension terminal envelope has outer x1.79..1.86mm; inner x1.22..1.33mm; maximum y+/-0.515mm. Rectangle projections leave at least0.37mm inner,0.09mm outer and0.035mm side pad extensions. The pad inner gap is1.70mm versus terminal inner gap2.44..2.66mm. The negative terminal is symmetric. Package/body envelopes fit within the existing +/-2.20 by+/-1.15mm courtyard when centred; this statement is a drawing envelope check, not a solder/placement clearance certification.

The rounded copper clips a small portion of maximum terminal corners, so **full terminal containment is not claimed**. With A3.72mm, L0.53mm and E1.03mm, the positive terminal spans x1.33..1.86mm with area0.5459mm2. Integrating the actual0.25mm corner circle gives0.000700974mm2 of terminal rectangle outside the copper and0.545199026mm2 contact overlap, approximately**99.8716%**. Maximum width controls these corner losses; the printed ambiguous minimum is not needed to obtain this maximum-envelope result. The mirrored terminal gives the same centred calculation.

This is a zero-placement-offset contact screening calculation based on the simplified rectangular terminal drawing. It excludes rotation/translation tolerance, body/terminal coplanarity and shape details, fabrication/mask registration, solder-paste/reflow behavior, allowable fillets, actual part inspection, thermal/case clearance and reliability. No authenticated manufacturer-recommended land drawing was present on these pages. Actual supplier/assembler approval, placement tolerance and solder-process/thermal qualification remain gates. There is no observed loss of terminal contact in the centred native pattern, and no authority here to replace either footprint merely because of the naming distinction. A final source freeze will be checked for unchanged actual land geometry and for placement/adjacent-object errors.

The same exact datasheet page2 gives SMF16A marking LP, stand-off16V, breakdown17.8-19.7V at1mA, clamp26.0V at7.7A and leakage1uA at VRWM. Page1/page3 retain the 10/1000us/25C pulse and derating context. These electrical rows do not close source-energy, temperature, overshoot, repetition or sustained-DC qualification, and the downstream TPS does not limit this upstream TVS current.
