Dr-Crow/esphome-ge-laundry-uart/pcb/rev1.0/validation/erc-normalization/README.md

# Rev1.0 explicit VCC presentation candidate

Candidate `51effc2fc3adfa5acbbe1469120566866044a9ad` in `/workspace/shared/ge-oct4-rev1-erc-normalize` applies only the schematic and its project-local symbol definition to source `2088c3acbe2766541cf4b2daa4a5f45e6ed5e4da`. It exposes original buffer power pin U1.5 VCC and attaches the existing +5V symbols through short right-angle annotation leads in both units. The common GND pin is untouched. No replacement part, physical pin rename, or rule/grid/exclusion change is introduced.

Genuine KiCad 9.0.9 regenerated before/after native netlists and all-severity ERC plus all-track DRC/schematic parity. The candidate has zero errors, warnings, unconnected and parity items. All 166 physical `(ref,pin,net,pinfunction,pintype)` tuples and 58 net names/codes/classes match exactly; full component/library pin metadata match. All 159 other tracked input files are byte-identical. PCB geometry remains 61 footprints,174 pads,351 routes,26 vias. A native-export detached source fixture moving U1.5 to +3V3 is correctly rejected with the same pin count.

All nine current Gerber and two drill payloads were freshly exported from the unchanged PCB and match after only generation-date/checksum normalization. Both current and historical archives are byte-preserved. `after-schematic.pdf`, its full render and both U1 crops were actually inspected and are clear. `proof.json`, `presentation-delta.json`, `candidate-manifest.json` and `integration-updates.json` carry source-bound evidence and the exact integration updates still needed. The clone has only the two source changes committed; existing older review exports have deliberately not been overwritten in this isolated source candidate.

No publication, integration, procurement, orders, firmware changes or physical-hardware tests were performed. Original electrical/module, supplier, physical, thermal, historical CAM and appliance qualification gates remain open. This is not a manufacturing release.
