Dr-Crow/esphome-ge-laundry-uart/pcb/rev1.0/validation/NATIVE-REVIEW.md

# Current Rev1 schematic review

The earlier review below is frozen to its original cleanup input. Current
explicit VCC presentation resolves the one alias; fresh native ERC/DRC/unconnected/
parity findings are zero. Source-bound proof in erc-normalization/proof.json
records 166 physical memberships/58 nets, native detached-fixture controls and
unchanged PCB/CAM/firmware. Ratings, module/buck identity, procurement and physical
qualification remain open.

## Frozen prior review

# Rev1 native source review

October 3, 2026, genuine KiCad 9.0.9. The cleaned historical source has **zero ERC errors, one retained ERC alias warning, zero DRC findings, zero unconnected items and zero schematic parity findings**. This is a source and export review; appliance compatibility, electrical protection and manufacturing release remain unqualified.

## Source and bounded changes

The exact restored source was public commit `87984047ee029efb83bf9947dc21818fd18e39b3`, recorded in [restoration provenance](../design/RESTORED-PROVENANCE.json). That record describes the original input bytes. The current edited source is independently bound by [preservation proof](native-kicad-9.0.9/preservation-proof.json) and [artifact manifest](native-kicad-9.0.9/manifest.json).

- The inherited 59 parity messages were 39 autogenerated net-name substitutions. The previously reviewed [net-name correction](../design/NET-NAME-CORRECTION.json) is retained. All 166 original electrical `(reference, pin)` memberships and every connected-pin group are unchanged.
- All 21 embedded symbol definitions are recovered into [LegacySymbols](../design/symbols/LegacySymbols.kicad_sym). Pin names, numbers, types and geometry are exact; only library namespaces changed. Three excluded PWR_FLAG symbols model the actual external VDC source, J1's external buck +5V output and shared return. They add no physical parts and establish no voltage/current guarantee. The classic development-board symbol already models +3V3 as its power output; that original definition is preserved.
- All 61 embedded footprints are recovered into a project-local library, rather than replaced with current stock geometry. [Footprint mapping](../design/footprints/source-map.json) retains original IDs. Native comparison proves all 61 positions/orientations, 174 native pad geometry/net/layer/drill records, and 377 track/via records unchanged. Two RJ45 NPTH pads explicitly spell their original F.Cu/B.Cu/F.Mask/B.Mask set to avoid native 9's wildcard expansion onto absent internal layers.
- Original conductor endpoints, junctions, labels, no-connects and symbol anchors are on a 25 mil (0.635 mm) grid: all 572 coordinates pass. Setting the missing project connection-grid metadata to 25 mil removes the inherited 226 off-grid warnings without moving any node. Every original project rule, severity, exclusion, class and assignment is retained.
- J2's two crossing silk endpoints are clipped from x136.98 to x134.8 mm inside the x135 mm board edge; two vertical silk segments wholly outside the board are removed. Copper, holes, courtyard, fab outline, connector placement and all printed text remain unchanged. This removes the two original silk-edge findings.

## Native results and retained warning

[Full ERC](native-kicad-9.0.9/erc.json) retains the original `multiple_net_names` warning: hidden U1 VCC and +5V name the same connection. The native canonical net remains +5V. It is visible and unexcluded; source pin names are not renamed to erase this intentional alias.

[Full DRC with all-track reporting and schematic parity](native-kicad-9.0.9/drc-all-track-errors.json) has zero findings. Existing historical rules have not been increased, lowered or presented as current factory qualification. An ERC command using all severities and `--exit-code-violations` still fails on the visible warning.

## Paired review exports and original package

The [current schematic](schematic.pdf), native [front](views/front.png) and [back](views/back.png) views, two [copper plots](copper/), [front board PDF](board-front.pdf), and [PTH/NPTH drill maps](../review-manufacturing/) were regenerated from this source. Actual pixels were inspected. These are 2D source views; the generic ESP32 development board and external buck are not authenticated purchased-part 3D models.

[Current review CAM](../review-manufacturing/REVIEW-CAM-OnionStraws-rev1.0.zip) contains nine Gerber layers, two drill files and the native job. The empty backside paste layer is explicit. There is no supplier BOM or CPL: the original package had neither, and no supplier selections were invented. Drill-map PDFs remain beside the archive for review.

Compared with the unedited input exported through the same KiCad 9.0.9 settings, both copper layers, both masks, both paste layers, backside silk and both drill payloads are identical after generation-date/checksum normalization. Edge.Cuts retains exactly the same four segments with a different native serialization order. Only front silk has a physical edit. This is separate from comparison with the original KiCad 6 archive.

The [original Gerber archive](../manufacturing/GERBER-OnionStraws-rev1.0.zip) is byte-identical, SHA-256 `6a3c80fe47a93ec45a44a21d1d35d9692b3aaca6649cdf93bc7cc371a7f84d57`. Full original-source-to-original-CAM geometry parity remains unestablished; the current package is clearly separate.

An [independent read-only review](native-kicad-9.0.9/INDEPENDENT-REVIEW.md) confirms both historical cleanups against their immutable public sources; the [machine-readable receipt](native-kicad-9.0.9/independent-historical-review.json) binds exact CAD hashes and library/geometry/pin-partition results. It found no unexpected changes.

## Original architecture and open qualification

Rev1 uses a generic 38-pin classic ESP32 development-board interface, one RJ45 pin-1 supply input, F1/Q1/Q2 and an external buck-module J1. RJ45 pin 3 is unconnected. The generic symbols and original resistor/capacitor/TVS/zener/supervisor identities are preserved; no regulator or rating selection was introduced.

ESP UART assignments remain GEA2 TX GPIO18 / RX GPIO19, and GEA3 TX GPIO17 / RX GPIO16. Current C3 profiles do not apply. The separate classic-firmware work is outside this CAD change.

Original schematic notes such as the +9V to +16V input range, inrush protection and supervisor behavior are historical design claims, not measurements or qualification results. Source tolerances/current/transients, polarity and inrush behavior, TVS/zener/PMOS coordination, buck/module identity and startup, supervisor thresholds/timing, thermal behavior, physical fit and appliance/RF behavior remain open. Neither ERC flags nor a zero-error DRC grants manufacturing release or a supply envelope.
