Dr-Crow/esphome-ge-laundry-uart/pcb/rev1.0/validation/native-kicad-9.0.9/INDEPENDENT-REVIEW.md

# Independent Rev1/Rev2 bounded cleanup review

PASS. Reviewed October 3, 2026 with genuine KiCad 9.0.9. Read-only source hashes are bound in independent-historical-review.json. The immutable public source Git blobs were checked before comparison; source hashes remained unchanged during native checking and local-library verification.

Rev1 retains all 166 logical pin memberships, 174 native pad geometries/layer sets, 61 footprint placements, 351 route segments, 26 vias, mounting geometry, outline, values, original rules/netclasses and all 21 original embedded symbol definitions. All 572 original connection coordinates are unchanged on the .635mm grid. The exact changes are project-local namespaces, three non-physical VDC/+5V/GND flags, connection_grid_size25mil, two J2 silk endpoint clips to x134.8mm and two wholly off-board silk segment removals. Explicit J2 NPTH layer syntax preserves the original four native layer selections. Fresh ERC has zero errors and one +5V/VCC alias warning; fresh DRC has zero violations, zero unconnected and zero parity items with all-track/severity-all checks.

Rev2 retains all 186 logical pin memberships, 222 pads, 73 footprint placements, 636 route segments, 76 vias, mounting geometry, outline, values, original rules/netclasses and all 24 original embedded symbol definitions. The sole pad attribute change is U4.2 thermal-spoke angle90→45. Connector/module silk edits are confined to two J1 endpoint clips and one U2 off-board line and polygon removal. JP2/TP3 reference fixes are UUID-backed; H3/H4 remain DNP and change only to on_board no. Native9 refill versus the historical cached fill differs by1.6160023714mm² front and .365273824683mm² back. The thermal edit versus the retained Native9 90° control changes .575544686049mm² front localized to U4.2 (x83.0875–84.25mm, y90.139802–90.9255mm), with zero back-copper difference. Zone outlines/settings, thermal gap/width and two-spoke requirement remain unchanged. Fresh ERC has zero errors and four known alias warnings; fresh all-track/severity-all DRC has zero violations, zero unconnected and zero parity items.

Every project-local footprint was independently loaded with the native library plugin and compared against the current board pads, graphics, text fields, attributes and stroke/fill styles. All61 Rev1 and73 Rev2 local footprints match; back-side definitions were normalized through the native Flip API. Project-local symbol library definitions match embedded definitions exactly after namespace normalization. Footprint libraries omit only netlist-derived pinfunction/pintype annotations; those annotations remain preserved on the actual board.

No unexpected source, physical geometry or pin-partition change was found. This review does not establish supplier assembly rotations, source-to-original-CAM parity, purchased-module identity, physical compatibility, appliance safety, production release or bench qualification. The original independent detailed per-object comparison and fresh native reports/XML are retained in the separate historical independent review folder; this receipt binds their source and verification-script hashes.
