Dr-Crow/esphome-ge-laundry-uart/pcb/rev3a/validation/erc-normalization/u4b.png

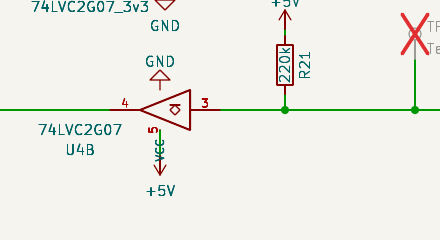
pcb/rev3a/validation/erc-normalization/u4b.png
