Dr-Crow/esphome-ge-laundry-uart/pcb/rev3a/validation/erc-normalization/usb-group.png

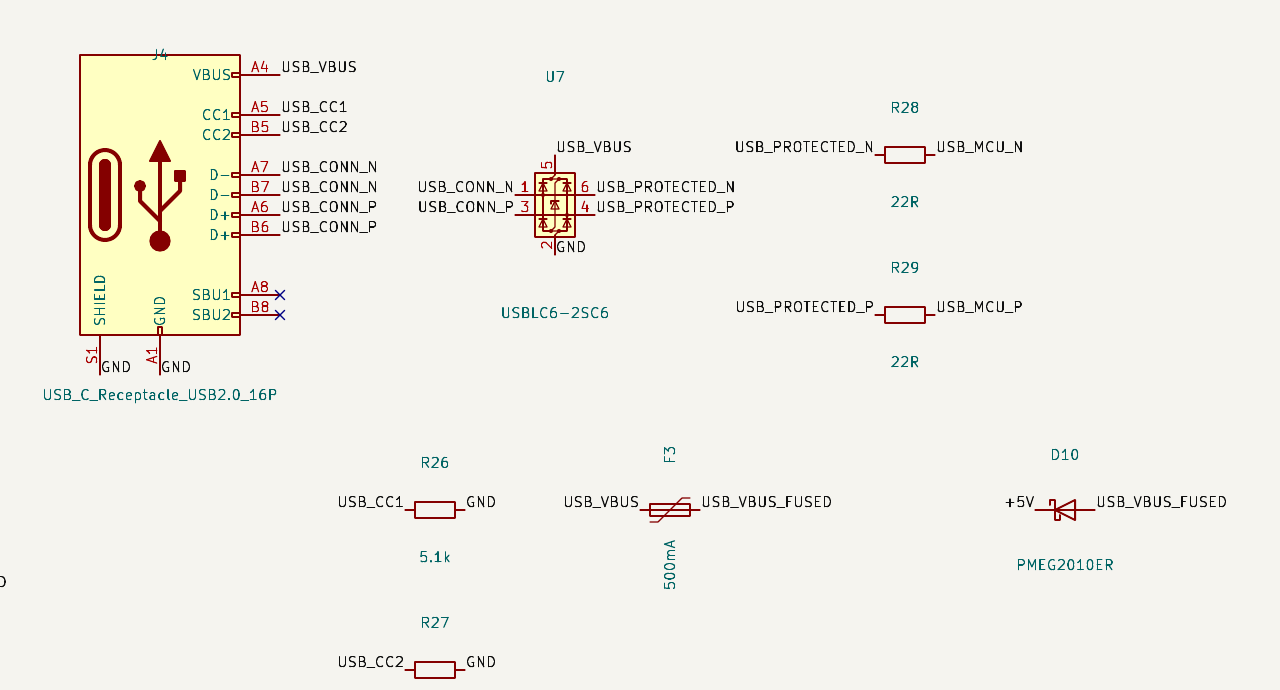
pcb/rev3a/validation/erc-normalization/usb-group.png
