Dr-Crow/esphome-ge-laundry-uart/pcb/rev3/review/schematic.pdf

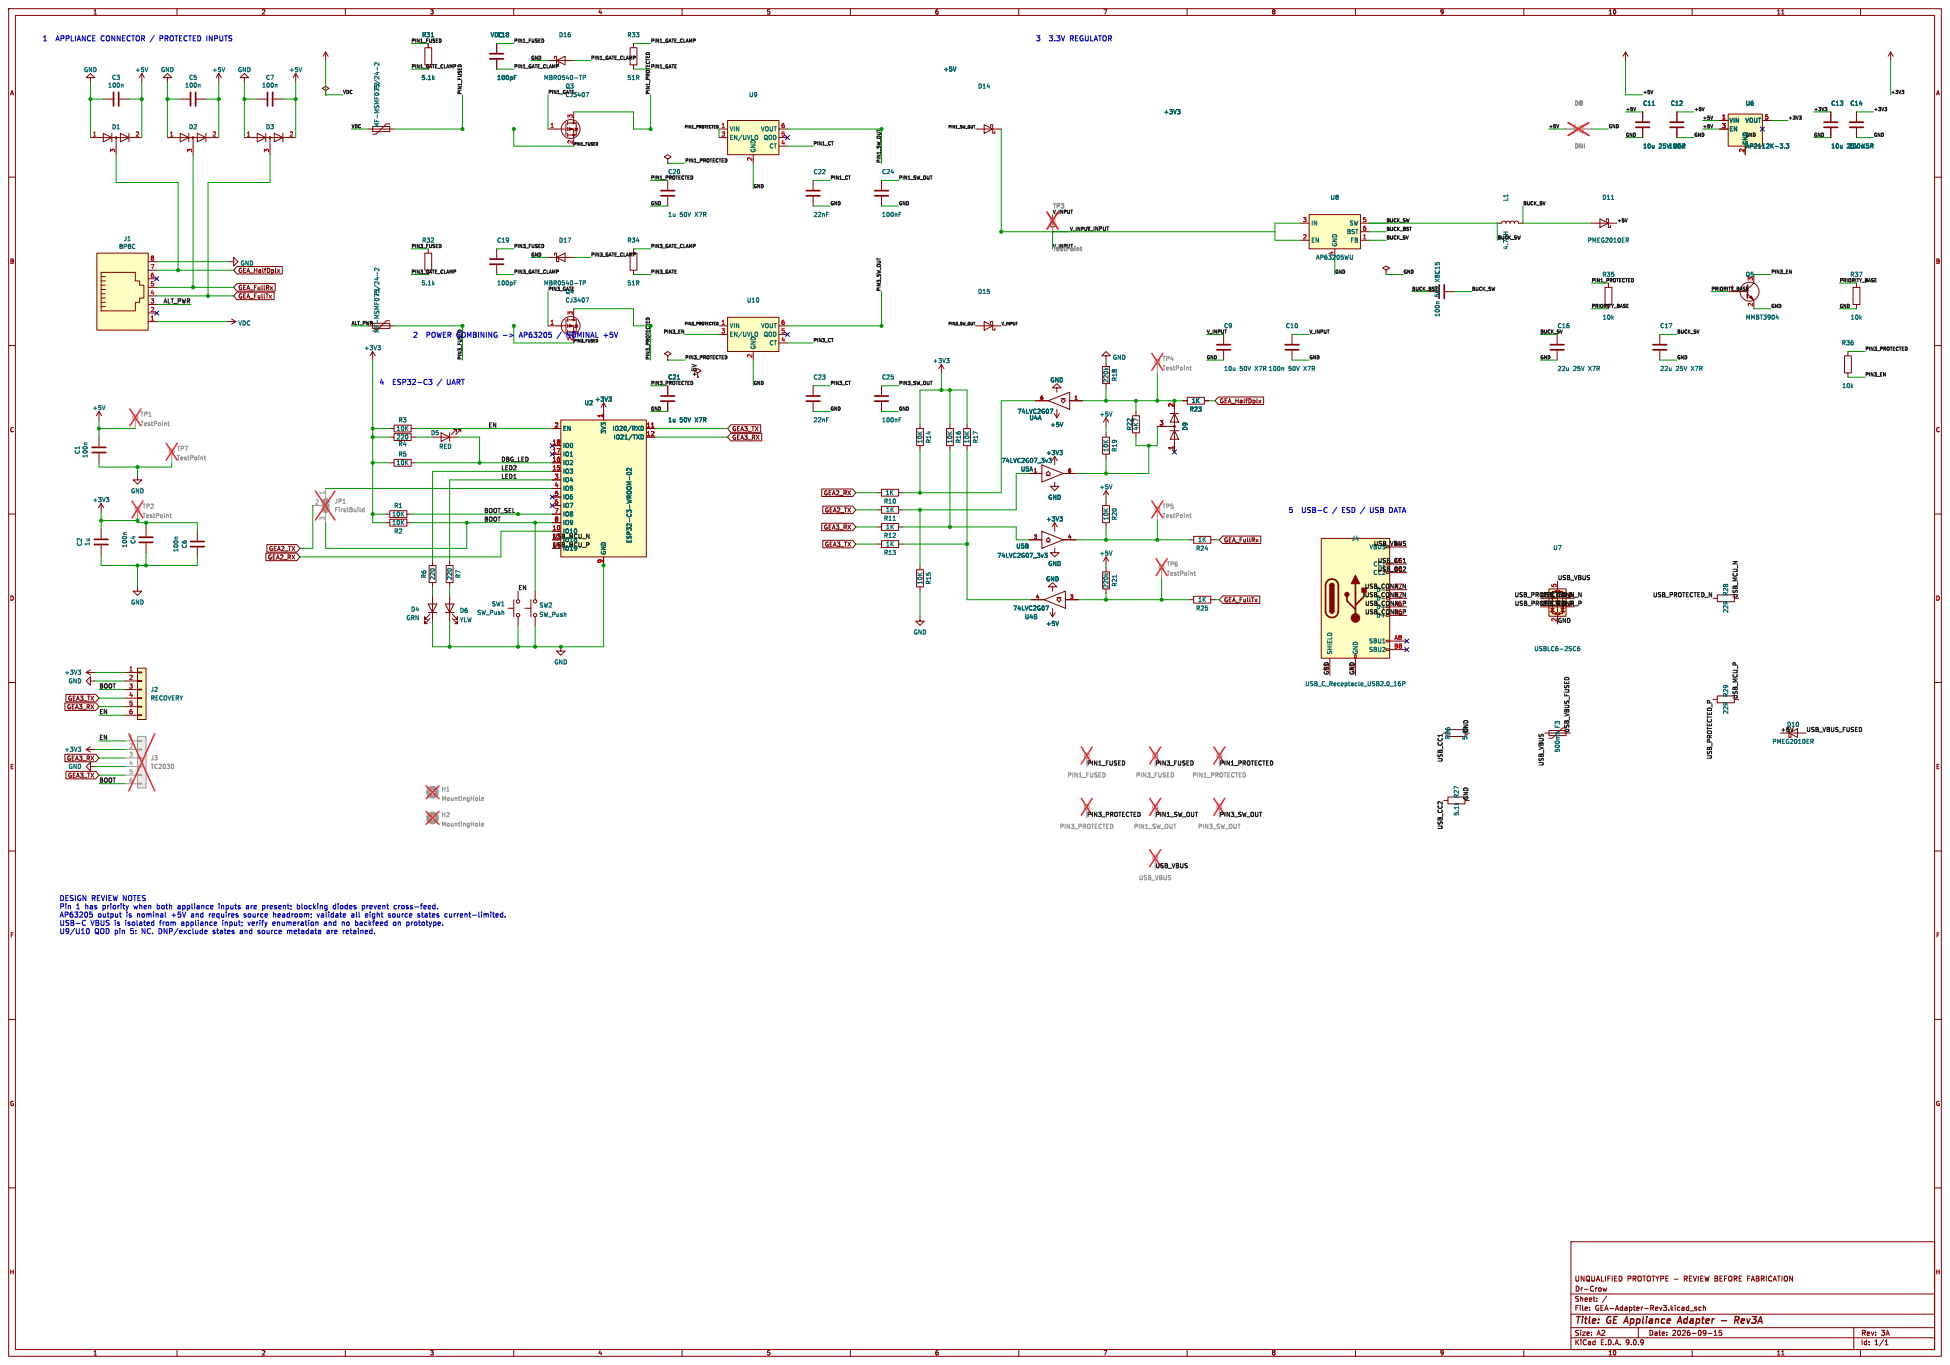
[picture p112: page 1]

3 2 Q4 CJ3407 VIN 1 EN/UVLO 3 GND

5 USB-C / ESD / USB DATA DESIGN REVIEW NOTES

File: GEA-Adapter-Rev3.kicad_sch Sheet: / Dr-Crow
