Dr-Crow/esphome-ge-laundry-uart/pcb/rev3/review/assembly-bottom.pdf

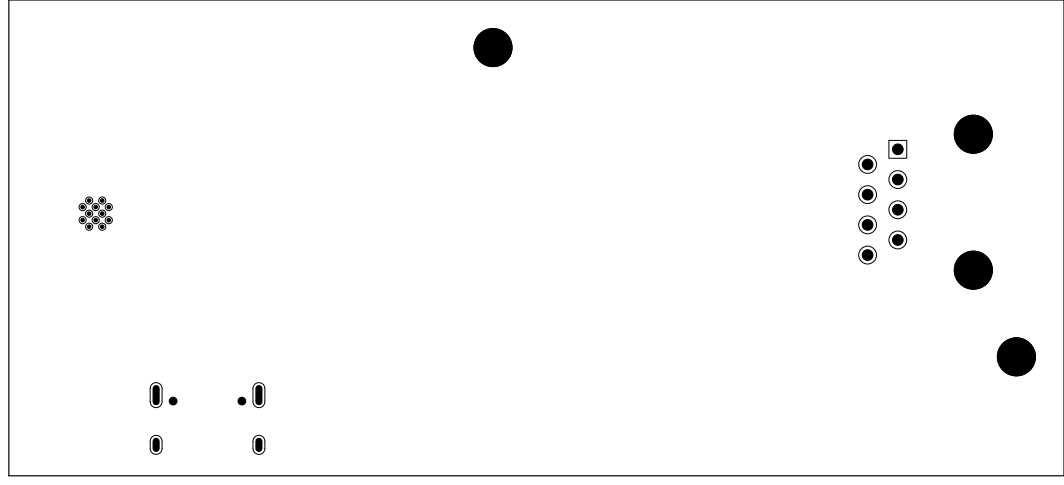
[picture p121: page 1]
