Dr-Crow/esphome-ge-laundry-uart/pcb/rev3/review/assembly-top.pdf

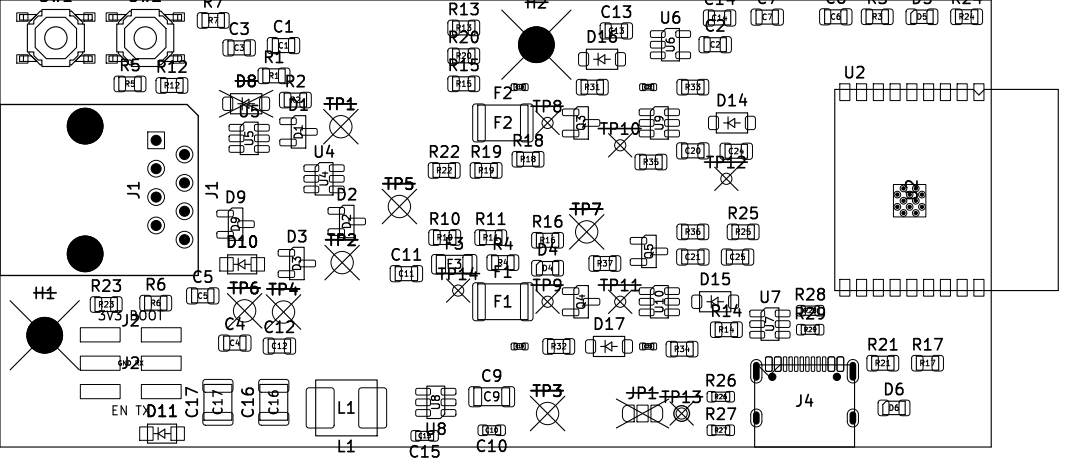
[picture p122: page 1]
