Dr-Crow/esphome-ge-laundry-uart/pcb/rev3/review/dimensions.pdf

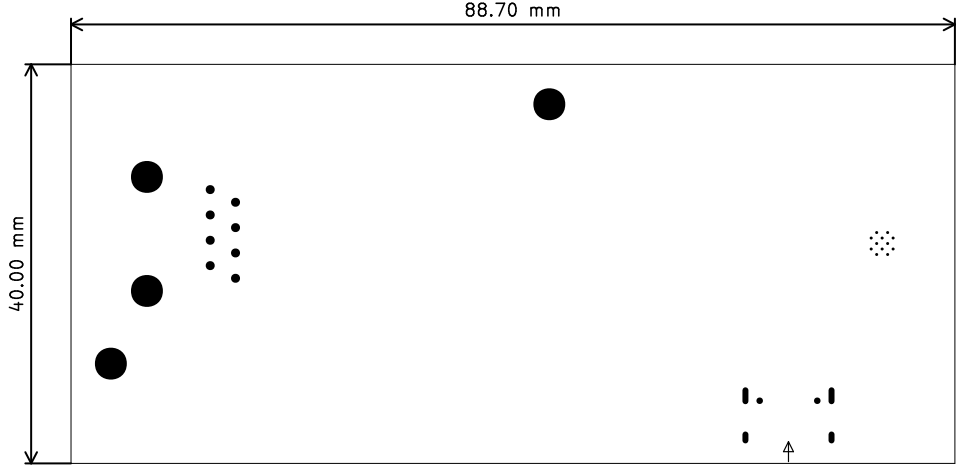
[picture p123: page 1]
