Dr-Crow/esphome-ge-laundry-uart/pcb/rev2.2/validation/schematic.pdf

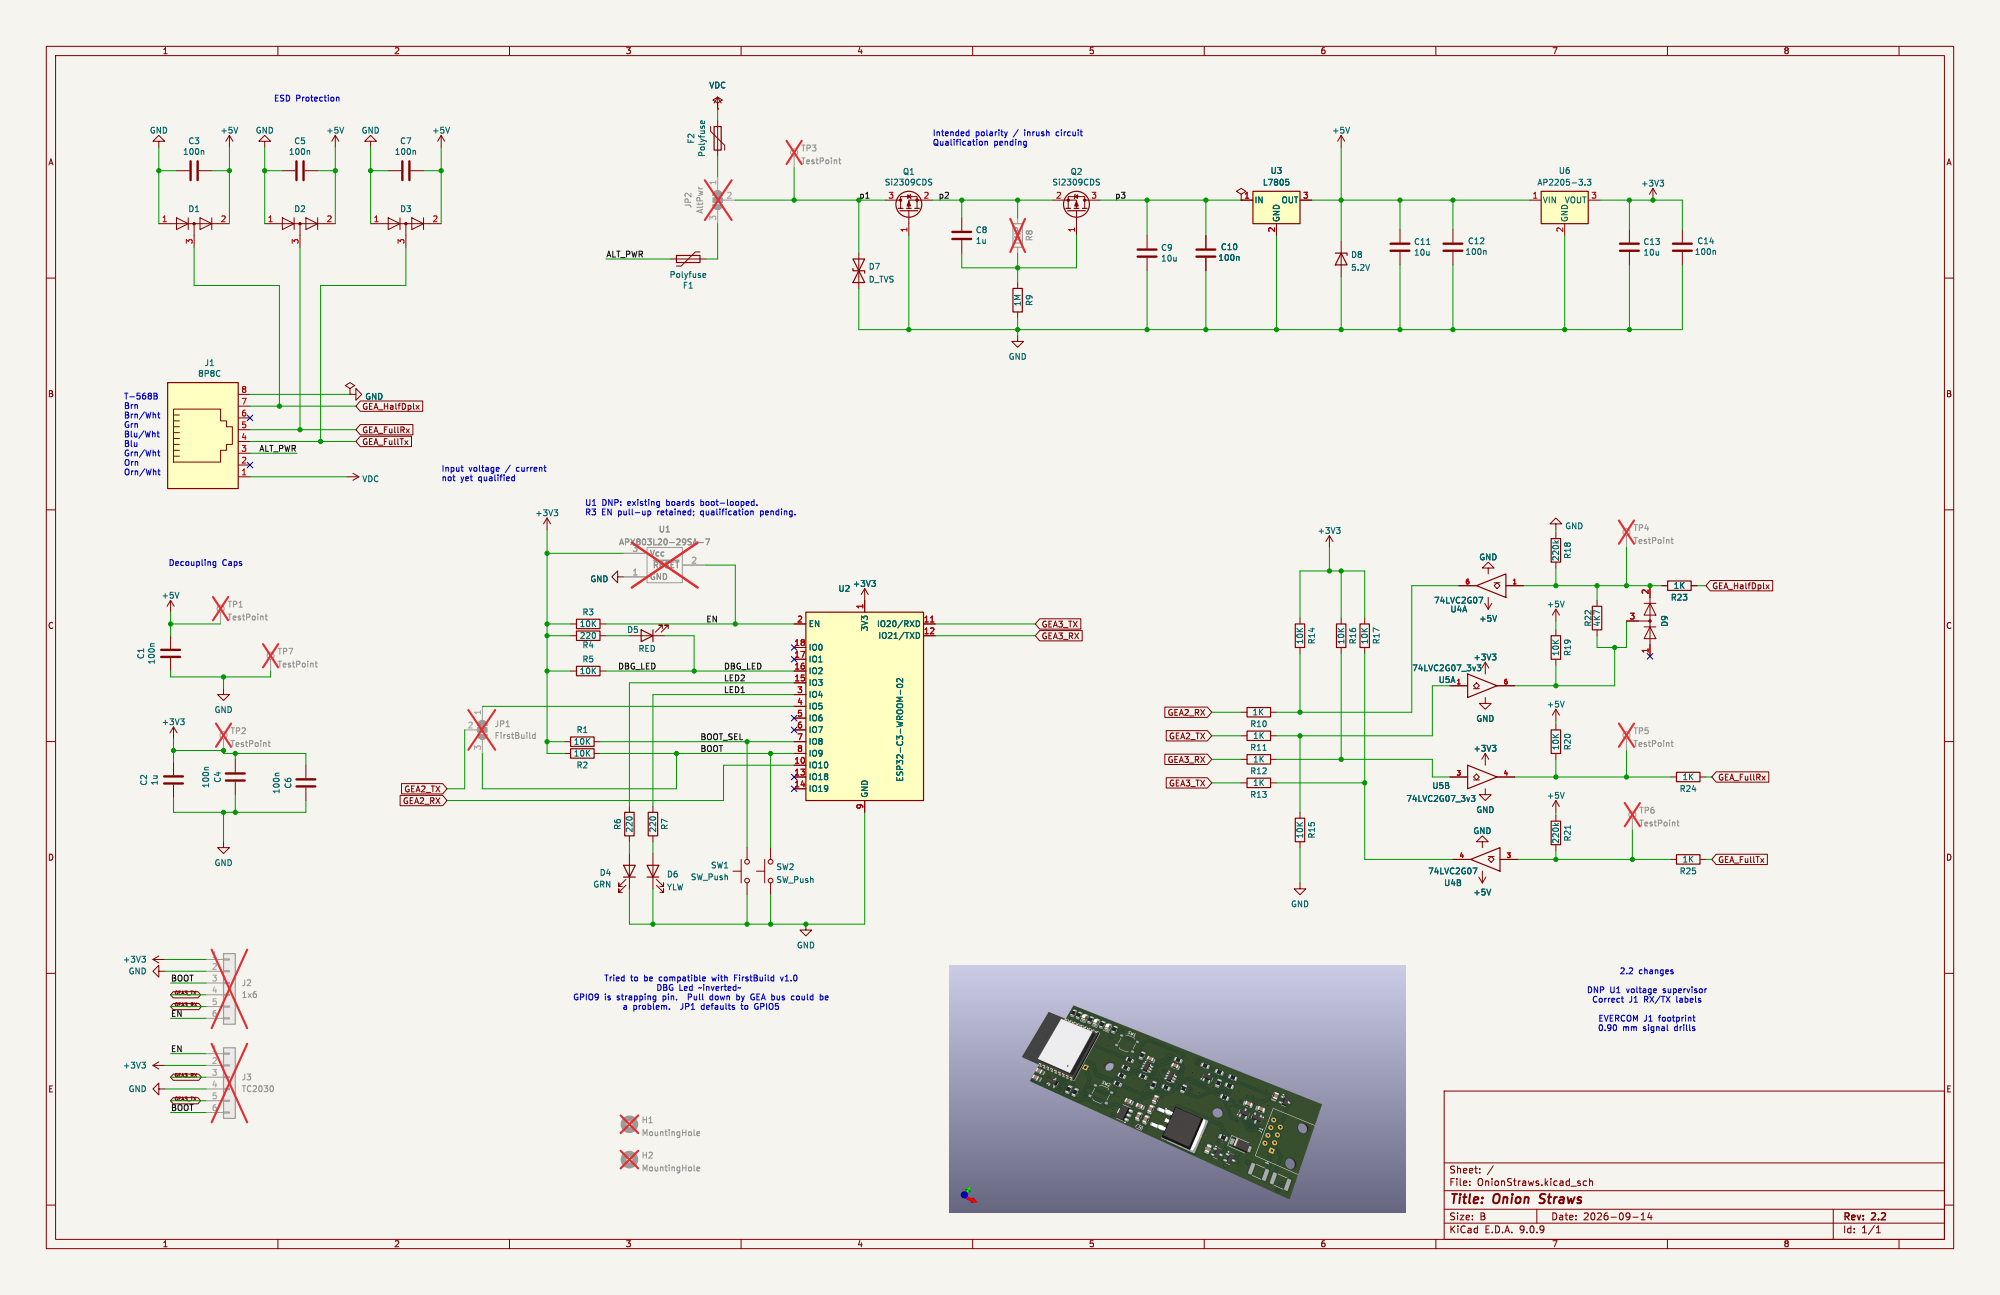
[picture p124: page 1]

ESD Protection Washer Blk NCGrn/Rd Org BLU

File: OnionStraws.kicad_sch Sheet: / GND

2.2 changes DNP U1 voltage supervisor Correct J1 RX/TX labels EVERCOM J1 footprint 0.90 mm signal drills

Id: 1/1 Title: Onion Straws
