Dr-Crow/esphome-ge-laundry-uart/pcb/rev2.0/native-review/schematic.pdf

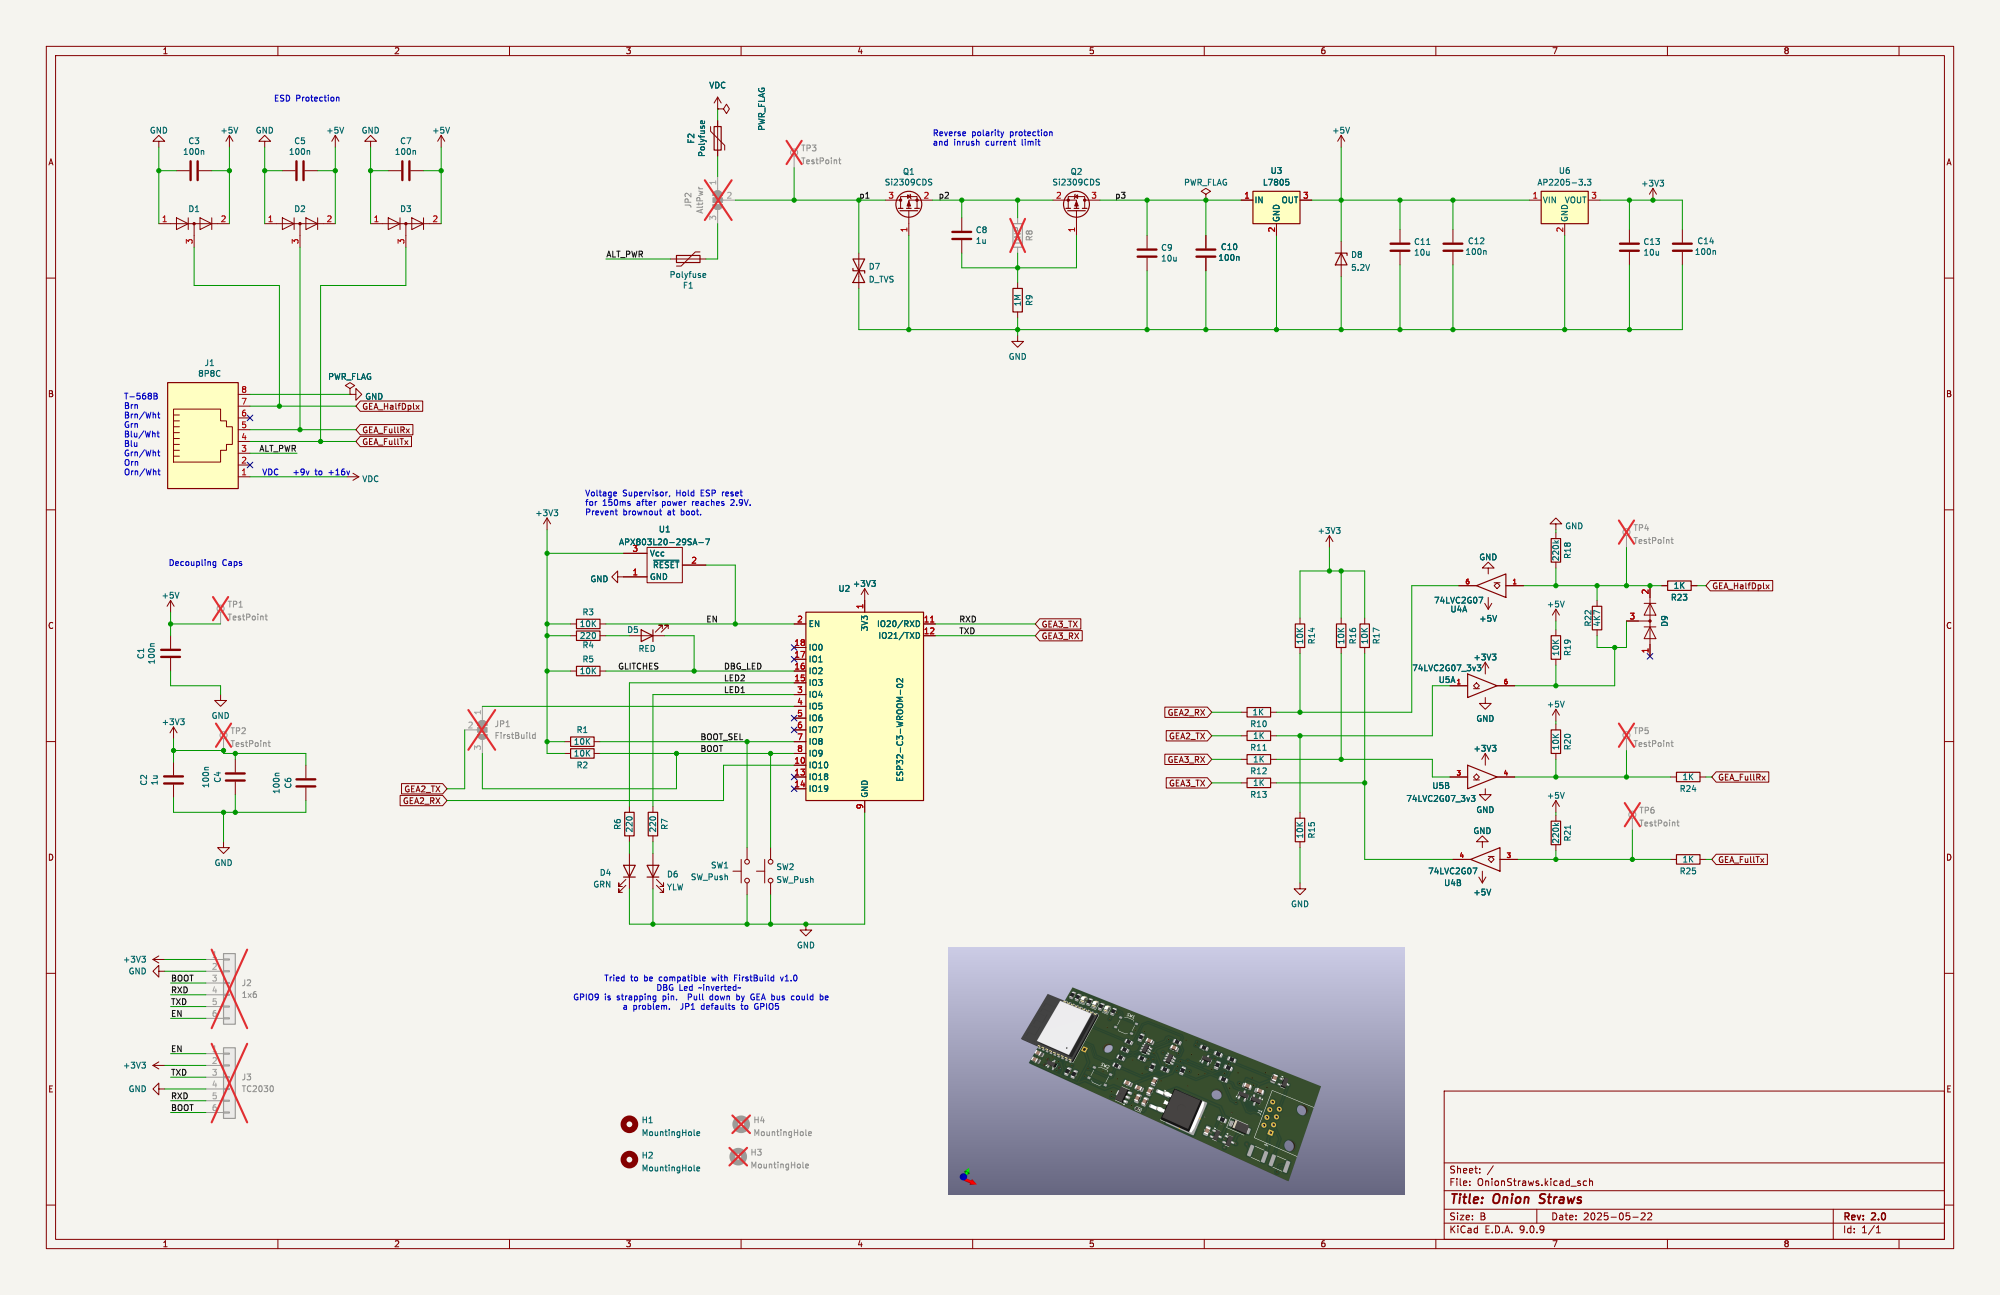
[picture p125: page 1]

and inrush current limit

File: OnionStraws.kicad_sch Sheet: /
Id: 1/1 Title: Onion Straws
