Dr-Crow/esphome-ge-laundry-uart/pcb/rev2.1/validation/schematic.pdf

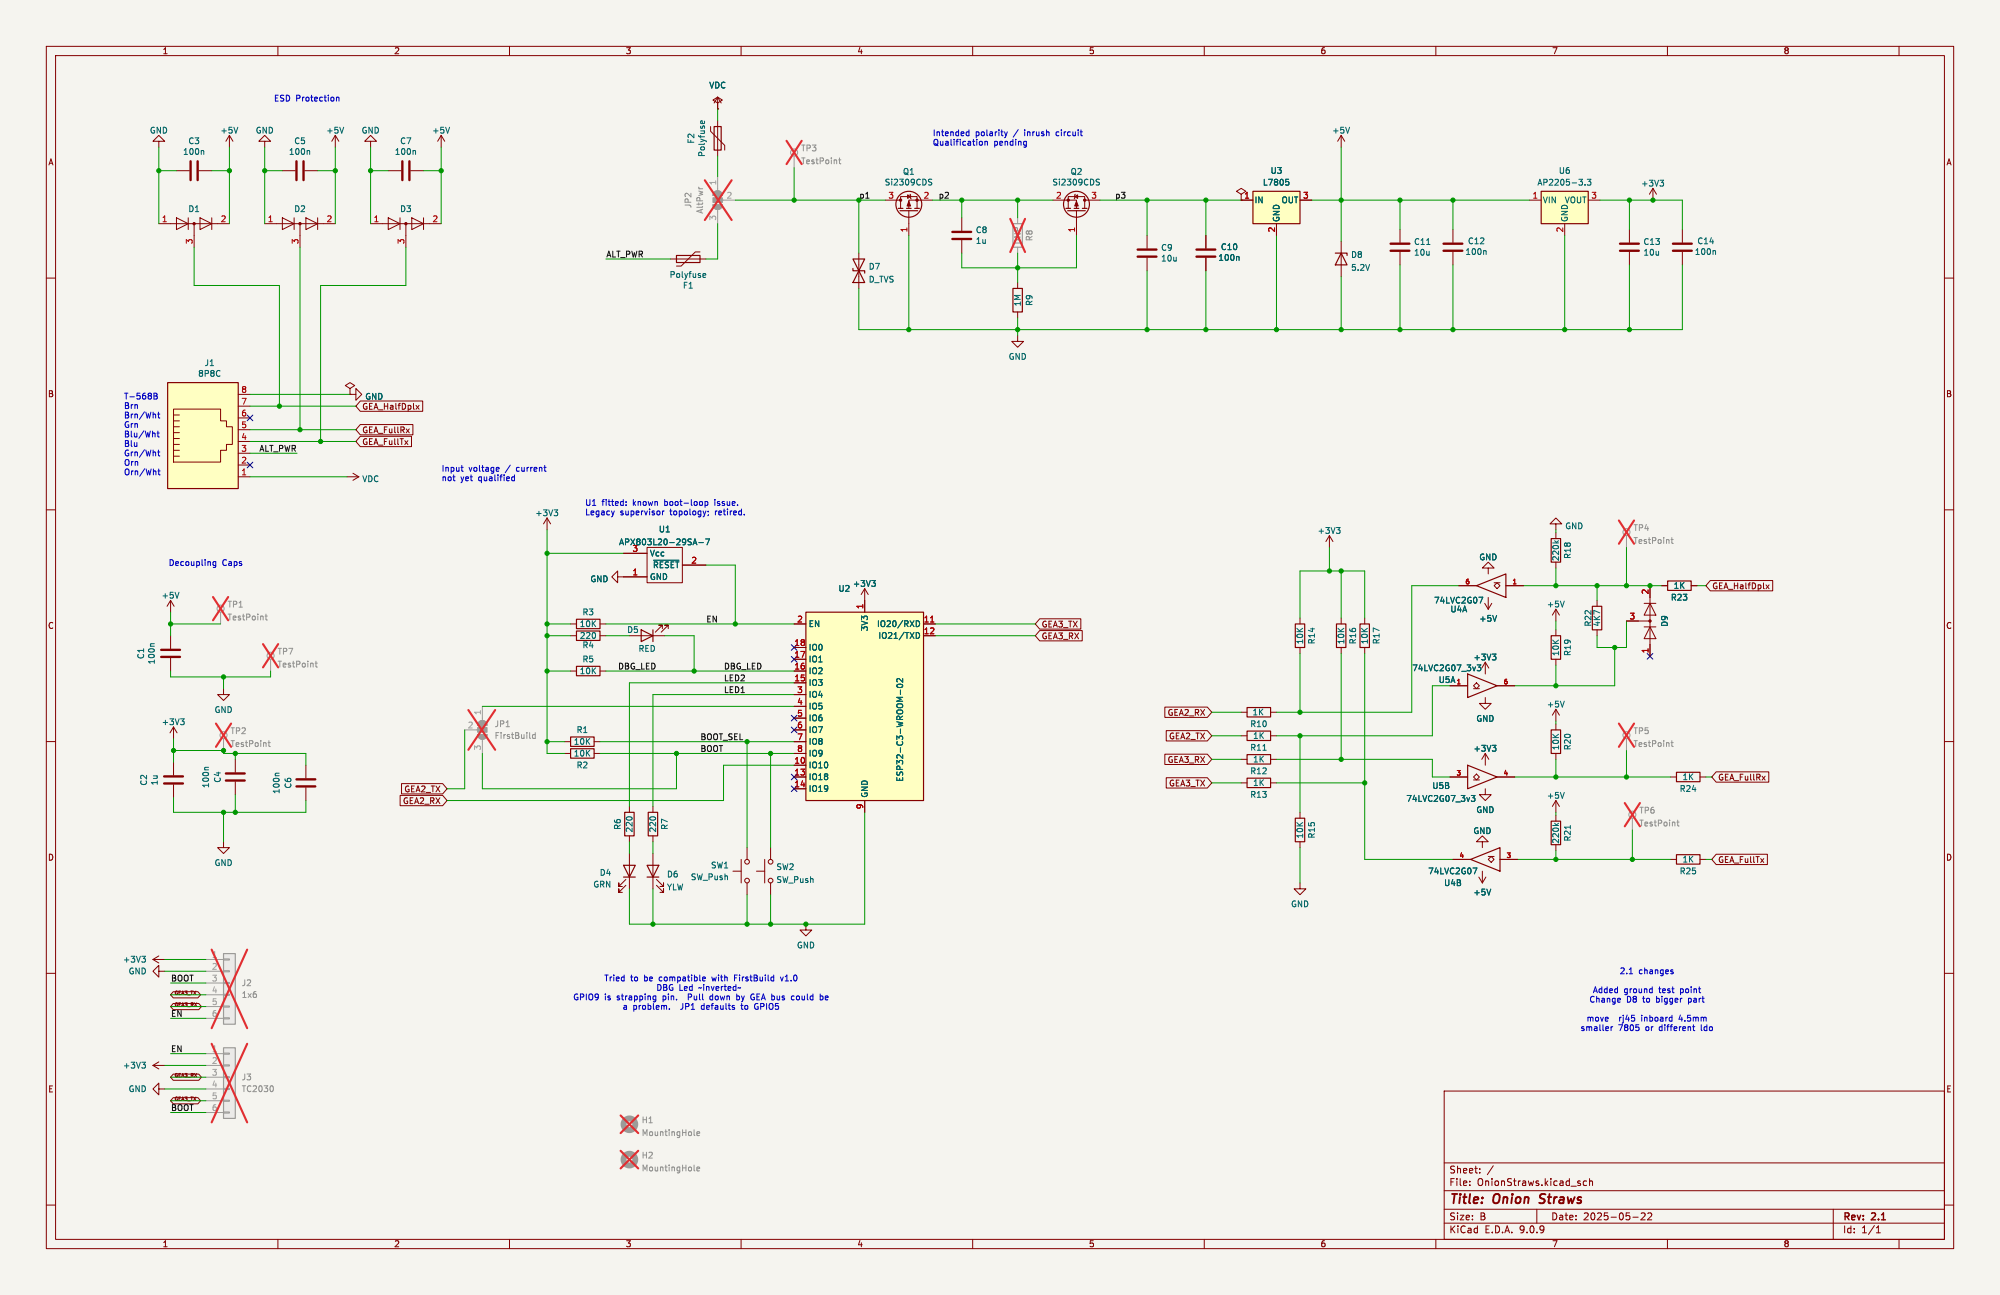
[picture p126: page 1]

2.1 changes Added ground test point

File: OnionStraws.kicad_sch Sheet: /
Id: 1/1 Title: Onion Straws
