Dr-Crow/esphome-ge-laundry-uart/pcb/rev1.0/validation/erc-normalization/after-schematic.pdf

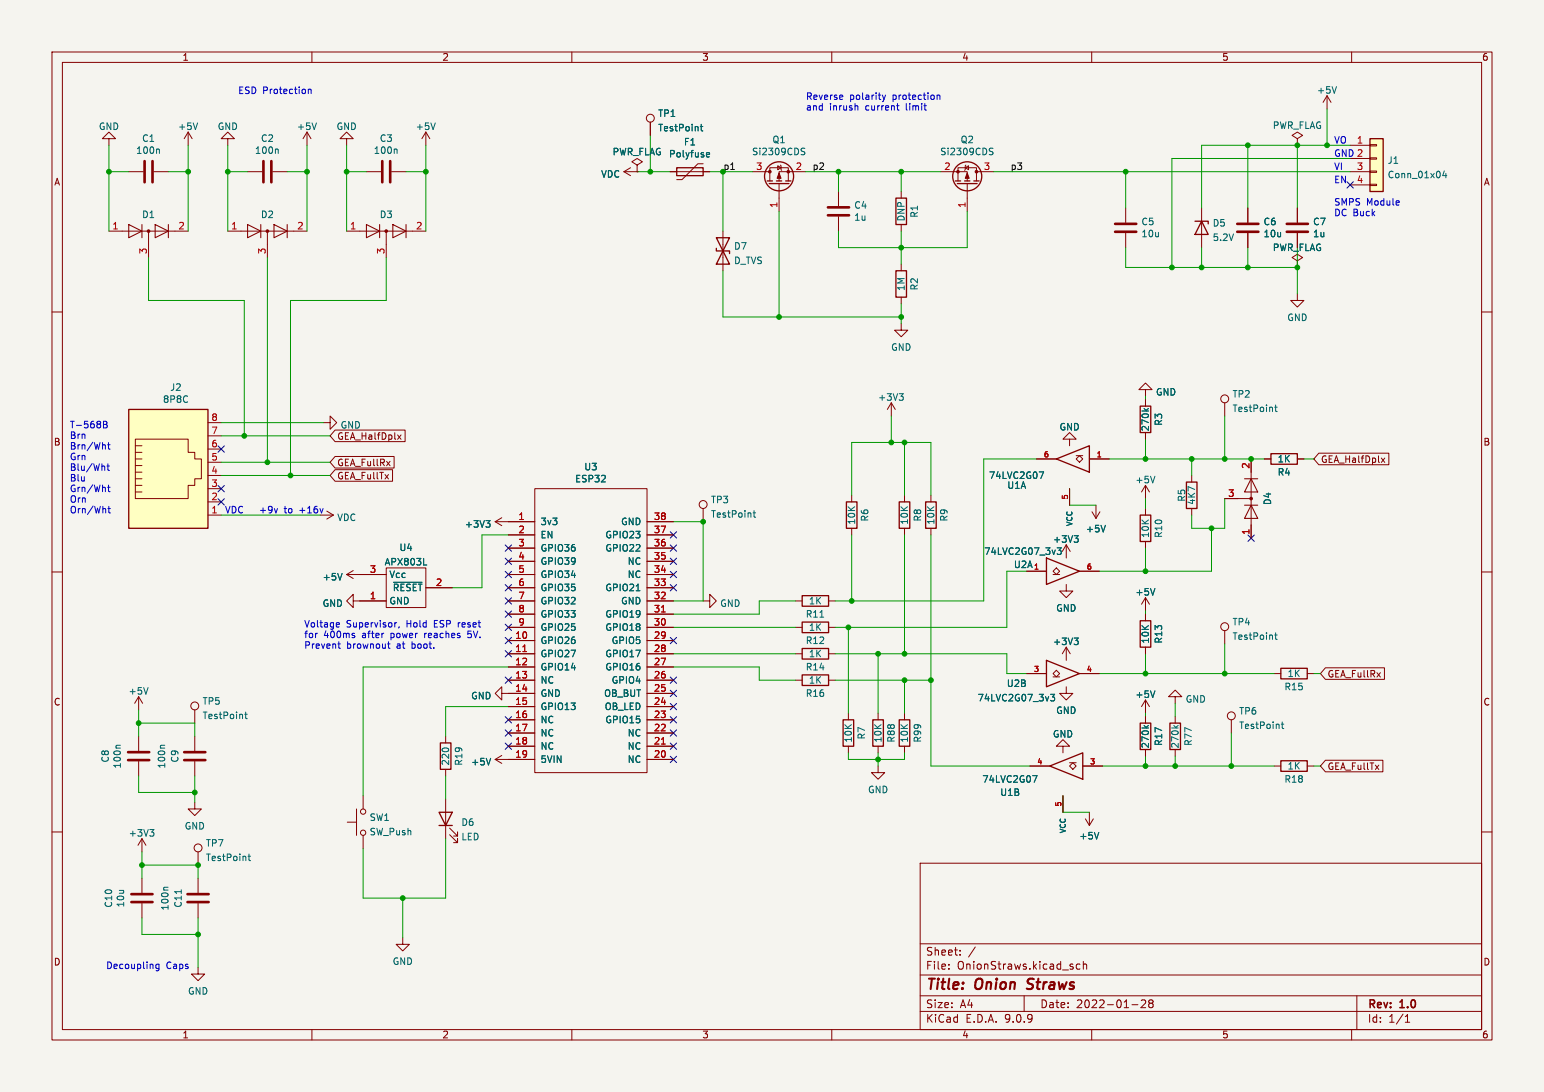
[picture p127: page 1]

Peak of 1.5 amps w/o inrush GND

File: OnionStraws.kicad_sch Sheet: / R1 DNP

SMPS Module DC Buck Washer Blk NCGrn/Rd Org BLU

Id: 1/1 Title: Onion Straws
