Dr-Crow/esphome-ge-laundry-uart/pcb/rev2.0/validation/erc-normalization/after-schematic.pdf

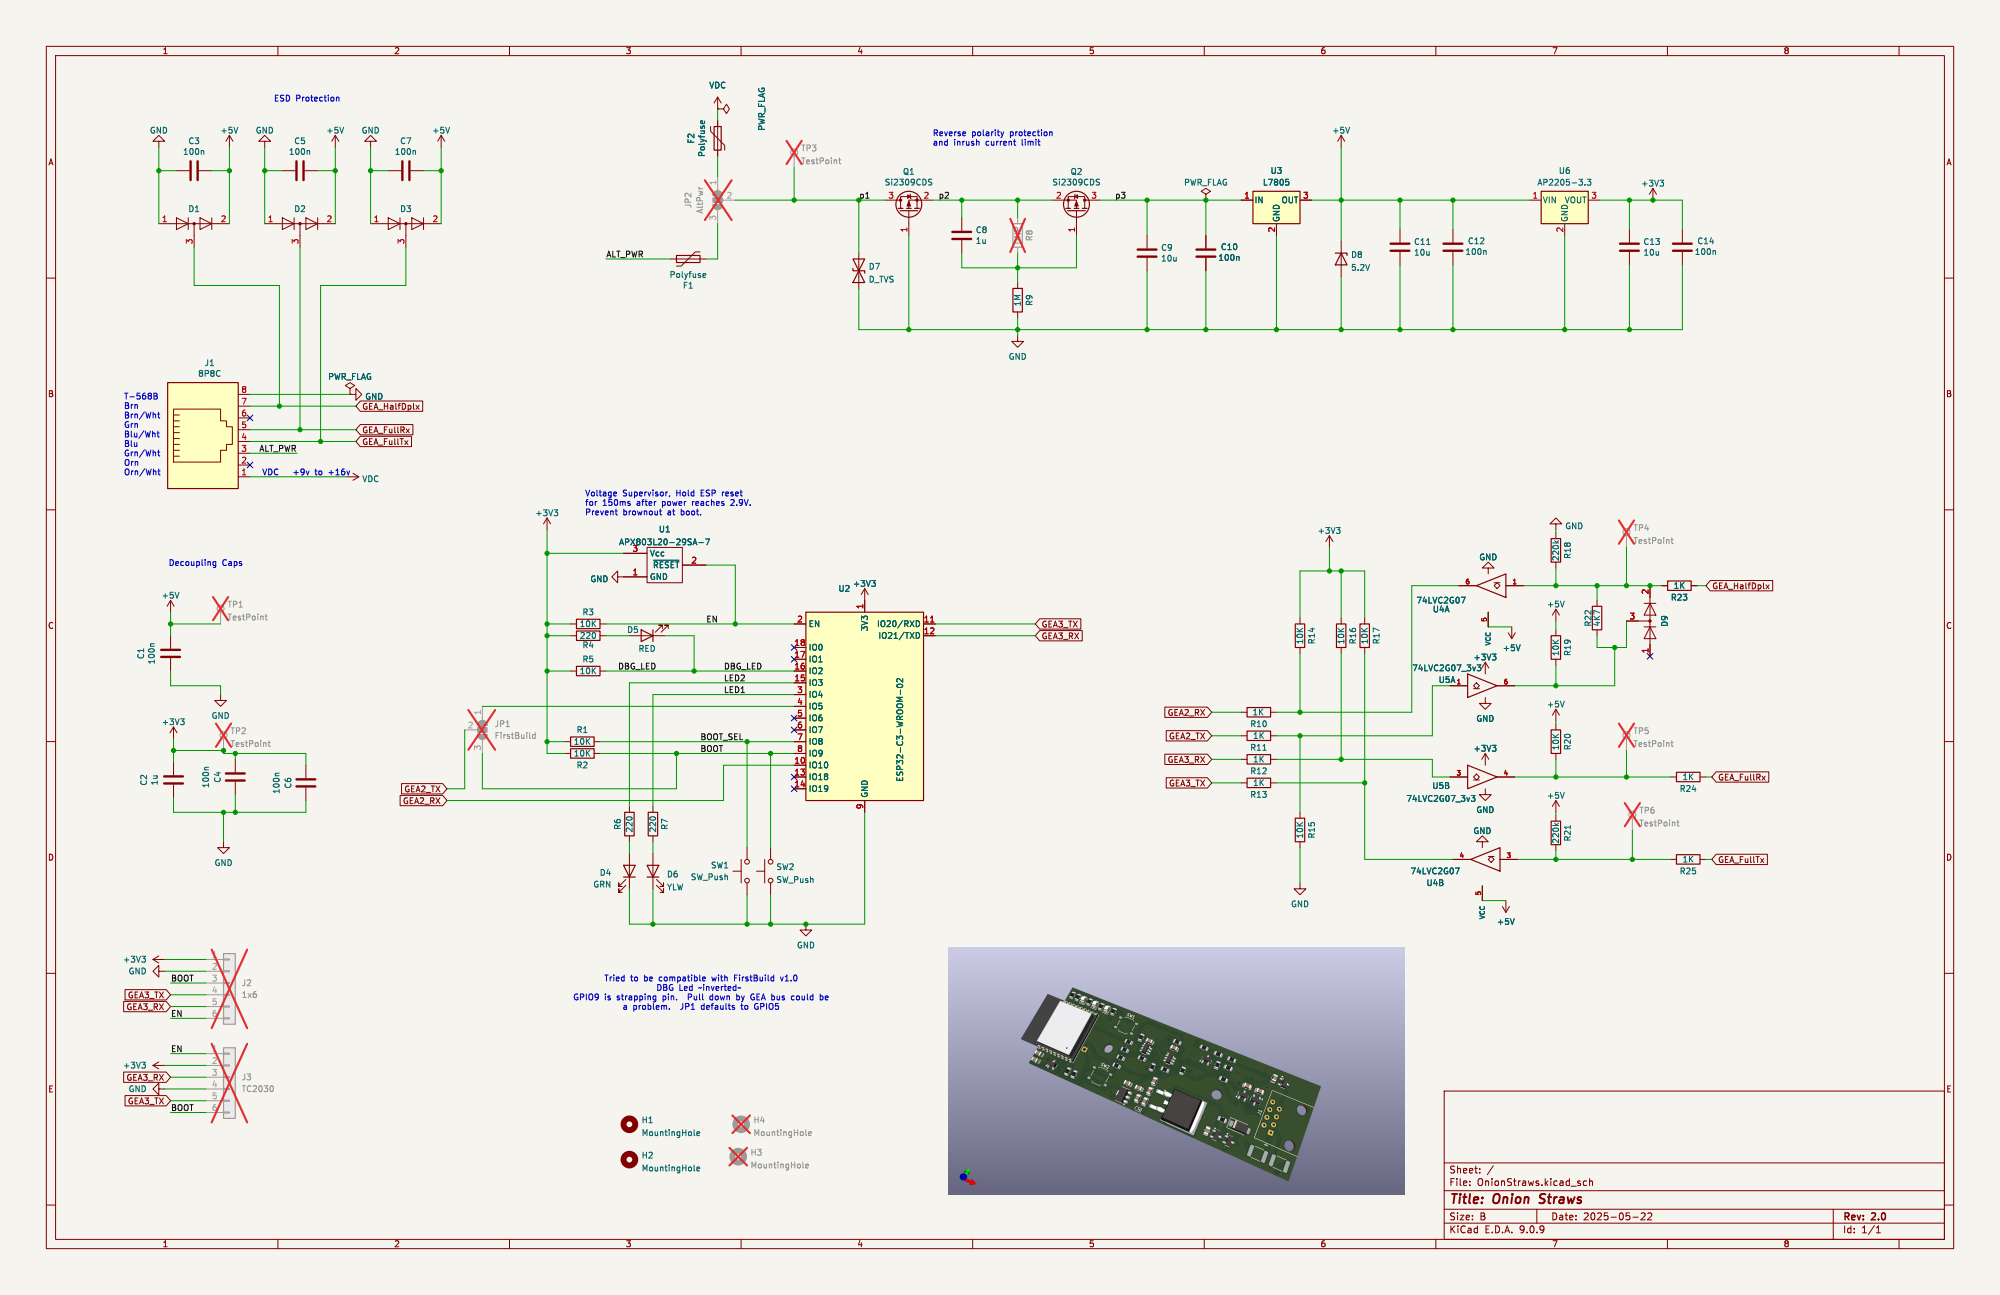
[picture p128: page 1]

Peak of 1.5 amps w/o inrush ESD Protection

Brn Brn/Wht Grn Blu/Wht Blu Grn/Wht Orn Orn/Wht Washer GND

File: OnionStraws.kicad_sch Sheet: /
Id: 1/1 Title: Onion Straws
