Dr-Crow/esphome-ge-laundry-uart/pcb/rev2.2/validation/npth-drill-map.pdf

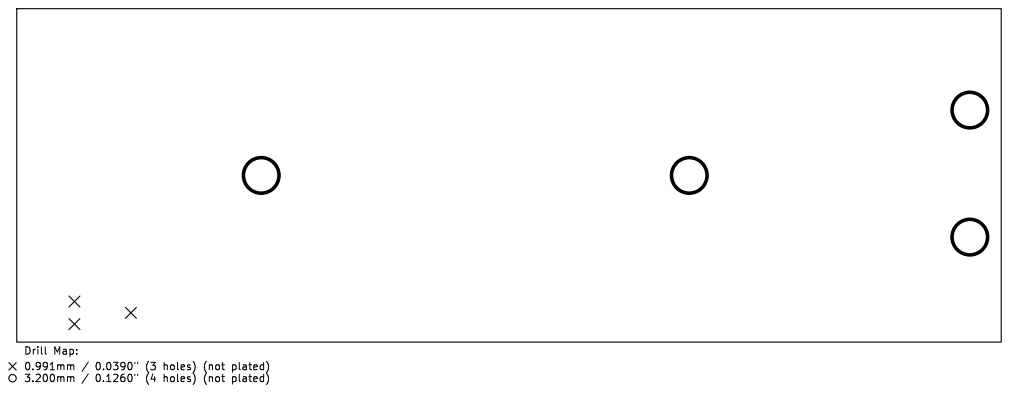
[picture p129: page 1]
