Dr-Crow/esphome-ge-laundry-uart/pcb/rev2.2/validation/pth-drill-map.pdf

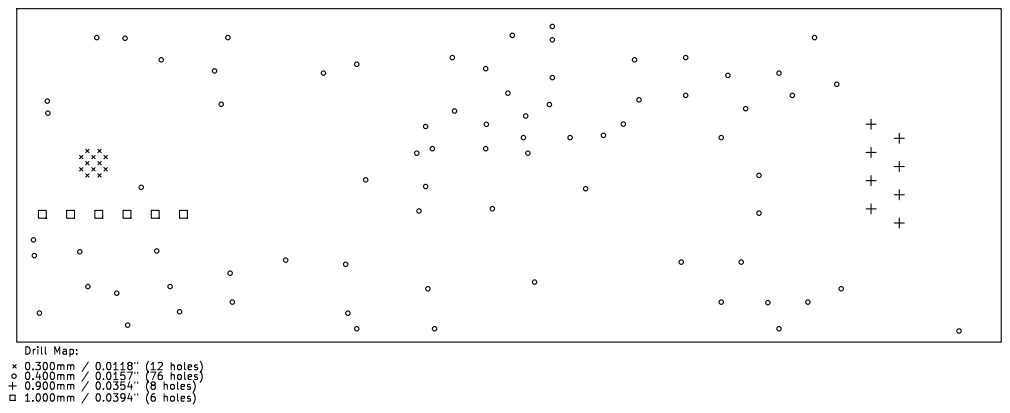
[picture p130: page 1]
