Dr-Crow/esphome-ge-laundry-uart/pcb/rev2.1/validation/pth-drill-map.pdf

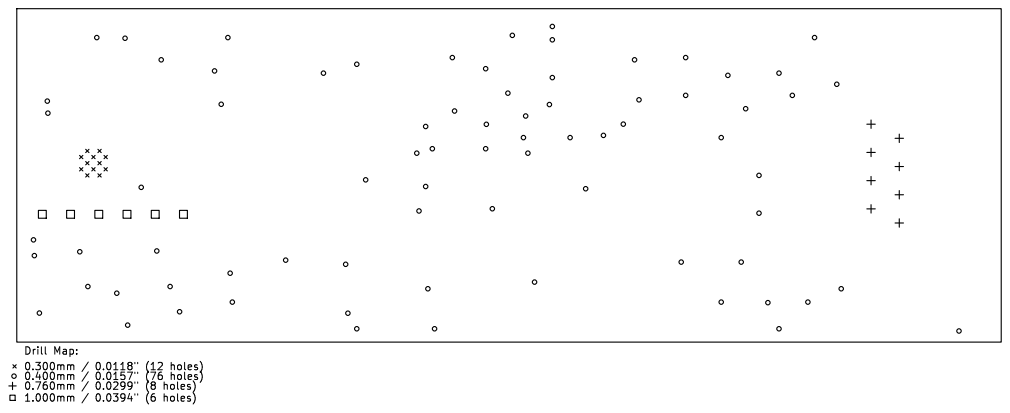
[picture p131: page 1]
