Dr-Crow/esphome-ge-laundry-uart/pcb/rev1.0/validation/board-front.pdf

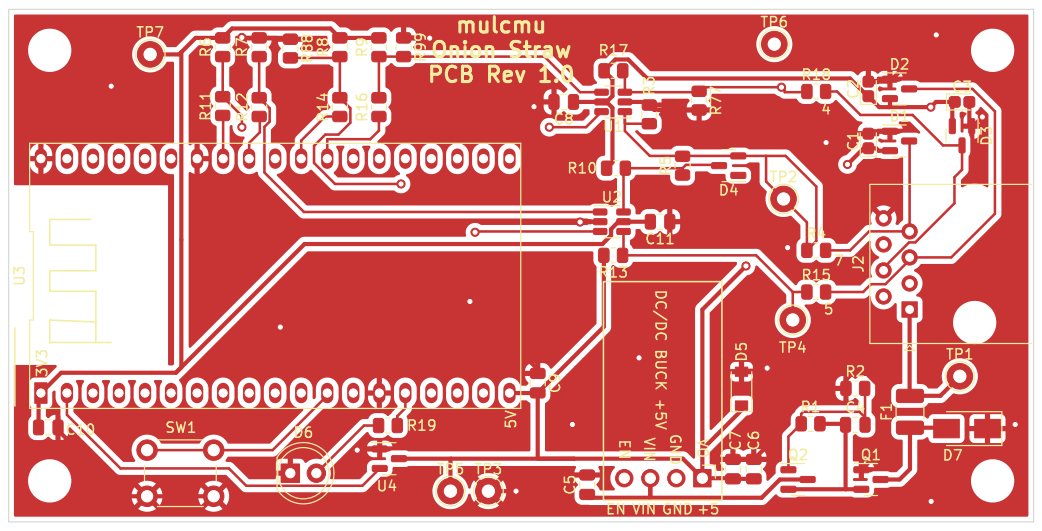
[picture p132: page 1]
