Dr-Crow/esphome-ge-laundry-uart/pcb/rev2.0/native-review/board-back.pdf

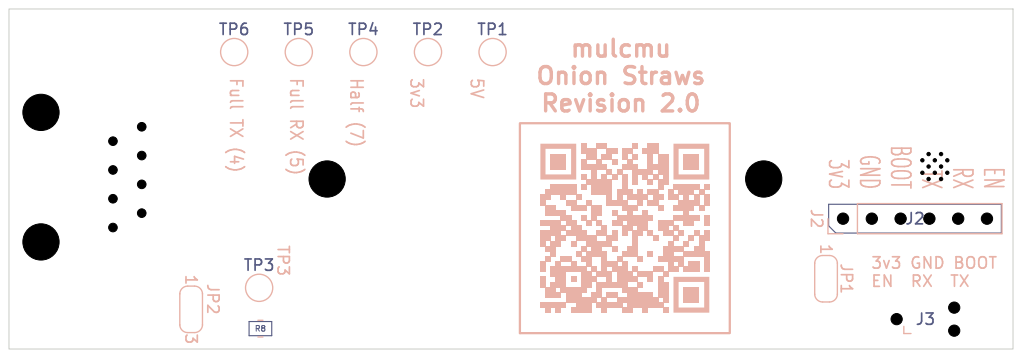
[picture p133: page 1]
