Dr-Crow/esphome-ge-laundry-uart/pcb/rev2.0/native-review/board-front.pdf

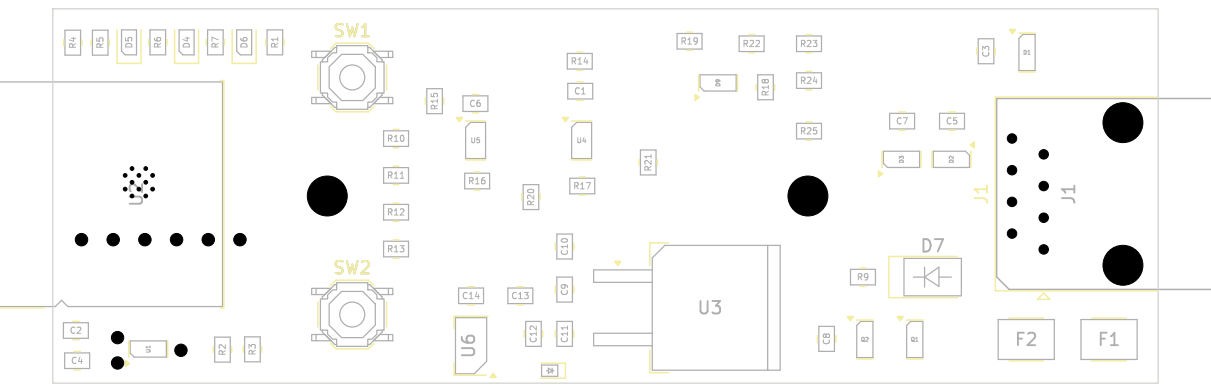
[picture p134: page 1]
