Dr-Crow/esphome-ge-laundry-uart/pcb/rev2.0/native-review/copper-layers.pdf

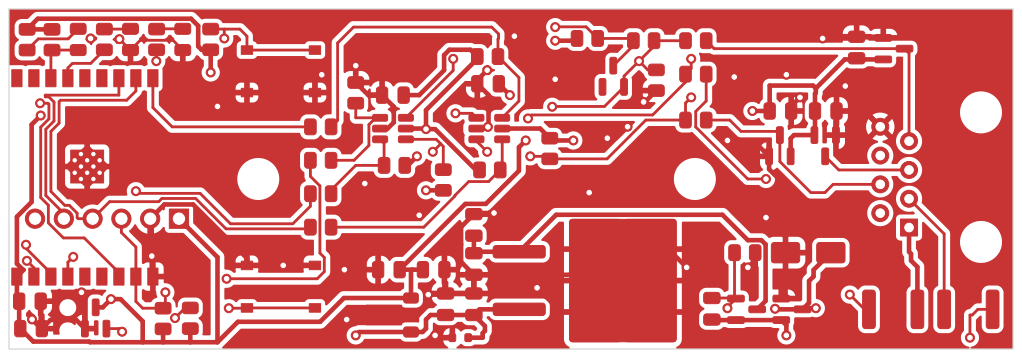
[picture p135: page 1]

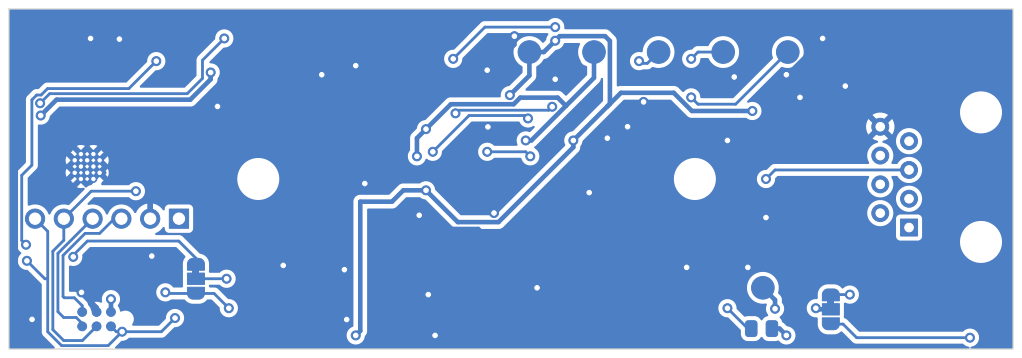
[picture p136: page 2]
